jibrilsharafi/EnergyMe-Home/openspec/changes/unified-ap-sta-provisioning/specs/wifi-provisioning/spec.md

## ADDED Requirements

### Requirement: Provisioning never blocks the WiFi task

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

#### Scenario: Credential submission with a wrong password

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

#### Scenario: AP raised while STA is down

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

### Requirement: The device serves its web interface without an upstream network

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

#### Scenario: Unprovisioned first boot

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

#### Scenario: Health check during AP-only operation

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

### Requirement: The SoftAP is raised while the device is unreachable, and only then

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

#### Scenario: Successful provisioning

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

#### Scenario: Nobody ever connects

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

#### Scenario: Device loses its network permanently

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

#### Scenario: Unprovisioned device left alone

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

#### Scenario: The AP is lowered while the device is still unreachable

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

### Requirement: Local integrations are not exposed on the SoftAP

Unauthenticated local integration services SHALL NOT accept connections arriving on the SoftAP netif.

#### Scenario: Modbus TCP during provisioning

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

### Requirement: Credential changes do not restart the device

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

#### Scenario: SSID change from the UI

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

### Requirement: New credentials can always be stored, including on a device that cannot associate

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

#### Scenario: Correcting credentials on a device in AP-assist

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

#### Scenario: The driver rejects the write

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

#### Scenario: Static IP change

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

### Requirement: Provisioning routes are reachable from the AP without the web password when unprovisioned

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

#### Scenario: Captive portal on first boot

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

#### Scenario: In-service device that lost its network

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

#### Scenario: Request arriving on the STA netif

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

#### Scenario: Reading the log while provisioning fails

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

#### Scenario: Grace period after a successful connect

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

#### Scenario: Device's own loopback health probe

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

#### Scenario: LAN host routing to the AP address

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

### Requirement: Firmware update always requires authentication

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

#### Scenario: OTA attempt from the AP while unprovisioned

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

### Requirement: The DNS responder is confined to AP-only operation

The catch-all DNS responder SHALL run only while the SoftAP is raised and STA is disconnected, and SHALL be stopped once STA connects.

#### Scenario: STA connects while the AP is still up

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

#### Scenario: AP address changed by subnet-collision avoidance

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

### Requirement: The SoftAP subnet never overlaps the STA subnet

The SoftAP SHALL be assigned a subnet that does not overlap the STA subnet, because lwIP resolves an ambiguous route to the first matching interface and a later-added interface is prepended.

#### Scenario: Router uses the default AP subnet

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

#### Scenario: Restored backup carries a foreign static IP

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

#### Scenario: Radio brought up in AP+STA mode

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

#### Scenario: Collision appears after the AP is raised

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

### Requirement: The setup page tells the user where the meter went

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

#### Scenario: Credentials accepted

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

#### Scenario: Landing on the setup page

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

### Requirement: Connection diagnostics survive the removal of the configuration portal

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

#### Scenario: Diagnosing a failed association

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

#### Scenario: Wrong password during setup

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

### Requirement: Power-cut recovery does not raise the SoftAP

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

#### Scenario: Household power cut

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

## REMOVED Requirements

### Requirement: WiFi configuration through the WiFiManager captive portal

**Reason**: Replaced by provisioning served from the device's own web interface. The WiFiManager portal blocks the WiFi task, forces a restart on credential save, presents a second unrelated UI, and serves an unauthenticated firmware-upload page.

**Migration**: Provisioning moves to the device's own interface on the SoftAP. Stored credentials are unaffected; devices with valid credentials never raise the AP and see no change. The `/diagnostic` page is replaced by a diagnostics API endpoint. Users who relied on the portal's unauthenticated OTA now authenticate with the web password; a forgotten password is still recoverable with the 5 to 10 second button press.
