jibrilsharafi/EnergyMe-Home/openspec/changes/harden-ota-download/design.md

## Context

See proposal.md - Why. The constraints that shape the approach, all verified against the code and the pinned core rather than assumed:

- The OTA download was one call to `esp_https_ota()` in `_performOtaUpdate`, driven by `_otaTask`. The task self-deletes on every exit path (now through `_finishOtaTask()`). `_performOtaUpdate` has since moved to the granular `esp_https_ota_begin()` / `_perform()` / `_finish()` sequence so the signature and image-descriptor checks can run before activation; each attempt is still one begin-to-finish pass.
- `_publishOtaStatus` (mqtt.cpp) builds `statusDetails` as a JSON object with one `reason` key. AWS IoT `UpdateJobExecution` types `statusDetails` as a string-to-string map, keys up to 128 chars matching `[a-zA-Z0-9:_-]+`, values up to 1024 chars with no control characters. Sibling keys are therefore native, and every value must be rendered as a string.
- `calculateExponentialBackoff` (utils.cpp) already exists with the signature this change needs, but lives in `src/`, which the `native` test environment cannot compile.
- `source/lib/` already holds 15 pure modules. `version_compare` is the closest template: a namespaced pure module with a thin forwarder (`compareVersions()`) left behind in utils.cpp.
- The presigned URL is minted when the device picks up the job, not when the job is created, so the device owns the full 60 minute lifetime from its own start of work.

## Goals / Non-Goals

**Goals:**

- Make a transient or one-off download failure recoverable without a new job, since the presigned URL stays valid for an hour.
- Make a failed OTA self-describing, so the next investigation reads one job execution record instead of correlating telemetry against job timestamps.
- Keep the post-download flow (partition read, SHA256 capture, preferences write, reboot) untouched.

**Non-Goals:**

- Reducing steady-state internal-heap fragmentation. That is a separate reliability concern and is not addressed here.
- Guaranteeing a download succeeds on a device whose steady-state contiguous block sits below the mbedTLS requirement. On such a device this change converts a silent failure into a described one, nothing more.
- Treating the local web-UI OTA upload path (customserver.cpp `_handleOtaUploadData()` / `_initializeOtaUpload()` / `_finalizeOtaUpload()`). It runs on the `async_tcp` task, carries no TLS, and is out of scope.

## Decisions

### No publish suppression during the download

The originating issue proposes freeing internal RAM for the download by quiescing other work. Neither half of that survived examination.

Suspending the InfluxDB, custom MQTT, UDP log, web server and Modbus TCP tasks does not survive contact with the code: ESPAsyncWebServer and eModbus have no app-owned task and both run on AsyncTCP's single shared `async_tcp` task, which calls `esp_task_wdt_add(NULL)` by default, so suspending it panic-reboots the device mid-download. InfluxDB and custom MQTT are disabled by default and hold their buffers in PSRAM, as does the UDP log queue. `vTaskSuspend` frees nothing a task has already allocated in any case.

Suppressing MQTT publishes was implemented, reviewed, and then removed. Three things sank it:

- **The bytes are not there.** Every `JsonDocument` on the publish path is built with `SpiRamAllocator`, so the body is PSRAM. The only internal-RAM allocation a publish adds is a 256-byte `BufferingPrint`. The mbedTLS out buffer is already resident for the session, and on the pinned core `CONFIG_SPIRAM_TRY_ALLOCATE_WIFI_LWIP=y` puts the outgoing lwIP pbufs in PSRAM. The 16-20 KB per-publish dip that motivated this was measured on core 3.3.11, where that flag had been dropped; it does not transfer to the reverted pin.
- **The cost is real.** The meter and grid queues are drop-oldest and hold less than the worst-case retry window, so a long schedule loses queued points rather than delaying them.
- **The fleet was already healthy.** OTAs on this platform pin were fine before the bump. The one failure on the good core was a single device with a collapsed contiguous block, which publish suppression would not have fixed.

Worth recording because the first implementation was actively harmful, not merely useless: gating inside `_checkPublishMqtt` left the log queue publishing one message per entry, and left the `_checkIfPublish*Needed` checks running every 100 ms with their "already published" markers frozen, because only the suppressed publishers advance them. Each check then logged on every tick, and those logs queued and published. The gate turned a quiet window into a publish storm, and drove `_checkIfPublishCrashNeeded` into a 10 Hz LittleFS scan contending with the OTA partition writes. Any future attempt at quiescing has to sit above the whole publish section, not inside the publishers.

The levers that would actually move the contiguous block, none of them taken here: dropping the AWS MQTT TLS session for the window (16 KB in + 16 KB out), shrinking the 9 KB `MQTT_BUFFER_SIZE`, or `CONFIG_MBEDTLS_ASYMMETRIC_CONTENT_LEN` via `custom_sdkconfig` (12 KB per connection, at platform-bump-class risk).

### Retry in `_otaTask`, not inside `_performOtaUpdate`

The loop wraps `_performOtaUpdate` so the DNS probe (`_probeOtaHost()`, called once at the top of `_otaTask`) does not re-run on every attempt. That probe opens a plaintext `WiFiClient` to port 443 purely to log whether the host resolves, and repeating it per attempt would add a socket allocation to the very heap the change is trying to protect. Keeping the loop in `_otaTask` also leaves `_performOtaUpdate` as a single-attempt function that returns enough for the caller to report on.

`_performOtaUpdate` keeps returning `bool`, but the error, HTTP status, byte progress and heap figures land in a shared `OtaAttempt` that the HTTP event handler also writes into. The handler is a C callback with no context of its own, so shared state is unavoidable there; giving it one struct rather than four loose statics keeps the reset to a single assignment.

Each attempt performs its own `esp_https_ota_begin()` (and so its own `esp_ota_begin`), so a retry restarts the write from scratch. With `bulk_flash_erase = false` the partition is erased as it goes, so a retry re-erases what the failed attempt wrote. That is slower but correct, and no partial-image state survives between attempts.

### Backoff of 5 attempts, 2 min initial, x2, capped at 15 min

Delays are 2, 4, 8 and 15 minutes (the fourth doubling to 16 is clamped), for 29 minutes of cumulative waiting. Adding attempt durations puts the worst case near 44 minutes, inside the 60 minute presigned-URL lifetime with roughly 15 minutes of margin.

Chosen over a tighter schedule because the failure being defended against is heap pressure, which does not clear in seconds, and over a longer one because the URL lifetime is a hard ceiling. `multiplier = 2` also takes the existing helper's bit-shift branch rather than its loop.

No elapsed-time guard on the total, deliberately: a guard would add a failure mode without removing one. An expired URL is instead detected directly. The OTA API collapses every 4xx and 5xx into a bare `ESP_FAIL`, so the HTTP status is captured by `_captureOtaHttpStatus()` from the HTTP event handler (on data/finish/disconnect events, not `HTTP_EVENT_ON_HEADER`, which fires before the client assigns the status), and a 4xx breaks the schedule immediately rather than spending the remaining attempts on a URL that cannot succeed.

Attempt 1 runs immediately, so the delay for attempt N is the wait *before* attempt N+1. This keeps the mapping onto `calculateExponentialBackoff(attempt, ...)`, which already returns 0 for attempt 0.

### Discrete `statusDetails` keys, not a stringified JSON blob

`statusDetails` is natively a string-to-string map, so nesting encoded JSON inside one value would force a parser onto the infra side and lose queryability. Keys, with values rendered via `snprintf` into small `char` buffers:

| Key | Value |
|---|---|
| `reason` | `download_failed` for a generic download failure; `incomplete_download` when the connection closed before the full image arrived (#233); post-download rejections carry their own reason (`signature_invalid`, `image_incompatible:<verdict>`, `finish_failed`, ...) |
| `espError` | `esp_err_to_name()` of the final attempt's return |
| `httpStatus` | from the response headers; the only field that separates a server refusal from a transport or memory failure |
| `progress` | `"<bytesReceived>/<contentLength>"`, or `n/a` when the response did not carry firmware |
| `heapFreeMinMax` | internal-heap triple in one key, same sources as `populateSystemDynamicInfo()`; omitted when not sampled (deterministic post-download rejections, see below) |
| `attempts` | attempts made |
| `uptime` | seconds |
| `rssi` | dBm |

Up to eight keys. `espError` and `progress` carry the most diagnostic weight: today an allocation failure, a DNS failure, a TLS reject and a 404 all collapse into the same `download_failed` string, and there is no way to tell a download that died at 5% from one that died at 95%.

Heap figures are sampled immediately after the failing attempt returns, inside the loop. Sampling after the loop unwinds would record recovered heap and describe the wrong moment. They are sampled only for retryable failures (`_otaFailureRetryable`): download failures, plus transient local failures during signature verification (`hash_buffer_unavailable`, `partition_error`, `invalid_image_length`, `partition_read_error`, `hash_error`). A deterministic post-download rejection (`signature_invalid`, `pubkey_parse_error`, `image_incompatible:<verdict>`, `finish_failed`) abandons the schedule, already logs its specific cause, and has nothing for heap figures to explain, so `heapFreeMinMax` is omitted rather than reported as `0/0/0` (2008981). A DEBUG log line carries the heap figures at the start and end of every attempt, visible over UDP logs before the job status arrives.

Target version, checksum, job id and device id are excluded: AWS already holds all of them.

### Extract only the backoff schedule to `source/lib/`

A new `source/lib/backoff_schedule/` module holds the pure computation, mirroring `version_compare`: a namespaced pure function, with `calculateExponentialBackoff` in `utils.cpp` reduced to a forwarder so existing callers (`influxdbclient.cpp` and the new OTA loop) are untouched.

The remaining pure helpers in `utils.cpp` (`roundToDecimals`, `isValueInRange`, `isStringLengthValid`, `endsWith`, `startsWith`, `getContentTypeFromFilename`) stay where they are. Sweeping them out is a separate concern and would turn this into a mega-commit.

### Remove the dead pause/resume API

`Ade7953::pauseTasks()` / `resumeTasks()` (ade7953.cpp / ade7953.h) had no callers anywhere in the firmware. They were the nearest precedent for the task-suspension approach this change rejects, so leaving them in place invites a future reader to reach for a pattern that was evaluated and dropped.

## Risks / Trade-offs

- **A failed job now reports up to ~44 minutes after the download starts, instead of immediately.** → Accepted deliberately. The device publishes `IN_PROGRESS` when it accepts the job, so the execution is not silent in the meantime. If a job-level timeout is configured on the AWS side it must exceed the retry window, or the execution flips to `TIMED_OUT` before the device reports. Confirm the job's `timeoutConfig` before the first fleet job on this firmware.
- **A retry re-erases and rewrites the OTA partition each attempt.** → Flash wear across 5 attempts on a firmware image is negligible against the partition's endurance, and the alternative (resuming a partial image) needs state that the failure modes here do not justify.
- **Two devices could sit in a retry schedule while a fleet job rolls on.** → No mitigation needed; each execution is independent and the rollout's own failure thresholds still apply, just on a slower clock.
- **The OTA task now lives for up to ~44 minutes instead of one download.** → It holds a 12 KB stack and re-reads `_otaCurrentUrl` on every attempt, so `stop()` no longer frees that buffer while the task is alive and notifies the task to abandon its wait instead. Telemetry, logs and shadow updates all keep flowing throughout, so a device in a retry schedule looks entirely normal from the cloud apart from the pending job.
