jibrilsharafi/EnergyMe-Home/openspec/changes/archive/2026-07-05-grid-publish-minute-alignment/design.md

## Context

`_checkIfPublishGridNeeded()` and `_publishGrid()` live in `source/src/mqtt.cpp`, called from the MQTT task's connected-state loop (`_handleConnectedState()`), which itself ticks on a shared `ulTaskNotifyTake(pdTRUE, pdMS_TO_TICKS(MQTT_LOOP_INTERVAL))` (100 ms) alongside meter/systemDynamic/statistics/log/shadow processing. Grid points are sampled by a dedicated task (`ade7953.cpp`) that self-corrects its sleep to absolute `.000`/`.500` wall-clock boundaries every tick, so each point's own `unixTimeMs` is already exact regardless of when it is later published. Today's publish trigger is `millis64() - _lastMillisGridPublished > MQTT_MAX_INTERVAL_GRID_PUBLISH` (60 s), a relative timer with no relationship to
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
