jibrilsharafi/EnergyMe-Home/hardware/pcb/kicad/main_board/EASYEDA_MODELS/WIRELM-SMD_ESP32-S3-WROOM-1.step

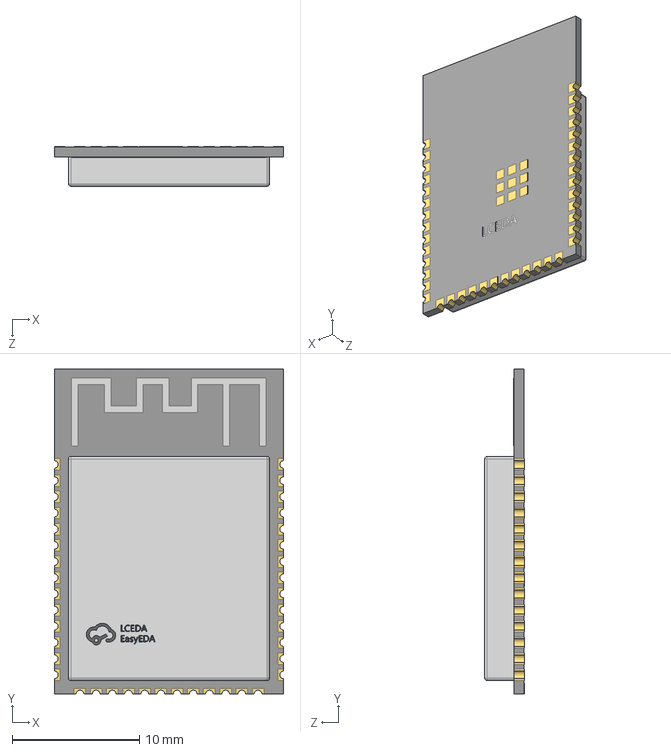
[picture p41: CAD file, 2026-09-05]
hardware/pcb/kicad/main_board/EASYEDA_MODELS/WIRELM-SMD_ESP32-S3-WROOM-1.step
18.0 x 25.5 x 3.11 mm
