jibrilsharafi/EnergyMe-Home/hardware/pcb/kicad/main_board/EASYEDA_MODELS/LFCSP-28_L5.0-W5.0-H0.8-P0.50.step

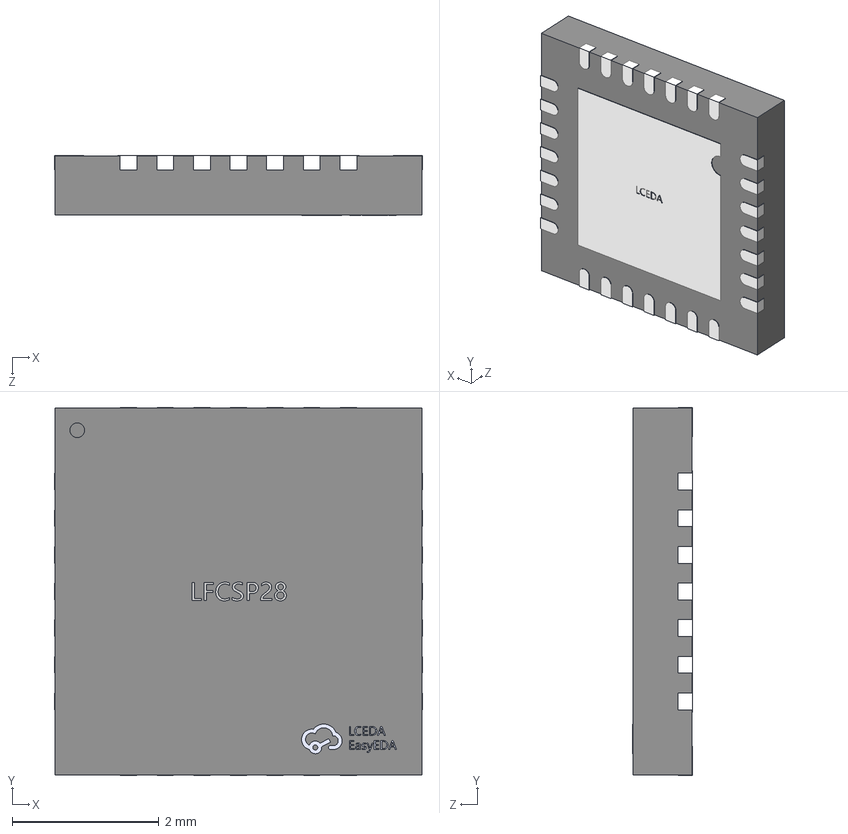
[picture p42: CAD file, 2026-09-05]
hardware/pcb/kicad/main_board/EASYEDA_MODELS/LFCSP-28_L5.0-W5.0-H0.8-P0.50.step
5.02 x 5.02 x 0.82 mm
