jibrilsharafi/EnergyMe-Home/hardware/pcb/kicad/main_board/EASYEDA_MODELS/R1206_L3.2-W1.6-H0.6.step

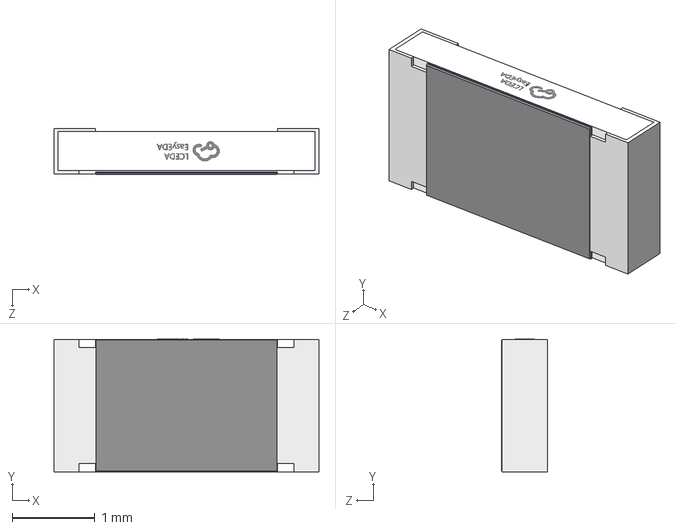
[picture p43: CAD file, 2026-09-05]
hardware/pcb/kicad/main_board/EASYEDA_MODELS/R1206_L3.2-W1.6-H0.6.step
3.20 x 1.60 x 0.56 mm
