jibrilsharafi/EnergyMe-Home/hardware/pcb/kicad/main_board/EASYEDA_MODELS/C2211_L5.7-W2.8-H1.5.step

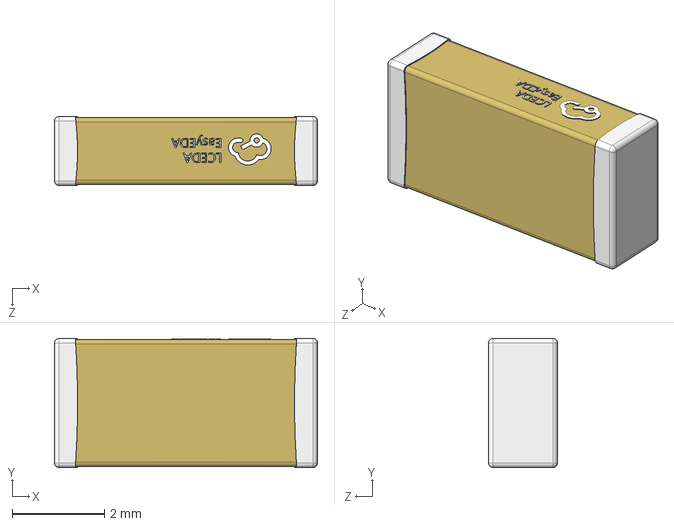
[picture p44: CAD file, 2026-09-05]
hardware/pcb/kicad/main_board/EASYEDA_MODELS/C2211_L5.7-W2.8-H1.5.step
5.70 x 2.80 x 1.50 mm
