jibrilsharafi/EnergyMe-Home/hardware/pcb/kicad/main_board/EASYEDA_MODELS/KEY-SMD_4P-L6.0-W6.0-H5.0-LS10.0-P4.50.step

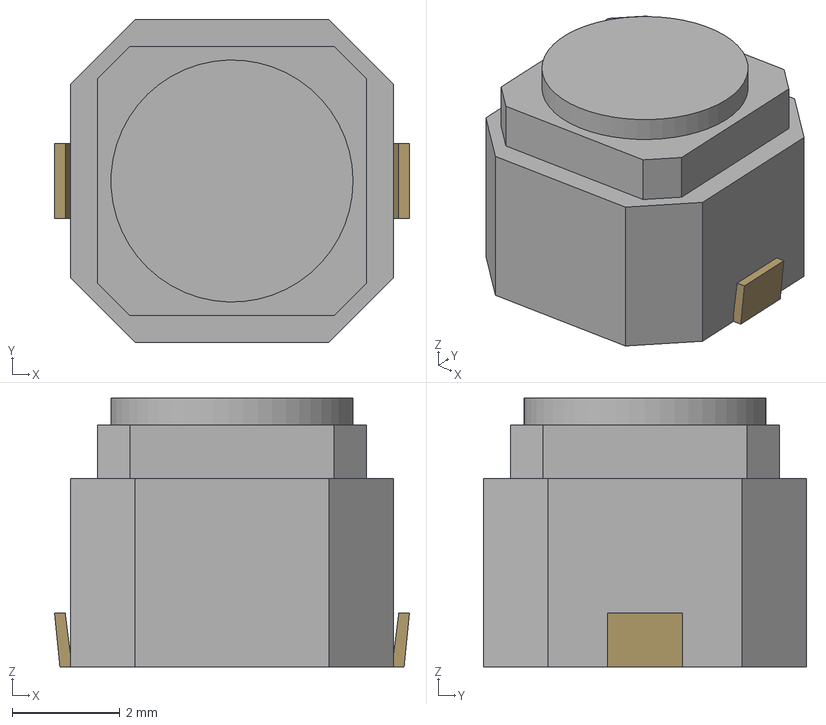
[picture p45: CAD file, 2026-09-05]
hardware/pcb/kicad/main_board/EASYEDA_MODELS/KEY-SMD_4P-L6.0-W6.0-H5.0-LS10.0-P4.50.step
6.60 x 6.00 x 5.00 mm
pin_1
pin_2
