jibrilsharafi/EnergyMe-Home/hardware/pcb/kicad/main_board/EASYEDA_MODELS/R0402_L1.0-W0.5-H0.4.step

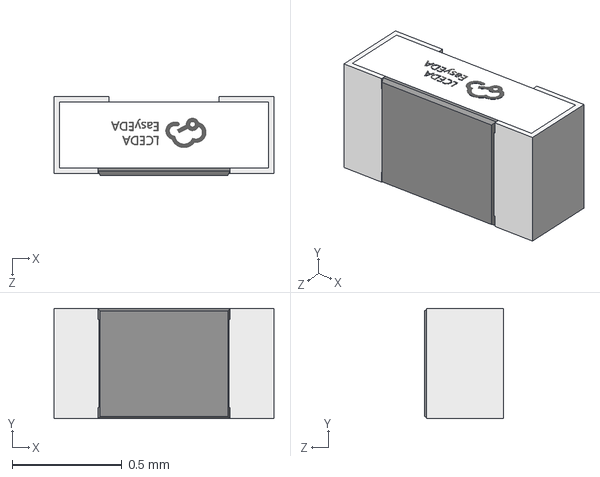
[picture p46: CAD file, 2026-09-05]
hardware/pcb/kicad/main_board/EASYEDA_MODELS/R0402_L1.0-W0.5-H0.4.step
1.00 x 0.501 x 0.36 mm
