jibrilsharafi/EnergyMe-Home/hardware/pcb/kicad/main_board/EASYEDA_MODELS/C0402_L1.0-W0.5-H0.5.step

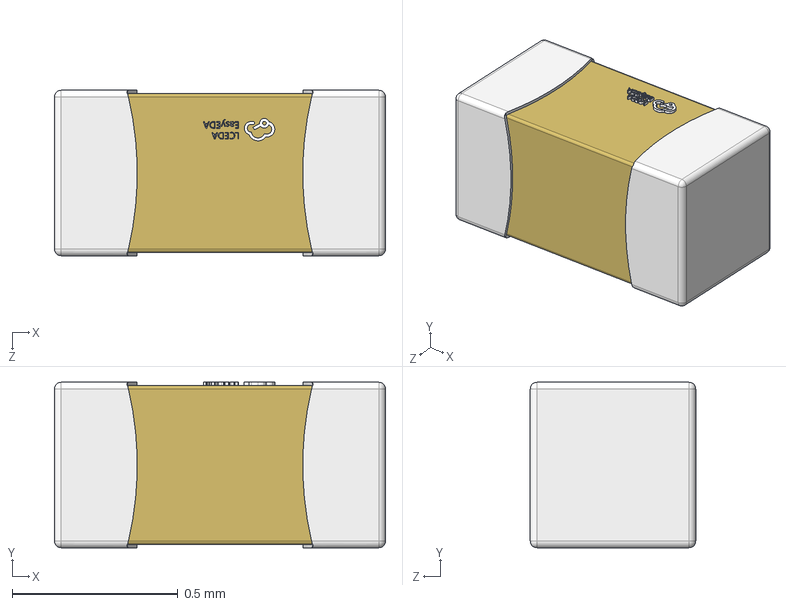
[picture p47: CAD file, 2026-09-05]
hardware/pcb/kicad/main_board/EASYEDA_MODELS/C0402_L1.0-W0.5-H0.5.step
1.00 x 0.5 x 0.5 mm
