jibrilsharafi/EnergyMe-Home/hardware/pcb/kicad/main_board/EASYEDA_MODELS/TSSOP-24_L7.8-W4.4-H1.0-LS6.4-P0.65.step

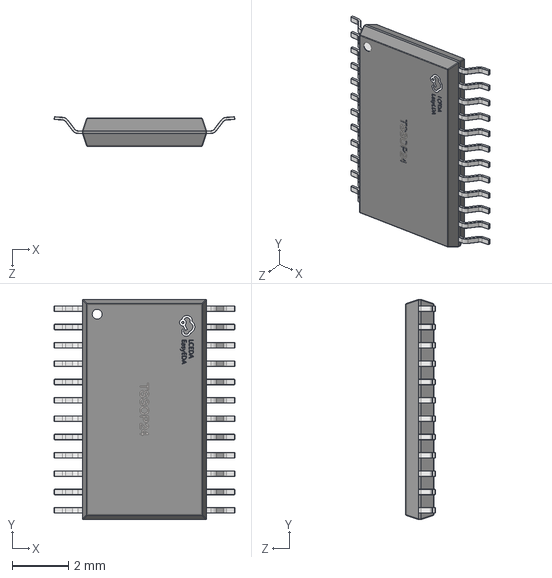
[picture p48: CAD file, 2026-09-05]
hardware/pcb/kicad/main_board/EASYEDA_MODELS/TSSOP-24_L7.8-W4.4-H1.0-LS6.4-P0.65.step
6.41 x 7.80 x 1.05 mm
