jibrilsharafi/EnergyMe-Home/manual/03-troubleshooting.md

# Troubleshooting

> *This chapter is a work in progress and will be expanded in future revisions of this manual.*

A full symptom-driven troubleshooting guide is being prepared. Anticipated sections:

- **LED behaviour** — what each colour and pattern means (cross-reference: [Appendix C](appendices.md#appendix-c-led-status-reference))
- **Wi-Fi & connectivity** — setup network doesn't appear, `energyme.local` unreachable, device drops off the network
- **Login & access** — forgot password, default credentials not accepted, temporarily locked out after repeated wrong passwords
- **Readings** — negative power values, no readings on a channel, branch sum greater than main, all zeros
- **CT placement** — symptoms suggesting a misclamped or inverted CT (cross-reference: the kettle test in [§4.7](02-setup.md#47-verification))
- **Reset procedures** — when and how to use restart, password reset, Wi-Fi reset, factory reset (cross-reference: [Appendix D](appendices.md#appendix-d-user-button-reference))
- **Firmware & updates** — update fails, the bell icon never appears, manual firmware upload
- **Hardware** — device unresponsive, CT not detected, jack issues

## In the meantime: how to get help

If you run into a problem that isn't covered elsewhere in this manual:

1. Check the **issues badge** in the top-right corner of the web interface. The device detects common problems on its own (e.g. a CT with the wrong polarity, over-temperature) and lists them there with a short explanation; channel-specific ones also appear on the **Channels** page.
2. Check the **[LED Status Reference (Appendix C)](appendices.md#appendix-c-led-status-reference)** — most installation issues are visible from the LED.
3. Try the **kettle test** described in [§4.7](02-setup.md#47-verification) to verify your wiring quickly.
4. Use the **button on the device** to recover from common situations (Wi-Fi reset, password reset); see [Appendix D](appendices.md#appendix-d-user-button-reference).
5. Compare your dashboard against the **[live demo](https://demo-energyme-home.energyme.net/)** to spot any obvious differences.

If none of the above helps, open a [GitHub issue](https://github.com/jibrilsharafi/EnergyMe-Home/issues) with:

- Your device's **batch number** (printed on the label inside the case)
- A clear description of the problem and what you have already tried
- A photograph or screenshot if relevant

We follow up on every issue and use real-world feedback to expand this troubleshooting chapter.

---

**Previous:** [← Setup](02-setup.md)  
**Next:** [Appendices →](appendices.md)
