jibrilsharafi/EnergyMe-Home/source/src/ade7953.cpp

// SPDX-License-Identifier: GPL-3.0-or-later
// Copyright (C) 2025 Jibril Sharafi

#include "ade7953.h"
#include "taskprofiler.h"
#include "duration_format.h"
#include "grid_frequency.h"
#include "mqtt.h"
#include "shadow_logic.h"

namespace Ade7953
{
    static TaskHeartbeat _meterReadingHeartbeat;
    static TaskHeartbeat _energySaveHeartbeat;
    static TaskHeartbeat _hourlyCsvHeartbeat;
    static TaskHeartbeat _gridSamplerHeartbeat;

    // Static variables
    // =========================================================
    // =========================================================
    
    // Hardware pins
    static uint8_t _ssPin;
    static uint8_t _sckPin;
    static uint8_t _misoPin;
    static uint8_t _mosiPin;
    static uint8_t _resetPin;
    static uint8_t _interruptPin;

    // Timing and measurement variables
    static uint64_t _sampleTime; // in milliseconds, time between linecycles readings
    static uint8_t _currentChannel = INVALID_CHANNEL; // By default, no channel is selected (except for channel 0 which is always active)
    // Dynamic channel scheduling state (Weighted Deficit Round-Robin)
    static float _channelWeight[MAX_CHANNEL_COUNT] = {};     // Computed dynamic weight per channel
    static float _channelDeficit[MAX_CHANNEL_COUNT] = {};    // Deficit counter for scheduling
    static float _prevActivePower[MAX_CHANNEL_COUNT] = {};   // Previous power reading for variability tracking
    static float _powerVariability[MAX_CHANNEL_COUNT] = {};  // EMA of |delta power| for variability scoring
    static uint8_t _wdrrCursor = 0;                          // Round-robin tie-break cursor for argmax
    static uint64_t _lastForcedPickMillis[MAX_CHANNEL_COUNT] = {}; // Starvation watchdog throttle, apart from lastMillis (the energy base). Guarded by _meterValuesMutex (64-bit, not atomic)
    static int8_t _polarityVoteCount[MAX_CHANNEL_COUNT] = {}; // Net consistent-sign vote accumulator for CT-reversal detection (runtime only; reset on arm/decision)
    static uint16_t _polarityConductingReads[MAX_CHANNEL_COUNT] = {}; // Conducting reads since arming - bounds a sign-oscillating channel (runtime only; reset on arm/decision)
    static bool _lastConducting[MAX_CHANNEL_COUNT] = {}; // Was the channel's most recent reading conducting (pre-clamp)? Drives the CT-detection boost so a clamped reversed load/PV still gets it (meter-task only)
    static float _gridFrequency = 50.0f; // Pre-EMA fallback, updated by the raw read in the channel-0 path

    // Per-cycle grid frequency EMA (issue #157), fed from the ZXV interrupt path.
    // Written only by the meter task; read lock-free (aligned 32-bit is atomic).
    static GridFrequency::State _gridFreqEma;
    static const GridFrequency::Config _gridFreqCfg = {GRID_FREQUENCY_CONVERSION_FACTOR, VALIDATE_GRID_FREQUENCY_MIN, VALIDATE_GRID_FREQUENCY_MAX};

    // The library returns MeterLogic::NO_CHANNEL for "no channel"; the firmware
    // compares scheduler results against its own INVALID_CHANNEL macro. They must
    // hold the same value. (The library cannot reuse the name INVALID_CHANNEL: it
    // is an object-like macro here and would rewrite MeterLogic::INVALID_CHANNEL.)
    static_assert(INVALID_CHANNEL == MeterLogic::NO_CHANNEL, "INVALID_CHANNEL / MeterLogic::NO_CHANNEL value mismatch");

    // Set by the meter task when the CT-reversal detector flips the persisted reverse flag.
    // Drained by the energy save task instead of writing NVS directly from the meter task,
    // keeping the hot meter-reading path free of flash I/O latency.
    static volatile bool _pendingPolaritySave[MAX_CHANNEL_COUNT] = {};

    // Issue-registry facts (issue #145), RAM-only and monotonic within this boot.
    // Single writer is the meter task; the registry tick reads them as 32-bit loads.
    static volatile uint32_t _factEvidenceReads[MAX_CHANNEL_COUNT] = {};
    static volatile uint32_t _factClampedEvidenceReads[MAX_CHANNEL_COUNT] = {};
    static volatile uint32_t _factPolarityFlipCount[MAX_CHANNEL_COUNT] = {};

    // Voltage-to-LSB conversion factors, computed once in begin() from globalHwProfile voltage divider.
    static float _voltPerLsb = 0.0f;
    static float _voltPerLsbInstantaneous = 0.0f;

    // Failure tracking
    static uint32_t _failureCount = 0;
    static uint64_t _firstFailureTime = 0;
    
    // Critical failure tracking (for missed interrupts)
    static uint32_t _criticalFailureCount = 0;
    static uint64_t _firstCriticalFailureTime = 0;

    // ZXTO suppression window (see _handleZxtoInterrupt). 0 = never triggered.
    static uint64_t _zxtoLastTriggerMs = 0;

    // Operational flags
    static bool _hasConfigurationChanged = false; // Flag to track if configuration has changed (needed since we will get an interrupt for CRC change)
    static bool _hasToSkipReading = true; // Flag to skip the first reading on Channel B after a mux switch so the contaminated (transition-spanning) window is discarded

    // Synchronization primitives
    static SemaphoreHandle_t _spiMutex = NULL; // To handle single SPI operations
    static SemaphoreHandle_t _spiOperationMutex = NULL; // To handle full SPI operations (like read with verification, which is 2 SPI operations)
    static SemaphoreHandle_t _ade7953InterruptSemaphore = NULL;
    static SemaphoreHandle_t _configMutex = NULL;
    static SemaphoreHandle_t _meterValuesMutex = NULL;
    static SemaphoreHandle_t _channelDataMutex = NULL;

    // FreeRTOS task handles and control flags
    static TaskHandle_t _meterReadingTaskHandle = NULL;
    static bool _meterReadingTaskShouldRun = false;
    
    static TaskHandle_t _energySaveTaskHandle = NULL;
    static bool _energySaveTaskShouldRun = false;
    
    static TaskHandle_t _hourlyCsvSaveTaskHandle = NULL;
    static bool _hourlyCsvSaveTaskShouldRun = false;

    static TaskHandle_t _gridSamplerTaskHandle = NULL;
    static bool _gridSamplerTaskShouldRun = false;

    static SemaphoreHandle_t _historyClearMutex = NULL;

    // Waveform capture state and buffers
    static CaptureState _captureState = CaptureState::IDLE;
    static uint8_t _captureRequestedChannel = INVALID_CHANNEL;
    static uint8_t _captureChannel = INVALID_CHANNEL;  // The channel being actively captured
    static uint16_t _captureSampleCount = 0;
    static uint64_t _captureStartUnixMillis = 0;
    static uint64_t _captureStartMicros = 0;  // Microseconds timestamp at capture start
    static int32_t* _voltageWaveformBuffer = nullptr;
    static int32_t* _currentWaveformBuffer = nullptr;
    static uint64_t* _microsWaveformBuffer = nullptr;  // Microseconds delta from start for each sample

    // Configuration and data arrays
    static Ade7953Configuration _configuration;
    MeterValues _meterValues[MAX_CHANNEL_COUNT];
    EnergyValues _energyValues[MAX_CHANNEL_COUNT]; // Store previous energy values for energy comparisons (optimize saving to flash)
    ChannelData _channelData[MAX_CHANNEL_COUNT];
    static uint16_t _lineFrequency = DEFAULT_FALLBACK_FREQUENCY; // Line frequency (fixed 50 or 60 Hz value)

    // Private function declarations
    // =========================================================
    // =========================================================

    // Hardware initialization and control
    static void _setHardwarePins(
        uint8_t ssPin,
        uint8_t sckPin,
        uint8_t misoPin,
        uint8_t mosiPin,
        uint8_t resetPin,
        uint8_t interruptPin
    );
    static void _reset();
    // According to the datasheet, setting these registers is mandatory for optimal operation
    static void _setOptimumSettings();
    static void _setDefaultParameters();

    // System management
    static void _initializeMutexes();
    static void _cleanup();
    static bool _verifyCommunication();

    // Interrupt handling
    static void _setupInterrupts();
    static void _handleInterrupt(uint64_t linecycUnix);
    static void _attachInterruptHandler();
    static void _detachInterruptHandler();
    static void IRAM_ATTR _isrHandler();
    static void _handleZxvInterrupt();
    static void _handleCycendInterrupt(uint64_t linecycUnix);
    static void _pollWaveformSamples();
    static void _handleCrcChangeInterrupt();
    static void _handleResetInterrupt();
    static void _handleZxtoInterrupt();

    // Task management
    static void _startMeterReadingTask();
    static void _stopMeterReadingTask();
    static void _meterReadingTask(void* parameter);

    static void _startEnergySaveTask();
    static void _stopEnergySaveTask();
    static void _energySaveTask(void* parameter);

    static void _startHourlyCsvSaveTask();
    static void _stopHourlyCsvSaveTask();
    static void _hourlyCsvSaveTask(void* parameter);

    static void _startGridSamplerTask();
    static void _stopGridSamplerTask();
    static void _gridSamplerTask(void* parameter);

    static void _historyClearTask(void* parameter);
    static void _spawnHistoryClearTask(uint8_t channelIndex);
    static void _clearAllHistoricalData();

    // Configuration management
    static void _seedConfigurationFromFactory();
    static void _setConfigurationFromPreferences();
    static void _saveConfigurationToPreferences();
    static void _applyConfiguration(const Ade7953Configuration &config); // Apply all the single register values from the configuration
    static bool _validateJsonConfiguration(const JsonDocument &jsonDocument, bool partial = false);

    // Channel data management
    static void _setChannelDataFromPreferences(uint8_t channelIndex);
    static bool _saveChannelDataToPreferences(uint8_t channelIndex);
    static void _updateChannelData(uint8_t channelIndex);
    static bool _validateChannelDataJson(const JsonDocument &jsonDocument, bool partial = false);
    static void _calculateLsbValues(CtSpecification &ctSpec);

    // Energy data management
    static void _setEnergyFromPreferences(uint8_t channelIndex);
    static void _saveEnergyToPreferences(uint8_t channelIndex, bool forceSave = false); // Needed for saving data anyway on first setup (energy is 0 and not saved otherwise)
    static void _clearStartMeasuring(uint8_t channelIndex); // reset back to 0 (unset) on every reset
    static void _saveHourlyEnergyToCsv(); // Not per channel so that we open the file only once
    static void _saveEnergyComplete();
    static bool _clearChannelHistoricalData(uint8_t channelIndex);

    // Meter reading and processing
    static bool _readMeterValues(uint8_t channelIndex, uint64_t linecycUnixTime);
    static bool _processChannelReading(uint8_t channelIndex, uint64_t linecycUnix);
    static void _addMeterDataToPayload(uint8_t channelIndex);

    // ADE7953 register writing functions
    static void _setLinecyc(uint32_t linecyc);
    static void _setPgaGain(int32_t pgaGain, Ade7953Channel ade7953Channel, MeasurementType measurementType);
    static void _setPhaseCalibration(int32_t phaseCalibration, Ade7953Channel ade7953Channel);
    static void _setGain(int32_t gain, Ade7953Channel ade7953Channel, MeasurementType measurementType);
    static void _setOffset(int32_t offset, Ade7953Channel ade7953Channel, MeasurementType measurementType);

    // Sample time management
    static void _updateSampleTime();
    static void _setSampleTimeFromPreferences();
    static void _saveSampleTimeToPreferences();

    // ADE7953 register reading functions
    /*
    This allows you see the actual sinusoidal waveform, so both positive and 
    negative values. At full scale (so 500 mV), the value returned is 9032007d.

    @param channel The channel to read from. Either CHANNEL_A or CHANNEL_B.
    @return The actual instantaneous current in LSB.
    */
    static int32_t _readCurrentInstantaneous(Ade7953Channel ade7953Channel);
    /*
    Reads the actual instantaneous voltage. 

    This allows you 
    to see the actual sinusoidal waveform, so both positive
    and negative values. At full scale (so 500 mV), the value
    returned is 9032007d.

    @return The actual instantaneous voltage in LSB.
    */
    static int32_t _readVoltageInstantaneous();
    /*
    Reads the current in RMS.

    This measurement is updated at 6.99 kHz and has a settling
    time of 200 ms. The value is in LSB.

    @param channel The channel to read from. Either CHANNEL_A or CHANNEL_B.
    @return The current in RMS in LSB.
    */
    static int32_t _readCurrentRms(Ade7953Channel ade7953Channel);
    /*
    Reads the voltage in RMS.

    This measurement is updated at 6.99 kHz and has a settling
    time of 200 ms. The value is in LSB.

    @return The voltage in RMS in LSB.
    */
    static int32_t _readVoltageRms();
    static int32_t _readActiveEnergy(Ade7953Channel ade7953Channel);
    static int32_t _readReactiveEnergy(Ade7953Channel ade7953Channel);
    static int32_t _readApparentEnergy(Ade7953Channel ade7953Channel);
    static int32_t _readPeriod();
    static float _readGridFrequency();

    // Verification and validation functions
    static void _recordFailure();
    static void _checkForTooManyFailures();
    static void _recordCriticalFailure();
    static void _checkForTooManyCriticalFailures();
    static bool _verifyLastSpiCommunication(uint16_t expectedAddress, uint8_t expectedBits, int32_t expectedData, bool signedData, bool wasWrite);
    static bool _validateVoltage(float newValue);
    static bool _validateCurrent(float newValue);
    static bool _validatePower(float newValue);
    static bool _validatePowerFactor(float newValue);
    static bool _validateGridFrequency(float newValue);

    // Utility functions
    static void _recalculateWeights();
    static void _updateVariability(uint8_t channelIndex, float newActivePower);
    static uint8_t _findNextActiveChannel(uint8_t currentChannel);
    float _calculatePhaseShift(Phase voltagePhase, Phase currentPhase);
    // Returns the string name of the IRQSTATA bit, or UNKNOWN if the bit is not recognized.
    static const char *_irqstataBitName(uint32_t bit);
    void _printMeterValues(uint8_t channelIndex);


    // Public API functions
    // =========================================================
    // =========================================================

    // Core lifecycle management
    // =========================

    bool begin(
        uint8_t ssPin,
        uint8_t sckPin,
        uint8_t misoPin,
        uint8_t mosiPin,
        uint8_t resetPin,
        uint8_t interruptPin
    ) {
        LOG_DEBUG("Initializing Ade7953");

        _initializeMutexes();
        LOG_DEBUG("Initialized SPI mutexes");

        // Allocate PSRAM buffers for waveform capture
        _voltageWaveformBuffer = (int32_t*)ps_malloc(WAVEFORM_BUFFER_SIZE * sizeof(int32_t));
        _currentWaveformBuffer = (int32_t*)ps_malloc(WAVEFORM_BUFFER_SIZE * sizeof(int32_t));
        _microsWaveformBuffer = (uint64_t*)ps_malloc(WAVEFORM_BUFFER_SIZE * sizeof(uint64_t));

        if (!_voltageWaveformBuffer || !_currentWaveformBuffer || !_microsWaveformBuffer) {
            LOG_ERROR("Failed to allocate waveform buffers from PSRAM");
            _captureState = CaptureState::ERROR;
            // Continue initialization - waveform capture just won't be available
        } else {
            LOG_DEBUG("Allocated waveform buffers in PSRAM (%u samples)", WAVEFORM_BUFFER_SIZE);
        }
      
        _setHardwarePins(ssPin, sckPin, misoPin, mosiPin, resetPin, interruptPin);
        LOG_DEBUG("Successfully set up hardware pins");

        // Compute voltage-per-LSB from the hardware profile's voltage divider values.
        // ratio = R2 / (R1 + R2), the fraction of the mains voltage seen by the ADE7953 input.
        const float ratio = globalHwProfile->voltageDividerR2 / (globalHwProfile->voltageDividerR1 + globalHwProfile->voltageDividerR2);
        _voltPerLsb             = (MAXIMUM_ADC_CHANNEL_INPUT / 1.41421356f) / ratio / static_cast<float>(FULL_SCALE_LSB_FOR_RMS_VALUES);
        _voltPerLsbInstantaneous = MAXIMUM_ADC_CHANNEL_INPUT / ratio / static_cast<float>(FULL_SCALE_LSB_FOR_INSTANTANEOUS_VALUES);

        if (!_verifyCommunication()) {
            LOG_ERROR("Failed to communicate with ADE7953");
            return false;
        }
        LOG_DEBUG("Communication with ADE7953 verified");
                
        _setOptimumSettings();
        LOG_DEBUG("Set optimum settings");
        
        _setDefaultParameters();
        LOG_DEBUG("Set default parameters");

        _seedConfigurationFromFactory();
        _setConfigurationFromPreferences();
        LOG_DEBUG("Done setting configuration from Preferences");

        _setSampleTimeFromPreferences();
        LOG_DEBUG("Done setting sample time from Preferences");

        for (uint8_t i = 0; i < globalHwProfile->totalChannelCount; i++) {
            _setChannelDataFromPreferences(i);
        }
        LOG_DEBUG("Done setting channel data from Preferences");

        for (uint8_t i = 0; i < globalHwProfile->totalChannelCount; i++) {
            _setEnergyFromPreferences(i);
        }
        LOG_DEBUG("Done setting energy from Preferences");

        _setupInterrupts();
        LOG_DEBUG("Set up interrupts");

        _startMeterReadingTask();
        LOG_DEBUG("Meter reading task started");

        _startEnergySaveTask();
        LOG_DEBUG("Energy save task started");

        _startHourlyCsvSaveTask();
        LOG_DEBUG("Hourly CSV save task started");

        _startGridSamplerTask();
        LOG_DEBUG("Grid sampler task started");

        return true;
    }

    void stop() {
        LOG_DEBUG("Stopping ADE7953...");
        
        // Clean up resources (where the data will also be saved)
        _cleanup();

        // Mutexes are kept: Modbus, MQTT and web handlers can still be inside getters while the
        // restart sequence runs, and deleting a mutex in use trips a FreeRTOS assert. A reboot follows.
        
        LOG_DEBUG("ADE7953 stopped successfully");
    }

    // Register operations
    // ===================

    int32_t readRegister(uint16_t registerAddress, uint8_t nBits, bool signedData, bool isVerificationRequired) {
        // Ensure the bits are valid (must be 8, 16, 24, or 32 bits)
        if (nBits != BIT_8 && nBits != BIT_16 && nBits != BIT_24 && nBits != BIT_32) {
            LOG_ERROR(
                "Invalid number of bits (%u) for register read operation on register %ld (0x%04lX)",
                nBits, registerAddress, registerAddress
            );
            return INVALID_SPI_READ_WRITE; // Return an invalid value
        }

        // If we need to verify, ensure we are able to take the full SPI operation mutex
        if (isVerificationRequired) {
            if (!acquireMutex(&_spiOperationMutex, ADE7953_SPI_OPERATION_MUTEX_TIMEOUT_MS)) {
                LOG_ERROR("Failed to acquire SPI operation mutex for read operation on register %ld (0x%04lX)", registerAddress, registerAddress);
                return INVALID_SPI_READ_WRITE;
            }
        }

        // Acquire direct SPI mutex
        if (!acquireMutex(&_spiMutex, ADE7953_SPI_MUTEX_TIMEOUT_MS)) {
            LOG_ERROR("Failed to acquire SPI mutex for read operation on register %ld (0x%04lX)", registerAddress, registerAddress);
            if (isVerificationRequired) releaseMutex(&_spiOperationMutex);
            return INVALID_SPI_READ_WRITE;
        }

        // Signal the start of the SPI operation
        digitalWrite(_ssPin, LOW);

        // Send the register address (two 8-bit transfers) and read command
        // Note: The register address is sent in big-endian format (MSB first)
        SPI.transfer((uint8_t)(registerAddress >> 8));
        SPI.transfer((uint8_t)(registerAddress & 0xFF));
        SPI.transfer((uint8_t)(READ_TRANSFER));

        // Create the array of bytes to read (one element per each 8 bits)
        uint8_t response[nBits / 8];
        for (uint8_t i = 0; i < nBits / 8; i++) {
            response[i] = SPI.transfer((uint8_t)(READ_TRANSFER)); // Read the data byte by byte
        }

        // Signal the end of the SPI operation
        digitalWrite(_ssPin, HIGH);

        releaseMutex(&_spiMutex); // Leave as soon as possible since no more direct SPI operations are needed

        // Compose the raw response from the byte array
        uint32_t rawResponse = 0;
        for (uint8_t i = 0; i < nBits / 8; i++) {
            rawResponse = (rawResponse << 8) | response[i];
        }

        int32_t longResponse = signedData ? MeterLogic::signExtendRegister(rawResponse, nBits) : (int32_t)rawResponse;

        // Verify the data if required by reading the dedicated ADE7953 register
        if (isVerificationRequired) {
            if (!_verifyLastSpiCommunication(registerAddress, nBits, longResponse, signedData, false)) {
                LOG_DEBUG("Failed to verify last read communication for register %lu (0x%04lX). Value was %ld (0x%04lX)", registerAddress, registerAddress, longResponse, longResponse);
                _recordFailure();
                longResponse = INVALID_SPI_READ_WRITE; // Return an invalid value if verification fails
            }
            releaseMutex(&_spiOperationMutex);
        }

        LOG_VERBOSE(
            "Read successfully %ld from register %lu with %u bits",
            longResponse,
            registerAddress,
            nBits
        );
        return longResponse;
    }

    void writeRegister(uint16_t registerAddress, uint8_t nBits, int32_t data, bool isVerificationRequired) {
        // Ensure the bits are valid (must be 8, 16, 24, or 32 bits)
        if (nBits != BIT_8 && nBits != BIT_16 && nBits != BIT_24 && nBits != BIT_32) {
            LOG_ERROR(
                "Invalid number of bits (%u) for register write operation on register %ld (0x%04lX)",
                nBits, registerAddress, registerAddress
            );
            return; // Return an invalid value
        }

        // If we need to verify, ensure we are able to take the full SPI operation mutex
        if (isVerificationRequired) {
            if (!acquireMutex(&_spiOperationMutex, ADE7953_SPI_OPERATION_MUTEX_TIMEOUT_MS)) {
                LOG_ERROR("Failed to acquire SPI operation mutex for read operation on register %ld (0x%04lX)", registerAddress, registerAddress);
                return;
            }
        }

        // Acquire direct SPI mutex
        if (!acquireMutex(&_spiMutex, ADE7953_SPI_MUTEX_TIMEOUT_MS)) {
            LOG_ERROR("Failed to acquire SPI mutex for write operation on register %ld (0x%04lX)", registerAddress, registerAddress);
            if (isVerificationRequired) releaseMutex(&_spiOperationMutex);
            return;
        }

        // Signal the start of the SPI operation
        digitalWrite(_ssPin, LOW);

        // Send the register address (two 8-bit transfers) and write command
        // Note: The register address is sent in big-endian format (MSB first)
        SPI.transfer((uint8_t)(registerAddress >> 8));
        SPI.transfer((uint8_t)(registerAddress & 0xFF));
        SPI.transfer((uint8_t)(WRITE_TRANSFER));

        // Send the data to write, depending on the number of bits
        // Note: The data is sent in big-endian format (MSB first)
        if (nBits == BIT_32) {
            SPI.transfer((uint8_t)((data >> 24) &  0xFF));
            SPI.transfer((uint8_t)((data >> 16) & 0xFF));
            SPI.transfer((uint8_t)((data >> 8) & 0xFF));
            SPI.transfer((uint8_t)(data & 0xFF));
        } else if (nBits == BIT_24) {
            SPI.transfer((uint8_t)((data >> 16) & 0xFF));
            SPI.transfer((uint8_t)((data >> 8) & 0xFF));
            SPI.transfer((uint8_t)(data & 0xFF));
        } else if (nBits == BIT_16) {
            SPI.transfer((uint8_t)((data >> 8) & 0xFF));
            SPI.transfer((uint8_t)(data & 0xFF));
        } else if (nBits == BIT_8) {
            SPI.transfer((uint8_t)(data & 0xFF));
        } else {
            LOG_ERROR("Invalid number of bits (%u) for register write operation on register %ld (0x%04lX)", nBits, registerAddress, registerAddress);
            digitalWrite(_ssPin, HIGH); // Ensure we release the SS pin
            releaseMutex(&_spiMutex);
            if (isVerificationRequired) releaseMutex(&_spiOperationMutex);
            return; // Return without writing
        }

        // Signal the end of the SPI operation
        digitalWrite(_ssPin, HIGH);

        releaseMutex(&_spiMutex);

        // Verify the data if required by reading the dedicated ADE7953 register
        if (isVerificationRequired) {
            if (!_verifyLastSpiCommunication(registerAddress, nBits, data, false, true)) {
                LOG_WARNING("Failed to verify last write communication for register %ld", registerAddress);
                _recordFailure();
            }
            releaseMutex(&_spiOperationMutex);
        }

        // When writing a register, we inherently change the configuration and thus trigger a CRC change interrupt
        _hasConfigurationChanged = true;

        LOG_DEBUG(
            "Written successfully %ld (0x%04lX) to register %lu (0x%04lX) with %u bits",
            data, data,
            registerAddress, registerAddress,
            nBits
        );
    }

    // Configuration management
    // ========================

    void getConfiguration(Ade7953Configuration &config) {
        config = _configuration;
    }

    bool setConfiguration(const Ade7953Configuration &config) {
        if (!acquireMutex(&_configMutex, CONFIG_MUTEX_TIMEOUT_MS)) {
            LOG_ERROR("Failed to acquire config mutex for setConfiguration");
            return false;
        }

        _configuration = config;
        _applyConfiguration(_configuration);
        
        _saveConfigurationToPreferences();
        
        releaseMutex(&_configMutex);

        LOG_DEBUG("Configuration set successfully");
        return true;
    }

    void resetConfiguration() {
        LOG_DEBUG("Resetting ADE7953 configuration to defaults...");

        Ade7953Configuration defaultConfig;
        setConfiguration(defaultConfig);
    }

    // Configuration management - JSON operations
    // ==========================================

    void getConfigurationAsJson(JsonDocument &jsonDocument) {
        configurationToJson(_configuration, jsonDocument);
    }

    bool setConfigurationFromJson(const JsonDocument &jsonDocument, bool partial)
    {
        Ade7953Configuration config;
        config = _configuration; // Start with current configuration
        if (!configurationFromJson(jsonDocument, config, partial)) {
            LOG_ERROR("Failed to set configuration from JSON");
            return false;
        }

        return setConfiguration(config);
    }

    void configurationToJson(const Ade7953Configuration &config, JsonDocument &jsonDocument)
    {
        jsonDocument["aVGain"] = config.aVGain;
        jsonDocument["aIGain"] = config.aIGain;
        jsonDocument["bIGain"] = config.bIGain;
        jsonDocument["aIRmsOs"] = config.aIRmsOs;
        jsonDocument["bIRmsOs"] = config.bIRmsOs;
        jsonDocument["aWGain"] = config.aWGain;
        jsonDocument["bWGain"] = config.bWGain;
        jsonDocument["aWattOs"] = config.aWattOs;
        jsonDocument["bWattOs"] = config.bWattOs;
        jsonDocument["aVarGain"] = config.aVarGain;
        jsonDocument["bVarGain"] = config.bVarGain;
        jsonDocument["aVarOs"] = config.aVarOs;
        jsonDocument["bVarOs"] = config.bVarOs;
        jsonDocument["aVaGain"] = config.aVaGain;
        jsonDocument["bVaGain"] = config.bVaGain;
        jsonDocument["aVaOs"] = config.aVaOs;
        jsonDocument["bVaOs"] = config.bVaOs;
        jsonDocument["phCalA"] = config.phCalA;
        jsonDocument["phCalB"] = config.phCalB;

        LOG_DEBUG("Successfully converted configuration to JSON");
    }

    bool configurationFromJson(const JsonDocument &jsonDocument, Ade7953Configuration &config, bool partial)
    {
        if (!_validateJsonConfiguration(jsonDocument, partial))
        {
            LOG_WARNING("Invalid JSON configuration");
            return false;
        }

        if (partial) {
            // Update only fields that are present in JSON
            if (jsonDocument["aVGain"].is<int32_t>()) config.aVGain = jsonDocument["aVGain"].as<int32_t>();
            if (jsonDocument["aIGain"].is<int32_t>()) config.aIGain = jsonDocument["aIGain"].as<int32_t>();
            if (jsonDocument["bIGain"].is<int32_t>()) config.bIGain = jsonDocument["bIGain"].as<int32_t>();
            if (jsonDocument["aIRmsOs"].is<int32_t>()) config.aIRmsOs = jsonDocument["aIRmsOs"].as<int32_t>();
            if (jsonDocument["bIRmsOs"].is<int32_t>()) config.bIRmsOs = jsonDocument["bIRmsOs"].as<int32_t>();
            if (jsonDocument["aWGain"].is<int32_t>()) config.aWGain = jsonDocument["aWGain"].as<int32_t>();
            if (jsonDocument["bWGain"].is<int32_t>()) config.bWGain = jsonDocument["bWGain"].as<int32_t>();
            if (jsonDocument["aWattOs"].is<int32_t>()) config.aWattOs = jsonDocument["aWattOs"].as<int32_t>();
            if (jsonDocument["bWattOs"].is<int32_t>()) config.bWattOs = jsonDocument["bWattOs"].as<int32_t>();
            if (jsonDocument["aVarGain"].is<int32_t>()) config.aVarGain = jsonDocument["aVarGain"].as<int32_t>();
            if (jsonDocument["bVarGain"].is<int32_t>()) config.bVarGain = jsonDocument["bVarGain"].as<int32_t>();
            if (jsonDocument["aVarOs"].is<int32_t>()) config.aVarOs = jsonDocument["aVarOs"].as<int32_t>();
            if (jsonDocument["bVarOs"].is<int32_t>()) config.bVarOs = jsonDocument["bVarOs"].as<int32_t>();
            if (jsonDocument["aVaGain"].is<int32_t>()) config.aVaGain = jsonDocument["aVaGain"].as<int32_t>();
            if (jsonDocument["bVaGain"].is<int32_t>()) config.bVaGain = jsonDocument["bVaGain"].as<int32_t>();
            if (jsonDocument["aVaOs"].is<int32_t>()) config.aVaOs = jsonDocument["aVaOs"].as<int32_t>();
            if (jsonDocument["bVaOs"].is<int32_t>()) config.bVaOs = jsonDocument["bVaOs"].as<int32_t>();
            if (jsonDocument["phCalA"].is<int32_t>()) config.phCalA = jsonDocument["phCalA"].as<int32_t>();
            if (jsonDocument["phCalB"].is<int32_t>()) config.phCalB = jsonDocument["phCalB"].as<int32_t>();
        } else {
            // Full update - set all fields
            config.aVGain = jsonDocument["aVGain"].as<int32_t>();
            config.aIGain = jsonDocument["aIGain"].as<int32_t>();
            config.bIGain = jsonDocument["bIGain"].as<int32_t>();
            config.aIRmsOs = jsonDocument["aIRmsOs"].as<int32_t>();
            config.bIRmsOs = jsonDocument["bIRmsOs"].as<int32_t>();
            config.aWGain = jsonDocument["aWGain"].as<int32_t>();
            config.bWGain = jsonDocument["bWGain"].as<int32_t>();
            config.aWattOs = jsonDocument["aWattOs"].as<int32_t>();
            config.bWattOs = jsonDocument["bWattOs"].as<int32_t>();
            config.aVarGain = jsonDocument["aVarGain"].as<int32_t>();
            config.bVarGain = jsonDocument["bVarGain"].as<int32_t>();
            config.aVarOs = jsonDocument["aVarOs"].as<int32_t>();
            config.bVarOs = jsonDocument["bVarOs"].as<int32_t>();
            config.aVaGain = jsonDocument["aVaGain"].as<int32_t>();
            config.bVaGain = jsonDocument["bVaGain"].as<int32_t>();
            config.aVaOs = jsonDocument["aVaOs"].as<int32_t>();
            config.bVaOs = jsonDocument["bVaOs"].as<int32_t>();
            config.phCalA = jsonDocument["phCalA"].as<int32_t>();
            config.phCalB = jsonDocument["phCalB"].as<int32_t>();
        }

        LOG_DEBUG("Successfully converted JSON to configuration%s", partial ? " (partial)" : "");
        return true;
    }

    // Sample time management
    // ======================

    uint64_t getSampleTime() { 
        return _sampleTime; 
    }

    bool setSampleTime(uint64_t sampleTime) {
        if (sampleTime < MINIMUM_SAMPLE_TIME) {
            LOG_WARNING("Sample time %llu is below minimum %llu", sampleTime, MINIMUM_SAMPLE_TIME);
            return false;
        }

        _sampleTime = sampleTime;
        _updateSampleTime();
        _saveSampleTimeToPreferences();

        return true;
    }

    // Channel data management
    // =======================

    bool isChannelActive(uint8_t channelIndex) {
        if (channelIndex == INVALID_CHANNEL) return false; // Invalid (and expected to be) channel, thus no logs

        if (!isChannelValid(channelIndex)) {
            LOG_WARNING("Channel index out of bounds: %lu", channelIndex);
            return false;
        }

        return _channelData[channelIndex].active;
    }

    bool hasChannelValidMeasurements(uint8_t channelIndex) {
        if (!isChannelValid(channelIndex)) {
            LOG_WARNING("Channel index out of bounds: %lu", channelIndex);
            return false;
        }

        return CustomTime::isUnixTimeValid(_meterValues[channelIndex].lastUnixTimeMilliseconds);
    }

    void getChannelLabel(uint8_t channelIndex, char* buffer, size_t bufferSize) {
        if (!isChannelValid(channelIndex)) {
            LOG_WARNING("Channel index out of bounds: %lu", channelIndex);
            return;
        }

        ChannelData channelData(channelIndex);
        getChannelData(channelData, channelIndex);

        snprintf(buffer, bufferSize, "%s", channelData.label); // Fallback is the default constructor value if getChannelData failed
    }

    bool getChannelData(ChannelData &channelData, uint8_t channelIndex) {
        if (!isChannelValid(channelIndex)) {
            LOG_WARNING("Channel index out of bounds: %lu", channelIndex);
            return false;
        }

        if (!acquireMutex(&_channelDataMutex)) {
            LOG_ERROR("Failed to acquire mutex for channel data");
            return false;
        }

        channelData = _channelData[channelIndex];
        releaseMutex(&_channelDataMutex);
        return true;
    }

    bool setChannelData(const ChannelData &channelData, uint8_t channelIndex, bool* roleChanged, bool armTransients) {
        if (!isChannelValid(channelIndex)) {
            LOG_WARNING("Channel index out of bounds: %lu", channelIndex);
            return false;
        }

        // Snapshot old role, active state, reverse flag and phase before applying new data
        ChannelRole oldRole = _channelData[channelIndex].role;
        bool wasInactive = !_channelData[channelIndex].active;
        bool oldReverse = _channelData[channelIndex].reverse;
        Phase oldPhase = _channelData[channelIndex].phase;

        // Baseline lastMillis on inactive->active BEFORE the channel can be scheduled:
        // otherwise its first read integrates P over the whole inactive span from the
        // stale pre-deactivation stamp. It also gives the watchdog a zero point for a
        // channel whose first read fails.
        // Done ahead of _channelDataMutex since the two mutexes are never held together;
        // a baseline left behind by a write that then fails is harmless (still inactive).
        if (channelIndex > 0 && wasInactive && channelData.active) {
            if (!acquireMutex(&_meterValuesMutex)) {
                LOG_ERROR("Failed to acquire mutex for meter values");
                return false;
            }
            _meterValues[channelIndex].lastMillis = millis64();
            releaseMutex(&_meterValuesMutex);
        }

        if (!acquireMutex(&_channelDataMutex)) {
            LOG_ERROR("Failed to acquire mutex for channel data");
            return false;
        }

        // Protect channel 0 from being disabled
        if (channelIndex == 0 && !channelData.active) {
            LOG_WARNING("Attempt to disable channel 0 blocked - channel 0 must remain active");
            _channelData[channelIndex].active = true;
        } else {
            _channelData[channelIndex] = channelData;
        }

        // Last line of defence for the voltage reference (see _isValidReferencePhase).
        // The JSON validators reject this at the API, but a device that already stored
        // it in NVS restores through here with armTransients=false, so coerce rather
        // than reject: the alternative is a boot loop on a config the user cannot see.
        if (channelIndex == 0 && _channelData[0].phase == PHASE_SPLIT_240) {
            LOG_WARNING("Channel 0 cannot use split-phase 240V as reference, coercing to phase 1");
            _channelData[0].phase = PHASE_1;
        }

        // Arm transient flags on inactive->active transition. Polarity check runs for
        // every channel (including channel 0); the priority slot is meaningful only
        // for mux-routed channels (channel 0 bypasses the rotation entirely). Already
        // under _channelDataMutex - meter task / scheduler take the same mutex when
        // reading or clearing these flags.
        // armTransients=false suppresses arming for boot-time restore from NVS, where
        // the apparent inactive->active edge is just the default-constructed array
        // being filled in (not a real config change). Without this guard, every boot
        // re-runs the auto-polarity detection and can oscillate the persisted reverse
        // flag on channels that genuinely read negative at idle.
        if (armTransients) {
            bool reverseChanged = (oldReverse != _channelData[channelIndex].reverse);
            bool activated = (wasInactive && _channelData[channelIndex].active);
            bool roleChangedActive = (!wasInactive && _channelData[channelIndex].active && oldRole != _channelData[channelIndex].role);
            bool phaseChangedActive = (!wasInactive && _channelData[channelIndex].active && oldPhase != _channelData[channelIndex].phase);

            if (reverseChanged) {
                // A manual reverse change is the trusted value: disarm CT-reversal
                // detection so it can never override the user's explicit choice, and
                // (issue #149) read once now so the corrected sign lands immediately
                // instead of up to 15 s away on a heavily loaded scheduler.
                _channelData[channelIndex]._pendingPolarityCheck = false;
                _polarityVoteCount[channelIndex] = 0;
                _polarityConductingReads[channelIndex] = 0;
                if (channelIndex > 0) _channelData[channelIndex]._pendingPriorityRead = true;
            } else if (activated || roleChangedActive || phaseChangedActive) {
                // Fresh activation / role / phase change with no explicit polarity
                // choice: arm auto-detection from a clean vote count. The sign
                // convention can legitimately differ between roles, so a role change
                // re-validates. A phase change invalidates the detector's premise
                // outright (the sign of active power is only meaningful if the phase
                // is right), and re-arming also self-heals the stale case where a
                // wrong phase made a correctly-wired CT read steady-negative and the
                // detector flipped reverse: once the user fixes the phase, the next
                // votes flip it back within seconds (issue #174).
                _channelData[channelIndex]._pendingPolarityCheck = true;
                _polarityVoteCount[channelIndex] = 0;
                _polarityConductingReads[channelIndex] = 0;
                if (channelIndex > 0) _channelData[channelIndex]._pendingPriorityRead = true;
            }
        }

        _recalculateWeights();

        releaseMutex(&_channelDataMutex);

        _updateChannelData(channelIndex);
        _saveChannelDataToPreferences(channelIndex);
        if (!globalCommunityMode) Mqtt::requestChannelPublish();

        // Detect role change
        bool detected = (oldRole != channelData.role);
        if (detected) {
            LOG_DEBUG("Channel %u role changed: %s -> %s",
                     channelIndex, channelRoleToString(oldRole), channelRoleToString(channelData.role));
        }
        if (roleChanged) *roleChanged = detected;

        LOG_DEBUG("Successfully set channel data for channel %lu", channelIndex);
        return true;
    }

    bool resetChannelData(uint8_t channelIndex) {
        if (!isChannelValid(channelIndex)) {
            LOG_WARNING("Channel index out of bounds: %lu", channelIndex);
            return false;
        }

        // This is a config-only reset; it must not touch the energy-reset boundary
        // (only resetEnergyValues / resetChannelEnergyValues own that). Read the current
        // value first rather than defaulting to 0 on failure, which would silently wipe it.
        ChannelData current(channelIndex);
        if (!getChannelData(current, channelIndex)) {
            LOG_ERROR("Failed to read current data for channel %u before reset; aborting to avoid wiping startMeasuringUnixTimeMs", channelIndex);
            return false;
        }

        ChannelData channelData(channelIndex); // Constructor with index sets proper defaults
        channelData.startMeasuringUnixTimeMs = current.startMeasuringUnixTimeMs;
        if (!setChannelData(channelData, channelIndex)) {
            LOG_ERROR("Failed to reset channel data for channel %lu", channelIndex);
            return false;
        }

        LOG_DEBUG("Successfully reset channel data for channel %lu", channelIndex);
        return true;
    }

    // Channel data management - JSON operations
    // =========================================

    bool getChannelDataAsJson(JsonDocument &jsonDocument, uint8_t channelIndex) {
        if (!isChannelValid(channelIndex)) {
            LOG_WARNING("Channel index out of bounds: %lu", channelIndex);
            return false;
        }

        ChannelData channelData(channelIndex);
        if (!getChannelData(channelData, channelIndex)) {
            LOG_WARNING("Failed to get channel data as JSON for channel %lu", channelIndex);
            return false;
        }
        channelDataToJson(channelData, jsonDocument);
        return true;
    }

    bool getAllChannelDataAsJson(JsonDocument &jsonDocument) {
        for (uint8_t channelIndex = 0; channelIndex < globalHwProfile->totalChannelCount; channelIndex++) {
            SpiRamAllocator allocator;
            JsonDocument channelDoc(&allocator);
            if (!getChannelDataAsJson(channelDoc, channelIndex)) {
                LOG_WARNING("Failed to get channel data as JSON for channel %lu", channelIndex);
                continue;
            }
            jsonDocument[channelIndex] = channelDoc;
        }

        if (!jsonDocument.isNull() && jsonDocument.size() > 0) return true;
        else return false;
    }

    uint32_t computeAllChannelDataHash() {
        ChannelData allChannelData[MAX_CHANNEL_COUNT];

        // Zero-initialize to ensure padding bytes and unused char array bytes are consistent
        memset(allChannelData, 0, sizeof(allChannelData));

        // Collect all channel data
        for (uint8_t i = 0; i < globalHwProfile->totalChannelCount; i++) {
            if (!getChannelData(allChannelData[i], i)) {
                LOG_WARNING("Failed to get channel data for hash computation (channel %u)", i);
                return 0; // Return 0 on error to force fresh data
            }
        }

        // Compute CRC32 hash using ESP32 hardware CRC
        return crc32_le(0, (const uint8_t*)allChannelData, sizeof(allChannelData));
    }

    bool setChannelDataFromJson(const JsonDocument &jsonDocument, bool partial, bool* roleChanged) {
        if (!_validateChannelDataJson(jsonDocument, partial)) {
            LOG_WARNING("Invalid channel data JSON. Skipping setting data");
            return false;
        }

        uint8_t channelIndex = jsonDocument["index"].as<uint8_t>();

        if (!isChannelValid(channelIndex)) {
            LOG_WARNING("Invalid channel index: %u. Skipping setting data", channelIndex);
            return false;
        }

        ChannelData channelData(channelIndex);
        if (!getChannelData(channelData, channelIndex)) {
            LOG_WARNING("Failed to get channel data from JSON for channel %u", channelIndex);
            return false;
        }

        channelDataFromJson(jsonDocument, channelData, partial);

        if (!setChannelData(channelData, channelIndex, roleChanged)) {
            LOG_WARNING("Failed to set channel data from JSON for channel %u", channelIndex);
            return false;
        }

        return true;
    }

    void channelDataToJson(const ChannelData &channelData, JsonDocument &jsonDocument) {
        jsonDocument["index"] = channelData.index;
        jsonDocument["active"] = channelData.active;
        jsonDocument["reverse"] = channelData.reverse;
        jsonDocument["label"] = JsonString(channelData.label); // Ensure it is not a dangling pointer
        jsonDocument["phase"] = channelData.phase;

        jsonDocument["ctSpecification"]["currentRating"] = channelData.ctSpecification.currentRating;
        jsonDocument["ctSpecification"]["voltageOutput"] = channelData.ctSpecification.voltageOutput;
        jsonDocument["ctSpecification"]["scalingFraction"] = channelData.ctSpecification.scalingFraction;

        // Channel grouping
        jsonDocument["groupLabel"] = JsonString(channelData.groupLabel);

        // Channel role
        jsonDocument["role"] = channelRoleToString(channelData.role);

        // Device-reported reset boundary. Always reported, including the 0/"unset" value.
        jsonDocument["startMeasuringUnixTimeMs"] = channelData.startMeasuringUnixTimeMs;

        LOG_VERBOSE("Successfully converted channel data to JSON for channel %u", channelData.index);
    }

    void channelDataFromJson(const JsonDocument &jsonDocument, ChannelData &channelData, bool partial) {
        // Transient flags are runtime-only and never carried in/out via JSON.
        channelData._pendingPriorityRead = false;
        channelData._pendingPolarityCheck = false;

        if (partial) {
            // Update only fields that are present in JSON
            if (jsonDocument["index"].is<uint8_t>()) channelData.index = jsonDocument["index"].as<uint8_t>();
            if (jsonDocument["active"].is<bool>()) channelData.active = jsonDocument["active"].as<bool>();
            if (jsonDocument["reverse"].is<bool>()) channelData.reverse = jsonDocument["reverse"].as<bool>();
            if (jsonDocument["label"].is<const char*>()) {
                snprintf(channelData.label, sizeof(channelData.label), "%s", jsonDocument["label"].as<const char*>());
            }
            if (jsonDocument["phase"].is<uint8_t>()) channelData.phase = static_cast<Phase>(jsonDocument["phase"].as<uint8_t>());
            
            // CT Specification fields
            if (jsonDocument["ctSpecification"]["currentRating"].is<float>()) {
                channelData.ctSpecification.currentRating = jsonDocument["ctSpecification"]["currentRating"].as<float>();
            }
            if (jsonDocument["ctSpecification"]["voltageOutput"].is<float>()) {
                channelData.ctSpecification.voltageOutput = jsonDocument["ctSpecification"]["voltageOutput"].as<float>();
            }
            if (jsonDocument["ctSpecification"]["scalingFraction"].is<float>()) {
                channelData.ctSpecification.scalingFraction = jsonDocument["ctSpecification"]["scalingFraction"].as<float>();
            }

            // Channel grouping
            if (jsonDocument["groupLabel"].is<const char*>()) {
                snprintf(channelData.groupLabel, sizeof(channelData.groupLabel), "%s", jsonDocument["groupLabel"].as<const char*>());
            }

            // Channel role
            if (jsonDocument["role"].is<const char*>()) {
                channelData.role = channelRoleFromString(jsonDocument["role"].as<const char*>());
            }
        } else {
            // Full update - set all fields
            channelData.index = jsonDocument["index"].as<uint8_t>();
            channelData.active = jsonDocument["active"].as<bool>();
            channelData.reverse = jsonDocument["reverse"].as<bool>();
            snprintf(channelData.label, sizeof(channelData.label), "%s", jsonDocument["label"].as<const char*>());
            channelData.phase = static_cast<Phase>(jsonDocument["phase"].as<uint8_t>());

            channelData.ctSpecification.currentRating = jsonDocument["ctSpecification"]["currentRating"].as<float>();
            channelData.ctSpecification.voltageOutput = jsonDocument["ctSpecification"]["voltageOutput"].as<float>();
            channelData.ctSpecification.scalingFraction = jsonDocument["ctSpecification"]["scalingFraction"].as<float>();

            // Channel grouping
            snprintf(channelData.groupLabel, sizeof(channelData.groupLabel), "%s", jsonDocument["groupLabel"].as<const char*>());

            // Channel role
            channelData.role = channelRoleFromString(jsonDocument["role"].as<const char*>());
        }

        // Device-reported reset boundary. Applies to both the partial and full paths above:
        // channelData is always preloaded with the current value before this function runs (see
        // setChannelDataFromJson), so absent or implausible (e.g. seconds/microseconds sent
        // instead of ms) simply leaves it unchanged rather than fabricating a false reset.
        bool startMeasuringPresent = jsonDocument["startMeasuringUnixTimeMs"].is<uint64_t>();
        uint64_t startMeasuringCandidate = jsonDocument["startMeasuringUnixTimeMs"].as<uint64_t>();
        if (ShadowLogic::shouldAdoptStartMeasuringUnixTimeMs(startMeasuringPresent, startMeasuringCandidate)) {
            channelData.startMeasuringUnixTimeMs = startMeasuringCandidate;
        } else if (startMeasuringPresent) {
            LOG_WARNING("Rejected implausible startMeasuringUnixTimeMs %llu for channel %u",
                        startMeasuringCandidate, channelData.index);
        } else if (!jsonDocument["startMeasuringUnixTimeMs"].isNull()) {
            LOG_WARNING("Ignored startMeasuringUnixTimeMs for channel %u: wrong type (expected integer)", channelData.index);
        }
    }

    ChannelRole getChannelRole(uint8_t channelIndex) {
        if (!isChannelValid(channelIndex)) {
            LOG_WARNING("Channel index out of bounds: %lu", channelIndex);
            return CHANNEL_ROLE_LOAD; // Default role
        }

        if (!acquireMutex(&_channelDataMutex)) {
            LOG_ERROR("Failed to acquire mutex for channel data");
            return CHANNEL_ROLE_LOAD; // Default role
        }

        ChannelRole role = _channelData[channelIndex].role;
        releaseMutex(&_channelDataMutex);
        return role;
    }

    const char* channelRoleToString(ChannelRole role) {
        switch (role) {
            case CHANNEL_ROLE_GRID:     return "grid";
            case CHANNEL_ROLE_PV:       return "pv";
            case CHANNEL_ROLE_BATTERY:  return "battery";
            case CHANNEL_ROLE_INVERTER: return "inverter";
            case CHANNEL_ROLE_BIDIRECTIONAL: return "bidirectional";
            case CHANNEL_ROLE_LOAD:
            default:                    return "load";
        }
    }

    ChannelRole channelRoleFromString(const char* roleStr) {
        if (strcmp(roleStr, "grid") == 0)     return CHANNEL_ROLE_GRID;
        if (strcmp(roleStr, "pv") == 0)       return CHANNEL_ROLE_PV;
        if (strcmp(roleStr, "battery") == 0)  return CHANNEL_ROLE_BATTERY;
        if (strcmp(roleStr, "inverter") == 0) return CHANNEL_ROLE_INVERTER;
        if (strcmp(roleStr, "bidirectional") == 0) return CHANNEL_ROLE_BIDIRECTIONAL;
        return CHANNEL_ROLE_LOAD; // Default
    }

    bool isValidChannelRoleString(const char* roleStr) {
        return (strcmp(roleStr, "load") == 0 ||
                strcmp(roleStr, "grid") == 0 ||
                strcmp(roleStr, "pv") == 0 ||
                strcmp(roleStr, "battery") == 0 ||
                strcmp(roleStr, "inverter") == 0 ||
                strcmp(roleStr, "bidirectional") == 0);
    }

    // Energy data management
    // ======================

    // Clears startMeasuringUnixTimeMs back to 0 (unset) for a reset channel. No
    // isTimeSynched() check here, deliberately: the _energySaveTask drain loop is the single
    // place that ever resolves 0 to a real timestamp, once the clock is synced.
    void _clearStartMeasuring(uint8_t channelIndex) {
        if (!isChannelValid(channelIndex)) return;

        if (acquireMutex(&_channelDataMutex)) {
            _channelData[channelIndex].startMeasuringUnixTimeMs = 0;
            releaseMutex(&_channelDataMutex);
            _saveChannelDataToPreferences(channelIndex);
        } else {
            LOG_ERROR("Failed to acquire mutex to clear channel %u start-measuring timestamp", channelIndex);
        }
    }

    void resetEnergyValues() {
        if (!acquireMutex(&_meterValuesMutex)) {
            LOG_ERROR("Failed to acquire mutex for meter values");
            return;
        }

        // Set all energy values to 0 (safe since we acquired the mutex). Rebase the
        // baselined channels too, so a discard streak spanning the reset does not book
        // its pre-reset time into the new counters.
        uint64_t nowMillis = millis64();
        for (uint8_t i = 0; i < globalHwProfile->totalChannelCount; i++) {
            _meterValues[i].activeEnergyImported = 0.0;
            _meterValues[i].activeEnergyExported = 0.0;
            _meterValues[i].reactiveEnergyImported = 0.0;
            _meterValues[i].reactiveEnergyExported = 0.0;
            _meterValues[i].apparentEnergy = 0.0;
            if (_meterValues[i].lastMillis != 0) _meterValues[i].lastMillis = nowMillis;
        }

        releaseMutex(&_meterValuesMutex);

        // Clear energy preferences
        Preferences preferences;
        preferences.begin(PREFERENCES_NAMESPACE_ENERGY, false);
        preferences.clear();
        preferences.end();

        for (uint8_t i = 0; i < globalHwProfile->totalChannelCount; i++) {
            _saveEnergyToPreferences(i);
            _clearStartMeasuring(i);
        }

        // Offload heavy file I/O to background task
        _spawnHistoryClearTask(CLEAR_ALL_CHANNELS_SENTINEL);

        LOG_DEBUG("Started task for clearing history of all channels");
    }

    void resetChannelEnergyValues(uint8_t channelIndex) {
        if (!isChannelValid(channelIndex)) {
            LOG_ERROR("Invalid channel index: %u", channelIndex);
            return;
        }

        if (!acquireMutex(&_meterValuesMutex)) {
            LOG_ERROR("Failed to acquire mutex for meter values");
            return;
        }

        _meterValues[channelIndex].activeEnergyImported = 0.0;
        _meterValues[channelIndex].activeEnergyExported = 0.0;
        _meterValues[channelIndex].reactiveEnergyImported = 0.0;
        _meterValues[channelIndex].reactiveEnergyExported = 0.0;
        _meterValues[channelIndex].apparentEnergy = 0.0;
        if (_meterValues[channelIndex].lastMillis != 0) _meterValues[channelIndex].lastMillis = millis64(); // See resetEnergyValues

        releaseMutex(&_meterValuesMutex);

        _saveEnergyToPreferences(channelIndex, true); // Force save zeroed values
        _clearStartMeasuring(channelIndex);

        // Offload heavy file I/O to background task
        _spawnHistoryClearTask(channelIndex);

        LOG_DEBUG("Started task for clearing history for channel %u", channelIndex);
    }

    bool _clearChannelHistoricalData(uint8_t channelIndex) {
        if (!isChannelValid(channelIndex)) {
            LOG_ERROR("Invalid channel index: %u", channelIndex);
            return false;
        }

        LOG_INFO("Clearing historical data for channel %u...", channelIndex);

        // Process all three energy directories (daily, monthly, yearly)
        const char* energyDirs[] = { ENERGY_CSV_DAILY_PREFIX, ENERGY_CSV_MONTHLY_PREFIX, ENERGY_CSV_YEARLY_PREFIX };
        uint32_t filesProcessed = 0;
        uint32_t filesModified = 0;

        for (const char* dirPath : energyDirs) {
            if (!LittleFS.exists(dirPath)) continue;

            File dir = LittleFS.open(dirPath);
            if (!dir) continue;

            // Collect filenames first (to avoid modifying while iterating)
            // Skip temporary working files (TEMPORARY_FILE_PREFIX*) that may be left over from previous crashes
            std::vector<char*> filenames;
            File file = dir.openNextFile();
            uint32_t loops = 0;
            while (file && loops < MAX_LOOP_ITERATIONS) {
                loops++;
                const char* filename = file.name();
                // Skip temporary working files (TEMPORARY_FILE_PREFIX_decompressed.csv, TEMPORARY_FILE_PREFIX_filter.csv, etc.)
                if (!file.isDirectory() && (endsWith(filename, ".csv") || endsWith(filename, ".csv.gz"))
                    && strncmp(filename, TEMPORARY_FILE_PREFIX, strlen(TEMPORARY_FILE_PREFIX)) != 0) {
                    char* nameCopy = (char*)ps_malloc(strlen(filename) + 1);
                    if (nameCopy) {
                        strcpy(nameCopy, filename);
                        filenames.push_back(nameCopy);
                    }
                }
                file.close();
                file = dir.openNextFile();
            }
            dir.close();

            // Process each file
            for (const char* filename : filenames) {
                char filepath[NAME_BUFFER_SIZE];
                snprintf(filepath, sizeof(filepath), "%s/%s", dirPath, filename);
                filesProcessed++;

                bool isGzip = endsWith(filename, ".csv.gz");
                char csvPath[NAME_BUFFER_SIZE];
                char tempPath[NAME_BUFFER_SIZE];
                snprintf(tempPath, sizeof(tempPath), "%s/%s_filter.csv", dirPath, TEMPORARY_FILE_PREFIX);

                // If gzip, decompress first
                if (isGzip) {
                    snprintf(csvPath, sizeof(csvPath), "%s/%s_decompressed.csv", dirPath, TEMPORARY_FILE_PREFIX);

                    LOG_DEBUG("Decompressing %s...", filepath);
                    // Use GzUnpacker to decompress
                    GzUnpacker *unpacker = new GzUnpacker();
                    if (!unpacker) {
                        LOG_ERROR("Failed to allocate GzUnpacker for %s", filepath);
                        continue;
                    }
                    unpacker->haltOnError(false);
                    bool decompressSuccess = unpacker->gzExpander(LittleFS, filepath, LittleFS, csvPath);
                    delete unpacker;

                    if (!decompressSuccess) {
                        LOG_ERROR("Failed to decompress %s", filepath);
                        LittleFS.remove(csvPath);
                        continue;
                    }
                } else {
                    snprintf(csvPath, sizeof(csvPath), "%s", filepath);
                }

                LOG_DEBUG("Filtering channel %u from %s...", channelIndex, filepath);
                // Filter the CSV file - remove lines for the specified channel
                File srcFile = LittleFS.open(csvPath, FILE_READ);
                if (!srcFile) {
                    LOG_ERROR("Failed to open source file: %s", csvPath);
                    if (isGzip) LittleFS.remove(csvPath);
                    continue;
                }

                File destFile = LittleFS.open(tempPath, FILE_WRITE);
                if (!destFile) {
                    LOG_ERROR("Failed to create temp file: %s", tempPath);
                    srcFile.close();
                    if (isGzip) LittleFS.remove(csvPath);
                    continue;
                }

                // Read line by line and filter
                char lineBuffer[256];
                bool isFirstLine = true;
                bool hasDataRemaining = false;
                char channelStr[8];
                snprintf(channelStr, sizeof(channelStr), ",%u,", channelIndex);

                uint32_t loops = 0;
                while (srcFile.available() && loops < MAX_LOOP_ITERATIONS) {
                    loops++;
                    size_t len = 0;
                    char c;
                    while (srcFile.available() && len < sizeof(lineBuffer) - 1) {
                        c = static_cast<char>(srcFile.read());
                        if (c == '\n') break;
                        lineBuffer[len++] = c;
                    }
                    lineBuffer[len] = '\0';

                    // Skip empty lines
                    if (len == 0) continue;

                    // Always keep the header
                    if (isFirstLine) {
                        destFile.println(lineBuffer);
                        isFirstLine = false;
                        continue;
                    }

                    // Check if this line belongs to the channel we want to remove
                    // CSV format: timestamp,channel,active_imported,active_exported
                    // We check for ",X," pattern where X is the channel number
                    if (strstr(lineBuffer, channelStr) == nullptr) {
                        destFile.println(lineBuffer);
                        hasDataRemaining = true;
                    }
                }

                srcFile.close();
                destFile.close();

                // Clean up decompressed temp file if we used gzip
                if (isGzip) {
                    LittleFS.remove(csvPath);
                }

                // Replace original file with filtered version
                if (hasDataRemaining) {
                    // Remove original and rename temp
                    LittleFS.remove(filepath);
                    
                    if (isGzip) {
                        // Recompress the filtered file
                        char finalCsvPath[NAME_BUFFER_SIZE];
                        // Remove the .gz extension to get the csv path for compression
                        snprintf(finalCsvPath, sizeof(finalCsvPath), "%s", filepath);
                        finalCsvPath[strlen(finalCsvPath) - 3] = '\0'; // Remove ".gz"
                        
                        LittleFS.rename(tempPath, finalCsvPath);

                        LOG_DEBUG("Recompressing %s...", finalCsvPath);
                        if (!compressFile(finalCsvPath)) {
                            LOG_WARNING("Failed to recompress %s, keeping as CSV", finalCsvPath);
                        }
                    } else {
                        LittleFS.rename(tempPath, filepath);
                    }
                    filesModified++;
                } else {
                    // No data remaining, remove the file entirely
                    LittleFS.remove(filepath);
                    LittleFS.remove(tempPath);
                    filesModified++;
                    LOG_DEBUG("Removed empty file after filtering: %s", filepath);
                }
            }

            // Cleanup filename copies
            for (char* name : filenames) free(name);
        }

        LOG_INFO("Cleared historical data for channel %u: %lu files processed, %lu files modified", 
                 channelIndex, filesProcessed, filesModified);
        return true;
    }

    bool setEnergyValues(
        uint8_t channelIndex,
        double activeEnergyImported,
        double activeEnergyExported,
        double reactiveEnergyImported,
        double reactiveEnergyExported,
        double apparentEnergy
    ) {
        if (!isChannelValid(channelIndex)) {
            LOG_ERROR("Invalid channel index %d", channelIndex);
            return false;
        }

        if (activeEnergyImported < 0 || activeEnergyExported < 0 || 
            reactiveEnergyImported < 0 || reactiveEnergyExported < 0 || 
            apparentEnergy < 0) {
            LOG_ERROR("Energy values must be non-negative");
            return false;
        }

        if (!acquireMutex(&_meterValuesMutex)) {
            LOG_ERROR("Failed to acquire mutex for meter values");
            return false;
        }

        _meterValues[channelIndex].activeEnergyImported = activeEnergyImported;
        _meterValues[channelIndex].activeEnergyExported = activeEnergyExported;
        _meterValues[channelIndex].reactiveEnergyImported = reactiveEnergyImported;
        _meterValues[channelIndex].reactiveEnergyExported = reactiveEnergyExported;
        _meterValues[channelIndex].apparentEnergy = apparentEnergy;

        releaseMutex(&_meterValuesMutex);

        _saveEnergyToPreferences(channelIndex);
        
        LOG_INFO("Successfully set energy values for channel %d", channelIndex);
        return true;
    }

    // Data output
    // ===========

    bool singleMeterValuesToJson(JsonDocument &jsonDocument, uint8_t channelIndex) { // Around 250 bytes per channel of meter values
        if (!isChannelValid(channelIndex)) {
            LOG_WARNING("Channel index out of bounds: %u", channelIndex);
            return false;
        }

        MeterValues meterValues;
        if (!getMeterValues(meterValues, channelIndex)) { // We use it here to ensure non-concurrent access
            LOG_WARNING("Failed to get meter values for channel %d", channelIndex);
            return false;
        }

        // Reduce the decimals since we don't have or need too much precision, and we save on space
        jsonDocument["voltage"] = roundToDecimals(meterValues.voltage, VOLTAGE_DECIMALS);
        jsonDocument["current"] = roundToDecimals(meterValues.current, CURRENT_DECIMALS);
        jsonDocument["activePower"] = roundToDecimals(meterValues.activePower, POWER_DECIMALS);
        jsonDocument["apparentPower"] = roundToDecimals(meterValues.apparentPower, POWER_DECIMALS);
        jsonDocument["reactivePower"] = roundToDecimals(meterValues.reactivePower, POWER_DECIMALS);
        jsonDocument["powerFactor"] = roundToDecimals(meterValues.powerFactor, POWER_FACTOR_DECIMALS);
        jsonDocument["activeEnergyImported"] = roundToDecimals(meterValues.activeEnergyImported, ENERGY_DECIMALS);
        jsonDocument["activeEnergyExported"] = roundToDecimals(meterValues.activeEnergyExported, ENERGY_DECIMALS);
        jsonDocument["reactiveEnergyImported"] = roundToDecimals(meterValues.reactiveEnergyImported, ENERGY_DECIMALS);
        jsonDocument["reactiveEnergyExported"] = roundToDecimals(meterValues.reactiveEnergyExported, ENERGY_DECIMALS);
        jsonDocument["apparentEnergy"] = roundToDecimals(meterValues.apparentEnergy, ENERGY_DECIMALS);

        return true;
    }


    bool fullMeterValuesToJson(JsonDocument &jsonDocument) {
        for (uint8_t i = 0; i < globalHwProfile->totalChannelCount; i++) {
            // Here we also ensure the channel has valid measurements since we have the "duty" to pass all the correct data
            if (isChannelActive(i) && hasChannelValidMeasurements(i)) {
                ChannelData channelData(i);
                if (!getChannelData(channelData, i)) {
                    LOG_WARNING("Failed to get channel data for channel %u", i);
                    continue;
                }

                JsonObject _jsonChannel = jsonDocument.add<JsonObject>();
                _jsonChannel["index"] = i;
                _jsonChannel["label"] = JsonString(channelData.label); // Ensure the string is not a dangling pointer
                _jsonChannel["phase"] = channelData.phase;
                _jsonChannel["groupLabel"] = JsonString(channelData.groupLabel); // Ensure the string is not a dangling pointer
                _jsonChannel["role"] = channelRoleToString(channelData.role);

                SpiRamAllocator allocator;
                JsonDocument jsonData(&allocator);
                if (!singleMeterValuesToJson(jsonData, i)) {
                    LOG_WARNING("Failed to convert single meter values to JSON for channel %d", i);
                    continue;
                }
                _jsonChannel["data"] = jsonData.as<JsonObject>();
            }
        }

        if (!jsonDocument.isNull() && jsonDocument.size() > 0) return true;
        else return false;
    }

    bool getMeterValues(MeterValues &meterValues, uint8_t channelIndex) {
        if (!isChannelValid(channelIndex)) {
            LOG_WARNING("Channel index out of bounds: %lu", channelIndex);
            return false;
        }

        if (!acquireMutex(&_meterValuesMutex)) {
            LOG_ERROR("Failed to acquire meter values mutex");
            return false;
        }
        meterValues = _meterValues[channelIndex];
        releaseMutex(&_meterValuesMutex);
        return true;
    }

    // Aggregated power calculations 
    // =============================

    float getAggregatedActivePowerByRole(ChannelRole role) {
        float sum = 0.0f;

        if (!acquireMutex(&_meterValuesMutex)) {
            LOG_ERROR("Failed to acquire mutex");
        } else {
            for (uint8_t i = 0; i < globalHwProfile->totalChannelCount; i++) {
                if (isChannelActive(i) && getChannelRole(i) == role) {
                    sum += _meterValues[i].activePower;
                }
            }
            releaseMutex(&_meterValuesMutex);
        }

        return sum;
    }

    float getAggregatedReactivePowerByRole(ChannelRole role) {
        float sum = 0.0f;

        if (!acquireMutex(&_meterValuesMutex)) {
            LOG_ERROR("Failed to acquire mutex");
        } else {
            for (uint8_t i = 0; i < globalHwProfile->totalChannelCount; i++) {
                if (isChannelActive(i) && getChannelRole(i) == role) {
                    sum += _meterValues[i].reactivePower;
                }
            }
            releaseMutex(&_meterValuesMutex);
        }

        return sum;
    }

    float getAggregatedApparentPowerByRole(ChannelRole role) {
        float sum = 0.0f;

        if (!acquireMutex(&_meterValuesMutex)) {
            LOG_ERROR("Failed to acquire mutex");
        } else {
            for (uint8_t i = 0; i < globalHwProfile->totalChannelCount; i++) {
                if (isChannelActive(i) && getChannelRole(i) == role) {
                    sum += _meterValues[i].apparentPower;
                }
            }
            releaseMutex(&_meterValuesMutex);
        }

        return sum;
    }

    float getAggregatedPowerFactorByRole(ChannelRole role) {
        float sumActivePower = 0.0f;
        float sumApparentPower = 0.0f;

        if (!acquireMutex(&_meterValuesMutex)) {
            LOG_ERROR("Failed to acquire mutex");
        } else {
            for (uint8_t i = 0; i < globalHwProfile->totalChannelCount; i++) {
                if (isChannelActive(i) && getChannelRole(i) == role) {
                    sumActivePower += _meterValues[i].activePower;
                    sumApparentPower += _meterValues[i].apparentPower;
                }
            }
            releaseMutex(&_meterValuesMutex);
        }

        if (sumApparentPower == 0.0f) return 0.0f;
        else return sumActivePower / sumApparentPower;
    }

    // Aggregated energy calculations
    // ===============================

    float getAggregatedActiveEnergyImportedByRole(ChannelRole role) {
        double sum = 0.0;

        if (!acquireMutex(&_meterValuesMutex)) {
            LOG_ERROR("Failed to acquire mutex");
        } else {
            for (uint8_t i = 0; i < globalHwProfile->totalChannelCount; i++) {
                if (isChannelActive(i) && getChannelRole(i) == role) {
                    sum += _meterValues[i].activeEnergyImported;
                }
            }
            releaseMutex(&_meterValuesMutex);
        }

        return static_cast<float>(sum);
    }

    float getAggregatedActiveEnergyExportedByRole(ChannelRole role) {
        double sum = 0.0;

        if (!acquireMutex(&_meterValuesMutex)) {
            LOG_ERROR("Failed to acquire mutex");
        } else {
            for (uint8_t i = 0; i < globalHwProfile->totalChannelCount; i++) {
                if (isChannelActive(i) && getChannelRole(i) == role) {
                    sum += _meterValues[i].activeEnergyExported;
                }
            }
            releaseMutex(&_meterValuesMutex);
        }

        return static_cast<float>(sum);
    }

    float getAggregatedReactiveEnergyImportedByRole(ChannelRole role) {
        double sum = 0.0;

        if (!acquireMutex(&_meterValuesMutex)) {
            LOG_ERROR("Failed to acquire mutex");
        } else {
            for (uint8_t i = 0; i < globalHwProfile->totalChannelCount; i++) {
                if (isChannelActive(i) && getChannelRole(i) == role) {
                    sum += _meterValues[i].reactiveEnergyImported;
                }
            }
            releaseMutex(&_meterValuesMutex);
        }

        return static_cast<float>(sum);
    }

    float getAggregatedReactiveEnergyExportedByRole(ChannelRole role) {
        double sum = 0.0;

        if (!acquireMutex(&_meterValuesMutex)) {
            LOG_ERROR("Failed to acquire mutex");
        } else {
            for (uint8_t i = 0; i < globalHwProfile->totalChannelCount; i++) {
                if (isChannelActive(i) && getChannelRole(i) == role) {
                    sum += _meterValues[i].reactiveEnergyExported;
                }
            }
            releaseMutex(&_meterValuesMutex);
        }

        return static_cast<float>(sum);
    }

    float getAggregatedApparentEnergyByRole(ChannelRole role) {
        double sum = 0.0;

        if (!acquireMutex(&_meterValuesMutex)) {
            LOG_ERROR("Failed to acquire mutex");
        } else {
            for (uint8_t i = 0; i < globalHwProfile->totalChannelCount; i++) {
                if (isChannelActive(i) && getChannelRole(i) == role) {
                    sum += _meterValues[i].apparentEnergy;
                }
            }
            releaseMutex(&_meterValuesMutex);
        }

        return static_cast<float>(sum);
    }

    // Grid frequency
    // ==============

    float getGridFrequency() {
        // Filtered EMA once seeded; raw fallback until then (and if ZXV never fires)
        if (_gridFreqEma.seeded) return GridFrequency::frequencyHz(_gridFreqEma, _gridFreqCfg);
        return _gridFrequency;
    }

    bool getChannelIssueFacts(uint8_t channelIndex, ChannelIssueFacts &facts) {
        if (!isChannelValid(channelIndex)) return false;

        facts.evidenceReads = _factEvidenceReads[channelIndex];
        facts.clampedEvidenceReads = _factClampedEvidenceReads[channelIndex];
        facts.polarityFlipCount = _factPolarityFlipCount[channelIndex];
        return true;
    }

    // Private function implementations
    // =========================================================
    // =========================================================

    // Hardware initialization and control
    // ===================================

    static void _setHardwarePins(
        uint8_t ssPin,
        uint8_t sckPin,
        uint8_t misoPin,
        uint8_t mosiPin,
        uint8_t resetPin,
        uint8_t interruptPin
    ) {
        _ssPin = ssPin;
        _sckPin = sckPin;
        _misoPin = misoPin;
        _mosiPin = mosiPin;
        _resetPin = resetPin;
        _interruptPin = interruptPin;
        
        pinMode(_ssPin, OUTPUT);
        pinMode(_sckPin, OUTPUT);
        pinMode(_misoPin, INPUT);
        pinMode(_mosiPin, OUTPUT);
        pinMode(_resetPin, OUTPUT);
        pinMode(_interruptPin, INPUT);

        SPI.begin(_sckPin, _misoPin, _mosiPin, _ssPin);
        SPI.setFrequency(ADE7953_SPI_FREQUENCY); //  Max ADE7953 clock is 2MHz
        SPI.setDataMode(SPI_MODE0);
        SPI.setBitOrder(MSBFIRST);
        digitalWrite(_ssPin, HIGH);

        LOG_DEBUG("Successfully set hardware pins");
    }

    void _reset() {
        digitalWrite(_resetPin, LOW);
        delay(ADE7953_RESET_LOW_DURATION);
        digitalWrite(_resetPin, HIGH);
        delay(ADE7953_RESET_LOW_DURATION);

        LOG_DEBUG("Reset ADE7953");
    }

    void _setOptimumSettings()
    {
        writeRegister(UNLOCK_OPTIMUM_REGISTER, BIT_8, UNLOCK_OPTIMUM_REGISTER_VALUE);
        writeRegister(Reserved_16, BIT_16, DEFAULT_OPTIMUM_REGISTER);

        LOG_DEBUG("Optimum settings applied");
    }

    void _setDefaultParameters()
    {
        _setPgaGain(DEFAULT_PGA_REGISTER, Ade7953Channel::A, MeasurementType::VOLTAGE);
        _setPgaGain(DEFAULT_PGA_REGISTER, Ade7953Channel::A, MeasurementType::CURRENT);
        _setPgaGain(DEFAULT_PGA_REGISTER, Ade7953Channel::B, MeasurementType::CURRENT);

        writeRegister(DISNOLOAD_8, BIT_8, DEFAULT_DISNOLOAD_REGISTER);

        // To compute the no load register, we use X_NOLOAD = 65536 - DYNAMIC_RANGE / 1.4 (as per datasheet)
        // The higher the dynamic range, the lower the no load value (thus we are able to pick up smaller currents)
        int32_t xNoLoad = 65536UL - (int32_t)(DEFAULT_NOLOAD_DYNAMIC_RANGE / 1.4);

        writeRegister(AP_NOLOAD_32, BIT_32, xNoLoad);
        writeRegister(VAR_NOLOAD_32, BIT_32, xNoLoad);
        writeRegister(VA_NOLOAD_32, BIT_32, xNoLoad);

        writeRegister(LCYCMODE_8, BIT_8, DEFAULT_LCYCMODE_REGISTER);

        writeRegister(CONFIG_16, BIT_16, DEFAULT_CONFIG_REGISTER);

        LOG_DEBUG("Default parameters set");
    }

    // System management
    // =================

    void _initializeMutexes()
    {
        if (!createMutexIfNeeded(&_spiMutex)) {
            LOG_ERROR("Failed to create SPI mutex");
            return;
        }
        LOG_DEBUG("SPI mutex created successfully");

        if (!createMutexIfNeeded(&_spiOperationMutex)) {
            LOG_ERROR("Failed to create SPI operation mutex");
            deleteMutex(&_spiMutex);
            return;
        }
        LOG_DEBUG("SPI operation mutex created successfully");

        if (!createMutexIfNeeded(&_configMutex)) {
            LOG_ERROR("Failed to create config mutex");
            deleteMutex(&_spiMutex);
            deleteMutex(&_spiOperationMutex);
            return;
        }
        LOG_DEBUG("Config mutex created successfully");

        if (!createMutexIfNeeded(&_meterValuesMutex)) {
            LOG_ERROR("Failed to create meter values mutex");
            deleteMutex(&_spiMutex);
            deleteMutex(&_spiOperationMutex);
            deleteMutex(&_meterValuesMutex);
        }
        LOG_DEBUG("Meter values mutex created successfully");

        if (!createMutexIfNeeded(&_channelDataMutex)) {
            LOG_ERROR("Failed to create channel data mutex");
            deleteMutex(&_spiMutex);
            deleteMutex(&_spiOperationMutex);
            deleteMutex(&_meterValuesMutex);
            deleteMutex(&_channelDataMutex);
            return;
        }
        LOG_DEBUG("Channel data mutex created successfully");

        LOG_DEBUG("All mutexes initialized successfully");
    }

    void _cleanup() {
        LOG_DEBUG("Cleaning up ADE7953 resources...");
        
        // Stop all tasks first
        _stopMeterReadingTask();
        _stopEnergySaveTask();
        _stopHourlyCsvSaveTask();
        _stopGridSamplerTask();

        // Reset failure counters during cleanup
        _failureCount = 0;
        _firstFailureTime = 0;
        _criticalFailureCount = 0;
        _firstCriticalFailureTime = 0;
        
        // Save final energy data if not already saved
        LOG_DEBUG("Saving final energy data during cleanup");
        _saveEnergyComplete();

        // Waveform buffers are kept: a web handler can still be reading a completed capture while
        // the restart sequence runs (only caller), and a reboot follows.

        LOG_DEBUG("Cleaned up tasks and energy saved");
    }

    /**
     * Verifies the communication with the ADE7953 device.
     * This function reads a specific register from the device and checks if it matches the default value.
     * 
     * @return true if the communication with the ADE7953 is successful, false otherwise.
     */
    bool _verifyCommunication() {
        LOG_DEBUG("Verifying communication with Ade7953...");
        
        uint32_t attempt = 0;
        bool success = false;
        uint64_t lastMillisAttempt = 0;

        uint32_t loops = 0;
        while (attempt < ADE7953_MAX_VERIFY_COMMUNICATION_ATTEMPTS && !success && loops < MAX_LOOP_ITERATIONS) {
            loops++;
            if (millis64() - lastMillisAttempt < ADE7953_VERIFY_COMMUNICATION_INTERVAL) {
                continue;
            }

            LOG_DEBUG("Attempt (%lu/%lu) to communicate with ADE7953", attempt+1, ADE7953_MAX_VERIFY_COMMUNICATION_ATTEMPTS);
            
            _reset();
            attempt++;
            lastMillisAttempt = millis64();

            if ((readRegister(AP_NOLOAD_32, BIT_32, false)) == DEFAULT_EXPECTED_AP_NOLOAD_REGISTER) {
                LOG_DEBUG("Communication successful with ADE7953");
                return true;
            }
        }

        LOG_WARNING("Failed to communicate with ADE7953 after %lu attempts", ADE7953_MAX_VERIFY_COMMUNICATION_ATTEMPTS);
        return false;
    }

    // Interrupt handling
    // ==================

    void _setupInterrupts() {
        // Static timeout (see ADE7953_ZXTOUT_VALUE rationale) - no per-boot computation needed.
        writeRegister(ZXTOUT_16, BIT_16, ADE7953_ZXTOUT_VALUE);

        writeRegister(IRQENA_32, BIT_32, DEFAULT_IRQENA_REGISTER);

        // Clear any existing interrupt status
        readRegister(RSTIRQSTATA_32, BIT_32, false);
        readRegister(RSTIRQSTATB_32, BIT_32, false);

        LOG_DEBUG("ADE7953 interrupts enabled: ZXV, ZXTO (ZXTOUT=%u, ~%ums), CYCEND, RESET, CRC", ADE7953_ZXTOUT_VALUE, ADE7953_ZXTOUT_TARGET_MS);
    }

    void _handleInterrupt(uint64_t linecycUnix)
    {
        // The IRQ pin is level-active-low but the ESP32 interrupt is edge-triggered,
        // so multiple bits routinely co-pend in one wake. RSTIRQSTATA clears ALL bits
        // on read: take one snapshot and service every set bit (never else-if,
        // never a second read).
        int32_t statusA = readRegister(RSTIRQSTATA_32, BIT_32, false);
        // No need to read for channel B (only channel A has the relevant information for use)

        // ZXV first: PERIOD is overwritten every cycle, the energy registers are not
        if (statusA & (1 << IRQSTATA_ZXV_BIT)) {
            statistics.ade7953ZxInterrupts++;
            _handleZxvInterrupt();
        }

        // ZXTO next: grid-loss precursor (no zero crossings within the configured
        // timeout), serviced ahead of routine CYCEND/RESET/CRC bookkeeping.
        if (statusA & (1 << IRQSTATA_ZXTO_BIT)) {
            statistics.ade7953ZxtoInterrupts++;
            _handleZxtoInterrupt();
        }

        if (statusA & (1 << IRQSTATA_CYCEND_BIT)) {
            _handleCycendInterrupt(linecycUnix);
        }

        if (statusA & (1 << IRQSTATA_RESET_BIT)) {
            _handleResetInterrupt();
        }

        if (statusA & (1 << IRQSTATA_CRC_BIT)) {
            _handleCrcChangeInterrupt();
        }

        // IRQSTATA reports every event regardless of IRQENA - enable only gates the
        // physical IRQ pin, not the status bit. Restrict the check to enabled bits.
        constexpr int32_t handledIrqMask =
            (1 << IRQSTATA_ZXV_BIT) | (1 << IRQSTATA_ZXTO_BIT) |
            (1 << IRQSTATA_CYCEND_BIT) | (1 << IRQSTATA_RESET_BIT) | (1 << IRQSTATA_CRC_BIT);
        int32_t enabledStatus = statusA & DEFAULT_IRQENA_REGISTER;
        if (MeterLogic::hasUnhandledIrqBits(enabledStatus, handledIrqMask)) {
            statistics.ade7953UnhandledInterrupts++;
            int32_t unhandledBits = enabledStatus & ~handledIrqMask;
            for (uint8_t bit = 0; bit < 32 && unhandledBits != 0; bit++) {
                if (unhandledBits & (1 << bit)) {
                    LOG_WARNING("Unhandled ADE7953 interrupt status: 0x%08lX | %s", statusA, _irqstataBitName(bit));
                    unhandledBits &= ~(1 << bit);
                }
            }
        }
    }

    void _handleZxvInterrupt()
    {
        // One PERIOD read + integer EMA update; out-of-range reads are discarded inside update()
        GridFrequency::update(_gridFreqEma, _gridFreqCfg, _readPeriod());
    }

    void _attachInterruptHandler() {
        // Detach only if already attached (avoid priting error)
        if (_meterReadingTaskHandle != NULL) _detachInterruptHandler();
        attachInterrupt(digitalPinToInterrupt(_interruptPin), _isrHandler, FALLING);
    }

    void _detachInterruptHandler() {
        detachInterrupt(digitalPinToInterrupt(_interruptPin));
    }

    void _isrHandler()
    {
        BaseType_t xHigherPriorityTaskWoken = pdFALSE;
        statistics.ade7953TotalInterrupts++;
        // Nothing else here: with ZXV the IRQ fires every line cycle, so any state
        // touched here would be clobbered mid-linecyc (see _handleInterrupt).

        // Signal the task to handle the interrupt - let the task determine the cause
        if (_ade7953InterruptSemaphore != NULL) {
            xSemaphoreGiveFromISR(_ade7953InterruptSemaphore, &xHigherPriorityTaskWoken);
            if (xHigherPriorityTaskWoken == pdTRUE) portYIELD_FROM_ISR();
        }
    }

    void _handleCycendInterrupt(uint64_t linecycUnix) {
        LOG_VERBOSE("Line cycle end detected on Channel A");
        statistics.ade7953TotalHandledInterrupts++;

        if (_hasToSkipReading) {
            // First window after a mux switch: it spans the channel transition, so it is
            // contaminated. We simply skip it - the next CYCEND overwrites the register with a
            // clean full window on the settled channel (no reset read needed; with RSTREAD off
            // the register is non-destructive and auto-latches per window).
            LOG_VERBOSE("Skipping contaminated post-switch window for Channel B (channel %lu)", _currentChannel);
            _hasToSkipReading = false;
        } else {
            // Next linecyc we skip since we changed channel
            _hasToSkipReading = true;

            // Since the data is frozen anyway, we can first retrieve the waveform, then the channel reading
            if (_captureState == CaptureState::ARMED && _currentChannel == _captureRequestedChannel) {
                LOG_DEBUG("Matched requested channel %u. Starting waveform capture via polling", _currentChannel);
                
                _captureChannel = _currentChannel;
                _captureSampleCount = 0;
                _captureStartUnixMillis = CustomTime::getUnixTimeMilliseconds();
                _captureStartMicros = micros64();
                _captureState = CaptureState::CAPTURING;
                
                // Immediately start polling for waveform samples
                _pollWaveformSamples();
            }
            
            // Process current channel (if active)
            bool readOk = true;
            if (_currentChannel != INVALID_CHANNEL) {
                readOk = _processChannelReading(_currentChannel, linecycUnix);
            }

            // Fix for issue #149: refund the WDRR deficit decremented at selection
            // time when the reading was actually discarded. Without this, a channel
            // stuck in a discard loop drifts ever-more-negative in the deficit array
            // and starves out of the scheduler. Channel 0 is not in the rotation, so
            // skip it. Matches the existing mutex-free access pattern on _channelDeficit[].
            if (!readOk && _currentChannel != INVALID_CHANNEL && _currentChannel > 0) {
                _channelDeficit[_currentChannel] += 1.0f;
            }

            // Thanks to the linecyc approach, the data in the ADE7953 is "frozen"
            // until the next linecyc interrupt is received, which allows us to switch to the
            // next channel after we've completely read what we need to read (and in any case, the
            // next reading will be purged)

            // Skip channel switching during OTA to avoid timing issues from CPU starvation
            if (!Update.isRunning()) {
                _currentChannel = _findNextActiveChannel(_currentChannel);

                // Channel 0 is the direct ADE7953 input (not routed through the mux). So it will never be chosen as actual _currentChannel value
                // For channels 1+, look up the physical mux channel via muxChannelMap
                // (logical index _currentChannel - 1 → physical Y-channel on the 74HC4067).
                if (_currentChannel != INVALID_CHANNEL) Multiplexer::setChannel(globalHwProfile->muxChannelMap[_currentChannel - 1]);
            } else {
                LOG_DEBUG("OTA in progress, skipping channel switching to avoid timing issues");
            }
        }
        
        // Check for channel 0 waveform capture separately (channel 0 doesn't go through multiplexer rotation)
        // Channel 0 is always active and processed on every CYCEND, so we check for armed state here
        if (_captureState == CaptureState::ARMED && _captureRequestedChannel == 0) {
            LOG_DEBUG("Starting waveform capture for channel 0 via polling");
            
            _captureChannel = 0;
            _captureSampleCount = 0;
            _captureStartUnixMillis = CustomTime::getUnixTimeMilliseconds();
            _captureStartMicros = micros64();
            _captureState = CaptureState::CAPTURING;
            
            // Immediately start polling for waveform samples
            _pollWaveformSamples();
        }
        
        // Always process channel 0 as it is on a separate ADE7953 channel
        _processChannelReading(0, linecycUnix);
    }

    void _pollWaveformSamples() { // TODO: this could become something related to a websocket for real time visualization and similar
        // This function performs tight polling of instantaneous waveform registers with zero-crossing detection
        // to ensure capture of complete cycles only. We start on a positive-going voltage zero crossing and
        // stop after detecting the Nth positive-going zero crossing.
        // Called from CYCEND interrupt context - we are sure we are in a "clean" state (no multiplexer switching)
        
        Ade7953Channel ade7953Channel = (_captureChannel == 0) ? Ade7953Channel::A : Ade7953Channel::B;
        
        // State machine for zero-crossing detection
        enum class CapturePhase {
            WAIT_FOR_START_CROSSING,  // Wait for initial positive-going zero crossing
            CAPTURING,                 // Actively capturing samples
        };
        
        CapturePhase phase = CapturePhase::WAIT_FOR_START_CROSSING;
        int32_t previousVoltage = 0;
        uint8_t zeroCrossingCount = 0;
        const uint8_t targetCrossings = WAVEFORM_CYCLES_TO_CAPTURE; // Each positive crossing = 1 cycle start
        
        uint32_t loops = 0;
        uint32_t samplesBeforeStart = 0;
        
        while (loops < MAX_LOOP_ITERATIONS) {
            uint64_t currentMicros = micros64();
            loops++;
            
            // Safety timeout
            if (currentMicros - _captureStartMicros >= WAVEFORM_CAPTURE_MAX_DURATION_MICROS) {
                char captureDurHuman[DURATION_FORMAT_BUFFER_SIZE];
                DurationFormat::humanizeDuration((currentMicros - _captureStartMicros) / 1000, captureDurHuman, sizeof(captureDurHuman));
                LOG_WARNING("Waveform capture timeout after %s, captured %u samples with %u zero crossings",
                    captureDurHuman, _captureSampleCount, zeroCrossingCount);
                break;
            }
            
            // Read instantaneous voltage
            int32_t currentVoltage = _readVoltageInstantaneous();
            
            bool positiveZeroCrossing = (previousVoltage < 0 && currentVoltage >= 0);
            
            if (phase == CapturePhase::WAIT_FOR_START_CROSSING) {
                samplesBeforeStart++;
                
                if (positiveZeroCrossing) {
                    phase = CapturePhase::CAPTURING;
                    zeroCrossingCount = 1; // First crossing detected
                    _captureStartMicros = currentMicros; // Reset start time to actual capture start
                    LOG_VERBOSE("Starting capture at positive zero crossing (after %u samples)", samplesBeforeStart);
                }
                
                previousVoltage = currentVoltage;
                continue; // Don't store samples until we start
            }
            
            // CAPTURING phase - store samples
            if (_captureSampleCount < WAVEFORM_BUFFER_SIZE) {
                _voltageWaveformBuffer[_captureSampleCount] = currentVoltage;
                _currentWaveformBuffer[_captureSampleCount] = _readCurrentInstantaneous(ade7953Channel);
                _microsWaveformBuffer[_captureSampleCount] = currentMicros - _captureStartMicros;
                _captureSampleCount++;
            } else {
                LOG_WARNING("Buffer full before completing cycles, stopping");
                break;
            }
            
            // Check for additional zero crossings during capture
            if (positiveZeroCrossing) {
                zeroCrossingCount++;
                LOG_VERBOSE("Zero crossing %u detected at sample %u", zeroCrossingCount, _captureSampleCount);
                
                // Stop after capturing targetCrossings + 1 crossings
                // (start crossing + N complete cycles = N+1 crossings total)
                if (zeroCrossingCount >= targetCrossings + 1) {
                    LOG_DEBUG("Captured %u complete cycles, stopping", WAVEFORM_CYCLES_TO_CAPTURE);
                    break;
                }
            }
            
            previousVoltage = currentVoltage;
        }
        
        uint64_t totalDurationMs = (micros64() - _captureStartMicros) / 1000;
        
        _captureState = CaptureState::COMPLETE;
        char captureDurHuman[DURATION_FORMAT_BUFFER_SIZE];
        DurationFormat::humanizeDuration(totalDurationMs, captureDurHuman, sizeof(captureDurHuman));
        LOG_INFO("Waveform capture complete for channel %u: %u samples in %s with %u zero crossings",
            _captureChannel, _captureSampleCount, captureDurHuman, zeroCrossingCount);
    }

    void _handleCrcChangeInterrupt() {
        if (_hasConfigurationChanged) { // We were expecting this change, thus no need to log a warning
            _hasConfigurationChanged = false; // Reset the flag
            LOG_DEBUG("Expected configuration change detected");
        } else {
            LOG_WARNING("Unexpected configuration change detected - this may indicate a device issue");
        }
    }

    void _handleResetInterrupt() {
        // This should never happen unless a powerful power drop occurs (which would likely reset also the ESP32)
        LOG_WARNING("TO BE IMPLEMENTED: ADE7953 reset interrupt detected - reinitializing device");
    }

    // Deliberately bypasses IssueRegistry: going through it would add a task hop
    // and mutex-guarded evaluation of unrelated codes, pure latency on a path
    // racing the backup capacitor. Uses the already-cached voltage (no SPI read)
    // for the same reason.
    void _handleZxtoInterrupt() {
        uint64_t nowMs = millis64();
        bool suppressed = (_zxtoLastTriggerMs != 0) && ((nowMs - _zxtoLastTriggerMs) < ADE7953_ZXTO_SUPPRESS_MS);

        if (suppressed) {
            #ifdef ENV_DEV // Bench boards often run with no voltage input connected: keep this out of the DEBUG stream
            LOG_VERBOSE("Blackout still ongoing (suppressed, %llums since last alert, count=%llu)",
                       (unsigned long long)(nowMs - _zxtoLastTriggerMs), statistics.ade7953ZxtoInterrupts);
            #else
            LOG_DEBUG("Blackout still ongoing (suppressed, %llums since last alert, count=%llu)",
                       (unsigned long long)(nowMs - _zxtoLastTriggerMs), statistics.ade7953ZxtoInterrupts);
            #endif
            return;
        }

        _zxtoLastTriggerMs = nowMs;

        if (!globalCommunityMode) {
            AlarmEntry alarm;
            generateHexToken(alarm.eventId, sizeof(alarm.eventId));
            snprintf(alarm.type, sizeof(alarm.type), "zero_crossing_timeout");
            alarm.unixTimeMs = CustomTime::getUnixTimeMilliseconds();
            Mqtt::pushAlarm(alarm);
        }

        LOG_ERROR("Blackout detected: grid power lost (count=%llu, last known voltage=%.1fV)",
                  statistics.ade7953ZxtoInterrupts, _meterValues[0].voltage);
    }

    // Tasks
    // =====

    void _startMeterReadingTask() {
        if (_meterReadingTaskHandle != NULL) {
            LOG_DEBUG("ADE7953 meter reading task is already running");
            return;
        }

        // Create interrupt semaphore if not exists
        if (_ade7953InterruptSemaphore == NULL) {
            _ade7953InterruptSemaphore = xSemaphoreCreateBinary();
            if (_ade7953InterruptSemaphore == NULL) {
                LOG_ERROR("Failed to create ADE7953 interrupt semaphore");
                return;
            }
        }

        // Attach interrupt handler
        _attachInterruptHandler();
        
        LOG_DEBUG("Starting ADE7953 meter reading task with %d bytes stack", ADE7953_METER_READING_TASK_STACK_SIZE);

        BaseType_t result = xTaskCreate(
            _meterReadingTask, 
            ADE7953_METER_READING_TASK_NAME, 
            ADE7953_METER_READING_TASK_STACK_SIZE, 
            nullptr, 
            ADE7953_METER_READING_TASK_PRIORITY, 
            &_meterReadingTaskHandle);
        
        if (result != pdPASS) {
            LOG_ERROR("Failed to create ADE7953 meter reading task");
            _meterReadingTaskHandle = NULL;
        }
    }

    void _stopMeterReadingTask() {
        // Detach interrupt handler
        _detachInterruptHandler();
        
        // Stop task gracefully using utils function
        stopTaskGracefully(&_meterReadingTaskHandle, "ADE7953 meter reading task");
        
        // Clean up semaphore
        if (_ade7953InterruptSemaphore != NULL) {
            vSemaphoreDelete(_ade7953InterruptSemaphore);
            _ade7953InterruptSemaphore = NULL;
        }
    }

    void _meterReadingTask(void *parameter)
    {
        LOG_DEBUG("ADE7953 meter reading task started");
        
        _meterReadingTaskShouldRun = true;
        
        while (_meterReadingTaskShouldRun)
        {
            TASK_HEARTBEAT(_meterReadingHeartbeat);

            // Wait for interrupt signal with timeout
            if (
                _ade7953InterruptSemaphore != NULL &&
                xSemaphoreTake(_ade7953InterruptSemaphore, pdMS_TO_TICKS(ADE7953_INTERRUPT_TIMEOUT_MS + _sampleTime)) == pdTRUE
            ) {
                // One pass here can service several coalesced ISR wakeups (binary
                // semaphore); ade7953TotalInterrupts - ade7953ServicePasses is how many were coalesced away.
                statistics.ade7953ServicePasses++;

                // Grab as quickly as possible the current unix time in milliseconds
                // that refers to the "true" time at which the data is temporarily frozen in the ADE7953
                uint64_t linecycUnix = CustomTime::getUnixTimeMilliseconds();

                // Snapshot the status register once and service every pending cause
                // (ZXV and CYCEND routinely co-pend at line rate - see _handleInterrupt)
                _handleInterrupt(linecycUnix);
            } else {
                LOG_DEBUG("No ADE7953 interrupt received within timeout, checking for stop notification");
                _recordCriticalFailure();

                // Clear any interrupt flag to ensure we don't remain stuck
                readRegister(RSTIRQSTATA_32, BIT_32, false);
            }
            
            // Check for stop notification (non-blocking) - this gives immediate shutdown response
            if (ulTaskNotifyTake(pdTRUE, 0) > 0) {
                _meterReadingTaskShouldRun = false;
                break;
            }
        }

        LOG_DEBUG("ADE7953 meter reading task stopping");
        _meterReadingTaskHandle = NULL;
        vTaskDelete(NULL);
    }

    void _startEnergySaveTask() {
        if (_energySaveTaskHandle != NULL) {
            LOG_DEBUG("ADE7953 energy save task is already running");
            return;
        }

        LOG_DEBUG("Starting ADE7953 energy save task with %d bytes stack", ADE7953_ENERGY_SAVE_TASK_STACK_SIZE);

        BaseType_t result = xTaskCreate(
            _energySaveTask,
            ADE7953_ENERGY_SAVE_TASK_NAME,
            ADE7953_ENERGY_SAVE_TASK_STACK_SIZE,
            nullptr,
            ADE7953_ENERGY_SAVE_TASK_PRIORITY,
            &_energySaveTaskHandle);

        if (result != pdPASS) {
            LOG_ERROR("Failed to create ADE7953 energy save task");
            _energySaveTaskHandle = NULL;
        }
    }

    void _stopEnergySaveTask() {
        stopTaskGracefully(&_energySaveTaskHandle, "ADE7953 energy save task");
    }

    void _energySaveTask(void* parameter) {
        LOG_DEBUG("ADE7953 energy save task started");

        _energySaveTaskShouldRun = true;
        while (_energySaveTaskShouldRun) {
            TASK_HEARTBEAT(_energySaveHeartbeat);

            for (uint8_t i = 0; i < globalHwProfile->totalChannelCount; i++) {
                if (isChannelActive(i)) _saveEnergyToPreferences(i);
            }

            // Drain pending polarity-flip persistence (queued by the meter task, which
            // hands NVS writes off to this task instead of doing them inline). Test-and-clear
            // under _channelDataMutex so a concurrent re-set from the meter task lands on the
            // *next* iteration instead of being lost between the read and the false-write.
            for (uint8_t i = 0; i < globalHwProfile->totalChannelCount; i++) {
                bool drain = false;
                if (acquireMutex(&_channelDataMutex)) {
                    if (_pendingPolaritySave[i]) {
                        _pendingPolaritySave[i] = false;
                        drain = true;
                    }
                    releaseMutex(&_channelDataMutex);
                }
                if (drain) _saveChannelDataToPreferences(i);
            }

            // A raised NTP time floor: its NVS write is shallower than the channel save above
            CustomTime::persistPendingFloor();

            // Resolve unset start-measuring timestamps: the first time the clock is
            // synced while a channel's value is still 0, set it to now. Covers a fresh channel, a
            // reset, and (once, on upgrade) an existing device that never had this field before.
            // Not gated by isChannelActive - unlike the energy-save loop above - so a disabled
            // channel never gets stuck at 0 forever.
            if (CustomTime::isTimeSynched()) {
                uint64_t nowMs = CustomTime::getUnixTimeMilliseconds();
                for (uint8_t i = 0; i < globalHwProfile->totalChannelCount; i++) {
                    bool resolve = false;
                    if (acquireMutex(&_channelDataMutex)) {
                        if (_channelData[i].startMeasuringUnixTimeMs == 0) {
                            _channelData[i].startMeasuringUnixTimeMs = nowMs;
                            resolve = true;
                        }
                        releaseMutex(&_channelDataMutex);
                    }
                    if (resolve) {
                        _saveChannelDataToPreferences(i);
                        LOG_INFO("Channel %u startMeasuringUnixTimeMs resolved from unset to %llu", i, nowMs);
                    }
                }
            }

            if (ulTaskNotifyTake(pdTRUE, pdMS_TO_TICKS(SAVE_ENERGY_INTERVAL)) > 0) {
                _energySaveTaskShouldRun = false;
                break;
            }
        }

        LOG_DEBUG("ADE7953 energy save task stopping");
        _energySaveTaskHandle = NULL;
        vTaskDelete(NULL);
    }

    void _startGridSamplerTask() {
        if (_gridSamplerTaskHandle != NULL) {
            LOG_DEBUG("ADE7953 grid sampler task is already running");
            return;
        }

        LOG_DEBUG("Starting ADE7953 grid sampler task with %d bytes stack", ADE7953_GRID_SAMPLER_TASK_STACK_SIZE);

        BaseType_t result = xTaskCreate(
            _gridSamplerTask,
            ADE7953_GRID_SAMPLER_TASK_NAME,
            ADE7953_GRID_SAMPLER_TASK_STACK_SIZE,
            nullptr,
            ADE7953_GRID_SAMPLER_TASK_PRIORITY,
            &_gridSamplerTaskHandle);

        if (result != pdPASS) {
            LOG_ERROR("Failed to create ADE7953 grid sampler task");
            _gridSamplerTaskHandle = NULL;
        }
    }

    void _stopGridSamplerTask() {
        stopTaskGracefully(&_gridSamplerTaskHandle, "ADE7953 grid sampler task");
    }

    void _gridSamplerTask(void* parameter) {
        LOG_DEBUG("ADE7953 grid sampler task started");

        // Freshness gate: only emit if the EMA advanced since the last point
        uint32_t lastSeenUpdateCount = 0;

        _gridSamplerTaskShouldRun = true;
        while (_gridSamplerTaskShouldRun) {
            TASK_HEARTBEAT(_gridSamplerHeartbeat);

            // Sleep to the next absolute .000/.500 wall-clock boundary, re-derived
            // from the clock each iteration so drift never accumulates and NTP
            // steps self-heal. Points always carry the true read time.
            uint64_t now = CustomTime::getUnixTimeMilliseconds();
            uint32_t delayMs = GRID_SAMPLE_INTERVAL_MS - (uint32_t)(now % GRID_SAMPLE_INTERVAL_MS);
            if (delayMs < GRID_SAMPLE_MIN_DELAY_MS) delayMs += GRID_SAMPLE_INTERVAL_MS;

            // The aligned sleep doubles as the stop-notification wait
            if (ulTaskNotifyTake(pdTRUE, pdMS_TO_TICKS(delayMs)) > 0) {
                _gridSamplerTaskShouldRun = false;
                break;
            }

            // Gates: a failed gate skips the tick, leaving a real timestamp gap
            if (!Mqtt::getSendGridData()) continue;
            if (!CustomTime::isTimeSynched()) continue;
            uint32_t updateCount = _gridFreqEma.updateCount;
            if (updateCount == lastSeenUpdateCount) continue; // EMA frozen (no ZXV since last emit)
            lastSeenUpdateCount = updateCount;

            // Cached channel-0 RMS voltage (at most ~_sampleTime old); aligned float
            // read is atomic, keeping the sampler off the SPI bus
            PayloadGridPoint point(
                CustomTime::getUnixTimeMilliseconds(),
                getGridFrequency(),
                _meterValues[0].voltage
            );
            Mqtt::pushGrid(point);
        }

        LOG_DEBUG("ADE7953 grid sampler task stopping");
        _gridSamplerTaskHandle = NULL;
        vTaskDelete(NULL);
    }

    void _startHourlyCsvSaveTask() {
        if (_hourlyCsvSaveTaskHandle != NULL) {
            LOG_DEBUG("ADE7953 hourly CSV save task is already running");
            return;
        }

        LOG_DEBUG("Starting ADE7953 hourly CSV save task with %d bytes stack", ADE7953_HOURLY_CSV_SAVE_TASK_STACK_SIZE);

        BaseType_t result = xTaskCreate(
            _hourlyCsvSaveTask,
            ADE7953_HOURLY_CSV_SAVE_TASK_NAME,
            ADE7953_HOURLY_CSV_SAVE_TASK_STACK_SIZE,
            nullptr,
            ADE7953_HOURLY_CSV_SAVE_TASK_PRIORITY,
            &_hourlyCsvSaveTaskHandle);

        if (result != pdPASS) {
            LOG_ERROR("Failed to create ADE7953 hourly CSV save task");
            _hourlyCsvSaveTaskHandle = NULL;
        }
    }

    void _stopHourlyCsvSaveTask() {
        stopTaskGracefully(&_hourlyCsvSaveTaskHandle, "ADE7953 hourly CSV save task");
    }

    void _hourlyCsvSaveTask(void* parameter) {
        LOG_DEBUG("ADE7953 hourly CSV save task started");

        // Wait INDEFINITELY for time sync before attempting migration as saving daily data does not 
        // make sense without correct timestamps
        while (!CustomTime::isTimeSynched()) {
            LOG_DEBUG("Waiting for time sync to continue with CSV migration on startup");
            delay(10000);
        }

        // Check again just to be sure..
        if (!CustomTime::isTimeSynched()) {
            LOG_WARNING("Time not synchronized after timeout, skipping CSV migration on startup");
        } else {
            // Step 1: Migrate existing files from /energy/ to /energy/daily/ (one-time migration for existing devices)
            migrateEnergyFilesToDailyFolder();
            
            // Step 2: Compress any uncompressed CSV files in daily folder (excluding today's)
            char dateIso[TIMESTAMP_BUFFER_SIZE];
            CustomTime::getCurrentDateIso(dateIso, sizeof(dateIso));
            char excludeFilepath[NAME_BUFFER_SIZE + sizeof(ENERGY_CSV_DAILY_PREFIX) + 1];
            snprintf(excludeFilepath, sizeof(excludeFilepath), "%s/%s", ENERGY_CSV_DAILY_PREFIX, dateIso);
            
            LOG_DEBUG("Migrating the CSV files, excluding prefix of %s", excludeFilepath);
            migrateCsvToGzip(ENERGY_CSV_DAILY_PREFIX, excludeFilepath);
            
            // Step 3: Get current date info for consolidation
            char currentYearMonth[8]; // YYYY-MM
            snprintf(currentYearMonth, sizeof(currentYearMonth), "%.7s", dateIso); // First 7 chars of YYYY-MM-DD
            char currentYear[5]; // YYYY
            snprintf(currentYear, sizeof(currentYear), "%.4s", dateIso); // First 4 chars
            
            // Step 4: Consolidate daily files from previous months (no exclusion needed - full month)
            // Collect unique months first to avoid redundant consolidation calls
            std::set<std::string> monthsToConsolidate;
            File dailyDir = LittleFS.open(ENERGY_CSV_DAILY_PREFIX);
            if (dailyDir) {
                File file = dailyDir.openNextFile();
                uint32_t loops = 0;
                while (file && loops < MAX_LOOP_ITERATIONS) {
                    loops++;
                    const char* filename = file.name();
                    // Check for files like YYYY-MM-DD.csv.gz from previous months
                    if (endsWith(filename, ".csv.gz") && strlen(filename) >= 10) {
                        char fileMonth[8];
                        snprintf(fileMonth, sizeof(fileMonth), "%.7s", filename);
                        if (strcmp(fileMonth, currentYearMonth) < 0) {
                            monthsToConsolidate.insert(std::string(fileMonth));
                        }
                    }
                    file.close();
                    file = dailyDir.openNextFile();
                }
                dailyDir.close();
            }
            for (const auto& month : monthsToConsolidate) {
                LOG_DEBUG("Consolidating daily files from previous month: %s", month.c_str());
                consolidateDailyFilesToMonthly(month.c_str(), nullptr);
            }
            
            // Step 5: Consolidate daily files from current month (excluding today)
            // This consolidates all past days of the current month into the monthly archive
            LOG_DEBUG("Consolidating current month %s daily files (excluding today %s)", currentYearMonth, dateIso);
            consolidateDailyFilesToMonthly(currentYearMonth, dateIso);
            
            // Step 6: Consolidate monthly files from previous years into yearly archives
            // Collect unique years first to avoid redundant consolidation calls
            std::set<std::string> yearsToConsolidate;
            File monthlyDir = LittleFS.open(ENERGY_CSV_MONTHLY_PREFIX);
            if (monthlyDir) {
                File file = monthlyDir.openNextFile();
                uint32_t loops = 0;
                while (file && loops < MAX_LOOP_ITERATIONS) {
                    loops++;
                    const char* filename = file.name();
                    // Check for files like YYYY-MM.csv.gz from previous years
                    if (endsWith(filename, ".csv.gz") && strlen(filename) >= 7) {
                        char fileYear[5];
                        snprintf(fileYear, sizeof(fileYear), "%.4s", filename);
                        if (strcmp(fileYear, currentYear) < 0) {
                            yearsToConsolidate.insert(std::string(fileYear));
                        }
                    }
                    file.close();
                    file = monthlyDir.openNextFile();
                }
                monthlyDir.close();
            }
            for (const auto& year : yearsToConsolidate) {
                LOG_DEBUG("Consolidating monthly files from previous year: %s", year.c_str());
                consolidateMonthlyFilesToYearly(year.c_str(), nullptr);
            }
            
            // Step 7: Consolidate monthly files from current year (excluding current month)
            // This consolidates all past months of the current year into the yearly archive
            LOG_DEBUG("Consolidating current year %s monthly files (excluding %s)", currentYear, currentYearMonth);
            consolidateMonthlyFilesToYearly(currentYear, currentYearMonth);
        }

        _hourlyCsvSaveTaskShouldRun = true;
        while (_hourlyCsvSaveTaskShouldRun) {
            TASK_HEARTBEAT(_hourlyCsvHeartbeat);

            // Calculate milliseconds until next hour using CustomTime
            uint64_t msUntilNextHour = CustomTime::getMillisecondsUntilNextHour();
            char msUntilNextHourHuman[DURATION_FORMAT_BUFFER_SIZE];
            DurationFormat::humanizeDuration(msUntilNextHour, msUntilNextHourHuman, sizeof(msUntilNextHourHuman));
            LOG_DEBUG("Waiting for %s until next hour to save the hourly energy", msUntilNextHourHuman);

            // Wait for the calculated time or stop notification
            if (ulTaskNotifyTake(pdTRUE, pdMS_TO_TICKS((uint32_t)msUntilNextHour)) > 0) { // Needs to be casted to uint32_t otherwise it will crash
                _hourlyCsvSaveTaskShouldRun = false;
                break;
            }
            
            // Only save if we're still running and within tolerance of hourly save time
            if (_hourlyCsvSaveTaskShouldRun)
            {
                if (CustomTime::isTimeSynched())
                {
                    if (CustomTime::isNowCloseToHour())
                    {
                        LOG_DEBUG("Time is close to the hour, saving hourly energy data");
                        _saveHourlyEnergyToCsv();

                        // If this save corresponds to the first hour of the new day (HH == 00),
                        // compress the previous day's CSV (yesterday) and consolidate into monthly archive.
                        if (CustomTime::isNowHourZero()) {
                            LOG_DEBUG("Timestamp is at hour 00: trigger compression and consolidation of yesterday's CSV");

                            // Create filename for yesterday's CSV file (UTC date)
                            char yesterdayIso[TIMESTAMP_BUFFER_SIZE];
                            CustomTime::getDateIsoOfNearestHour(yesterdayIso, sizeof(yesterdayIso), -1);
                            char filepath[NAME_BUFFER_SIZE + sizeof(ENERGY_CSV_DAILY_PREFIX) + 4];
                            snprintf(filepath, sizeof(filepath), "%s/%s.csv", ENERGY_CSV_DAILY_PREFIX, yesterdayIso);

                            if (compressFile(filepath)) {
                                LOG_DEBUG("Successfully compressed yesterday's CSV: %s", filepath);
                                
                                // Get today's date to exclude from consolidation
                                char todayIso[TIMESTAMP_BUFFER_SIZE];
                                CustomTime::getDateIsoOfNearestHour(todayIso, sizeof(todayIso));
                                
                                // Check if we crossed a month boundary (if today is day 01, yesterday was last day of prev month)
                                if (todayIso[8] == '0' && todayIso[9] == '1') {
                                    // Today is day 01, so yesterday was the last day of the previous month
                                    // Consolidate all daily files from the previous month (no exclusion)
                                    char prevMonth[8];
                                    snprintf(prevMonth, sizeof(prevMonth), "%.7s", yesterdayIso);
                                    LOG_DEBUG("Month boundary crossed, consolidating all daily files for %s", prevMonth);
                                    consolidateDailyFilesToMonthly(prevMonth, nullptr);
                                    
                                    // After monthly consolidation, consolidate into yearly archive (excluding current month)
                                    char currentYear[5];
                                    snprintf(currentYear, sizeof(currentYear), "%.4s", todayIso);
                                    char currentMonth[8];
                                    snprintf(currentMonth, sizeof(currentMonth), "%.7s", todayIso);
                                    
                                    // Check if we also crossed a year boundary (if today is Jan 01)
                                    if (todayIso[5] == '0' && todayIso[6] == '1') {
                                        // Today is January, so consolidate all monthly files from previous year (no exclusion)
                                        char prevYear[5];
                                        snprintf(prevYear, sizeof(prevYear), "%.4s", yesterdayIso);
                                        LOG_DEBUG("Year boundary crossed, consolidating all monthly files for %s", prevYear);
                                        consolidateMonthlyFilesToYearly(prevYear, nullptr);
                                    } else {
                                        // Same year - consolidate the previous month into the yearly archive
                                        LOG_DEBUG("Consolidating monthly files into yearly archive for %s (excluding %s)", currentYear, currentMonth);
                                        consolidateMonthlyFilesToYearly(currentYear, currentMonth);
                                    }
                                } else {
                                    // Same month - consolidate yesterday into current month's archive (excluding today)
                                    char currentMonth[8];
                                    snprintf(currentMonth, sizeof(currentMonth), "%.7s", todayIso);
                                    LOG_DEBUG("Consolidating yesterday's data into monthly archive for %s", currentMonth);
                                    consolidateDailyFilesToMonthly(currentMonth, todayIso);
                                }
                            } else {
                                LOG_ERROR("Failed to compress yesterday's CSV: %s", filepath);
                            }
                        }
                    }
                    else
                    {
                        LOG_DEBUG("Not close to the hour, skipping hourly energy save");
                    }
                }
            }
        }

        LOG_DEBUG("ADE7953 hourly CSV save task stopping");
        _hourlyCsvSaveTaskHandle = NULL;
        vTaskDelete(NULL);
    }

    // History clear task - offloads heavy file I/O from HTTP handlers
    // ==============================================================
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
