jibrilsharafi/EnergyMe-Home/source/src/mqtt.cpp

// SPDX-License-Identifier: GPL-3.0-or-later
// Copyright (C) 2025 Jibril Sharafi

#include "mqtt.h"
#include "issueregistry.h"
#include "crashmonitor.h"
#include "shadow.h"
#include "rollback_logic.h"
#include "shadow_logic.h"

static_assert(SHA256_HEX_BUFFER_SIZE == RollbackLogic::SHA256_HEX_LEN + 1,
              "sha256 hex buffers are sized by constants.h but indexed by rollback_logic's length");
#include "taskprofiler.h"
#include "duration_format.h"
#include "mqtt_grid_schedule.h"
#include "mqtt_energy_publish_gate.h"
#include "crash_archive_policy.h"
#include "backoff_schedule.h"
#include "app_image_descriptor.h"
#include "ota_keys.h"
#include "ota_signature.h"
#include "sha256_hex.h"
#include "mbedtls/base64.h"
#include "mbedtls/sha256.h"
#include "mbedtls/pk.h"
#include "mbedtls/md.h"
#include <algorithm>

namespace Mqtt
{
    static TaskHeartbeat _mqttHeartbeat;

    // Static variables
    // ================
    // ================
    
    // MQTT client objects
    static WiFiClientSecure _net;
    static PubSubClient _clientMqtt(_net);
    static PublishMqtt _publishMqtt;

    // FreeRTOS queues
    static QueueHandle_t _logQueue = nullptr;
    static QueueHandle_t _meterQueue = nullptr;
    static QueueHandle_t _gridQueue = nullptr;
    static QueueHandle_t _alarmQueue = nullptr;

    // Static queue structures and storage for PSRAM
    static StaticQueue_t _logQueueStruct;
    static StaticQueue_t _meterQueueStruct;
    static StaticQueue_t _gridQueueStruct;
    static StaticQueue_t _alarmQueueStruct;
    static uint8_t* _logQueueStorage = nullptr;
    static uint8_t* _meterQueueStorage = nullptr;
    static uint8_t* _gridQueueStorage = nullptr;
    static uint8_t* _alarmQueueStorage = nullptr;

    // Connection attempt tracking
    static uint32_t _mqttConnectionAttempt = 0;
    static uint64_t _nextMqttConnectionAttemptMillis = 0;

    // Set from other tasks on interface failover; consumed by _handleConnectedState.
    static volatile bool _reconnectRequested = false;

    void requestReconnect() {
        _reconnectRequested = true;
    }

    // Connection state fact for the issue registry, updated once per task loop
    // (the registry tick must not call _clientMqtt.connected() cross-task)
    static volatile bool _lastConnectedState = false;

    // Last publish timestamps
    static uint64_t _lastMillisMeterPublished = 0;
    static uint64_t _lastMillisSystemDynamicPublished = 0;
    static uint64_t _lastMillisStatisticsPublished = 0;
    static uint64_t _lastMillisCrashPublished = 0;

    // Next grid publish deadline (unix seconds, wall-clock aligned); 0 = not yet scheduled
    static uint64_t _nextGridPublishUnixSecond = 0;
    // Next energy publish deadline (unix seconds, wall-clock aligned); 0 = not yet scheduled
    static uint64_t _nextEnergyPublishUnixSecond = 0;

    // Configuration
    static bool _cloudServicesEnabled = DEFAULT_CLOUD_SERVICES_ENABLED;
    static bool _sendPowerDataEnabled = DEFAULT_SEND_POWER_DATA_ENABLED;
    static bool _sendGridDataEnabled = DEFAULT_SEND_GRID_DATA_ENABLED;
    static uint32_t _meterPublishThresholdBytes = MQTT_METER_PUBLISH_THRESHOLD_BYTES_DEFAULT;
    static uint32_t _meterPublishMaxIntervalMs = MQTT_METER_PUBLISH_MAX_INTERVAL_MS_DEFAULT;
    static uint8_t _mqttLogLevelInt = DEFAULT_MQTT_LOG_LEVEL_INT;
    static LogLevel _mqttMinLogLevel = LogLevel::INFO;

    // Certificates storage (loaded from factory NVS) - allocated in PSRAM
    static char *_awsIotCoreCert = nullptr;
    static char *_awsIotCorePrivateKey = nullptr;
    static bool _certificatesLoaded = false;
    
    // Topic buffers
    static char _mqttTopicMeter[MQTT_TOPIC_BUFFER_SIZE];
    static char _mqttTopicGrid[MQTT_TOPIC_BUFFER_SIZE];
    static char _mqttTopicEnergy[MQTT_TOPIC_BUFFER_SIZE];
    static char _mqttTopicSystemDynamic[MQTT_TOPIC_BUFFER_SIZE];
    static char _mqttTopicStatistics[MQTT_TOPIC_BUFFER_SIZE];
    static char _mqttTopicCrash[MQTT_TOPIC_BUFFER_SIZE];
    static char _mqttTopicLog[MQTT_TOPIC_BUFFER_SIZE];
    static char _mqttTopicAlarm[MQTT_TOPIC_BUFFER_SIZE];

    // Task variables
    static TaskHandle_t _taskHandle = nullptr;
    static bool _lastLoopToPublishData = false;
    static bool _taskShouldRun = false;

    // AWS IoT Jobs OTA task (global to ensure they work and do not get dereferenced)
    static char *_otaCurrentUrl = nullptr;  // URL_BUFFER_SIZE - allocated in PSRAM
    static char _otaCurrentJobId[NAME_BUFFER_SIZE];
    static TaskHandle_t _otaTaskHandle = nullptr;
    static TaskHandle_t _otaValidationTaskHandle = nullptr;
    static bool _otaRebootPending = false;

    // One download attempt: the counters the HTTP event handler fills in as it
    // goes, and the outcome stamped on once the call returns. Shared rather than
    // passed because the event handler is a C callback with no context of its own.
    struct OtaAttempt {
        esp_err_t error;
        int httpStatus;
        size_t bytesReceived;
        size_t contentLength;
        size_t lastProgressBytes; // log throttling only, not reported
        uint32_t freeHeap;
        uint32_t minFreeHeap;
        uint32_t maxAlloc;
    };
    static OtaAttempt _otaAttempt = {};

    // Decoded DER ECDSA signature for the OTA job currently being downloaded,
    // written by _handleSingleJobExecution AFTER the "is a job already in flight"
    // guards (mirrors _otaCurrentUrl/_otaCurrentJobId - writing shared OTA state
    // before those guards would let a second, concurrent job execution overwrite a
    // buffer _verifyOtaSignature() is still reading on the OTA task). Consumed by
    // _verifyOtaSignature() before the boot partition is switched.
    static uint8_t _otaCurrentSignature[OtaSignature::MAX_DER_SIGNATURE_LEN];
    static size_t _otaCurrentSignatureLen = 0;

    // 4 KB scratch buffer for streaming the downloaded OTA partition through
    // SHA-256 in _verifyOtaSignature(), allocated once from PSRAM in begin() -
    // mirrors _otaCurrentUrl below, rather than eating ~1/3 of the OTA task's
    // stack budget (OTA_TASK_STACK_SIZE) on every verification.
    static uint8_t *_otaHashChunkBuffer = nullptr;

    // Reason published for a "FAILED" OTA status; reset to the generic default at
    // the start of every _performOtaUpdate() call, overwritten at specific
    // failure points (e.g. "signature_invalid") so _otaTask can publish a reason
    // distinct from a plain download failure.
    static char _otaFailureReason[NAME_BUFFER_SIZE] = "";

    // False once an attempt fails AFTER the download completed (signature or
    // activation): those failures are deterministic for the same artifact, so
    // retrying re-downloads ~4 MB to fail identically. The retry schedule in
    // _otaTask breaks on it, same as the 4xx case.
    static bool _otaFailureRetryable = true;

    // Set by _verifyOtaSignature() alongside _otaFailureReason: true only for
    // causes that are a property of the downloaded artifact/signature itself
    // (fails identically on retry) or of the fixed embedded key (never
    // recoverable). Local/transient causes (heap, flash read) leave this false
    // so a one-off glitch does not get treated as deterministic by the caller.
    static bool _otaVerifyFailureDeterministic = false;

    // Thread safety
    static SemaphoreHandle_t _configMutex = nullptr;

    // Private function declarations
    // =============================
    // =============================

    // Queue initialization
    static bool _initializeLogQueue();
    static bool _initializeMeterQueue();
    static bool _initializeGridQueue();
    static bool _initializeAlarmQueue();
    
    // Configuration management
    static void _loadConfigFromPreferences();
    static void _saveConfigToPreferences();
    
    static void _setSendPowerDataEnabled(bool enabled);
    static void _setSendGridDataEnabled(bool enabled);
    static void _setMeterPublishThresholdBytes(uint32_t bytes);
    static void _setMeterPublishMaxIntervalMs(uint32_t intervalMs);
    static void _setMqttLogLevel(const char* logLevel);
    static void _updateMqttMinLogLevel();

    static void _saveCloudServicesEnabledToPreferences(bool enabled);
    static void _saveSendPowerDataEnabledToPreferences(bool enabled);
    static void _saveSendGridDataEnabledToPreferences(bool enabled);
    static void _saveMeterPublishThresholdBytesToPreferences(uint32_t bytes);
    static void _saveMeterPublishMaxIntervalMsToPreferences(uint32_t intervalMs);
    static void _saveMqttLogLevelToPreferences(uint8_t logLevel);
        
    // Task management
    static void _startTask();
    static void _stopTask();
    static void _mqttTask(void *parameter);

    // Topic management
    static void _constructMqttTopicReservedThings(const char* finalTopic, char* topicBuffer, size_t topicBufferSize);
    static void _constructMqttTopicWithRule(const char* ruleName, const char* finalTopic, char* topicBuffer, size_t topicBufferSize);
    static void _constructMqttTopic(const char* finalTopic, char* topicBuffer, size_t topicBufferSize);
    static void _setupTopics();

    // Publish topics
    static void _setTopicMeter();
    static void _setTopicGrid();
    static void _setTopicEnergy();
    static void _setTopicSystemDynamic();
    static void _setTopicStatistics();
    static void _setTopicCrash();
    static void _setTopicLog();
    static void _setTopicAlarm();

    // Subscription management
    static void _subscribeToTopics();
    static void _subscribeAwsIotJobs();
    static void _subscribeIotCommands();

    // Subscription callback handler
    static void _subscribeCallback(const char* topic, byte *payload, uint32_t length);
    static void _handleCommandExecution(const char* topic, const char* message);
    static void _publishCommandStatus(const char* executionId, const char* status, const char* reasonCode, const char* reasonDescription);
    static void _queueCommand(const char* topic, const char* payload);
    static void _drainPendingCommand();
    static void _handleAwsIotJobMessage(const char* message, const char* topic);
    
    // AWS IoT Jobs OTA functions
    static bool _validateAwsIotJobMessage(const char* message, const char* topic);
    static void _handleJobListResponse(JsonDocument &doc);
    static void _handleSingleJobExecution(JsonDocument &doc);
    static void _publishOtaJobDetail(const char* jobId);
    static void _otaTask(void* parameter);
    static void _probeOtaHost();
    static esp_err_t _otaHttpEventHandler(esp_http_client_event_t *event);
    static bool _performOtaUpdate();
    static bool _verifyOtaSignature(esp_https_ota_handle_t otaHandle);
    
    // OTA validation functions (clearOtaPendingState is public, declared in mqtt.h)
    static void _otaValidationTask(void* parameter);
    static void _checkPendingOtaValidation();
    static void _publishOtaStatus(const char* jobId, const char* status, const char* reason,
                                  bool withDiagnostics = false, uint8_t attemptsMade = 0);

    // Publishing functions
    static void _publishMeter();
    static void _publishGrid();
    static void _publishEnergy();
    static void _publishSystemDynamic();
    static void _publishStatistics();
    static void _publishCrash();
    static void _publishLog(const LogEntry& entry);
    static void _publishAlarm(const AlarmEntry& entry);
    static void _publishOtaJobsRequest();

    static void _processAlarmQueue();
    static void _checkPublishMqtt();
    static void _checkIfPublishMeterNeeded();
    static void _checkIfPublishGridNeeded();
    static bool _allActiveChannelsFreshSinceBoundary(uint64_t boundaryUnixMs);
    static void _checkIfPublishEnergyNeeded();
    static void _checkIfPublishSystemDynamicNeeded();
    static void _checkIfPublishStatisticsNeeded();
    static void _checkIfPublishCrashNeeded();

    // Outcome of publishing one archived crash record. The two failure modes are
    // kept apart deliberately: Retry leaves the record at the head of the queue,
    // Skip steps over one that can never be sent so it cannot stall the rest.
    enum class CrashPublishOutcome {
        Published,
        Empty,   // Nothing archived at this index
        Retry,   // Transient failure, try the same record again later
        Skip,    // Permanently unpublishable, but kept on flash
        Dropped, // Corrupt record removed; the remaining ones shifted down
    };
    static CrashPublishOutcome _publishCrashJson(uint32_t index);

    // MQTT operations
    static bool _setCertificatesFromPreferences();
    static bool _setupMqttWithDeviceCertificates();
    static bool _connectMqtt();
    static bool _publishJsonStreaming(JsonDocument &jsonDocument, const char* topic, bool retain = false);

    // Queue processing and streaming
    static void _processLogQueue();
    static bool _publishMeterStreaming();
    static bool _publishMeterJson();
    static bool _publishOtaJobsRequestJson();
    
    // Certificate management
    static void _clearCertificatesRuntime();
    static bool _validateCertificateFormat(const char* cert, const char* certType);

    // Connection handling
    static void _handleConnecting();
    static void _handleConnectedState();

    // Utilities
    static const char* _getMqttStateReason(int32_t state);
    bool extractHost(const char* url, char* buffer, size_t bufferSize);

    // Public API functions
    // ====================
    // ====================

    void begin()
    {
        LOG_DEBUG("Setting up MQTT client...");

        if (!createMutexIfNeeded(&_configMutex)) {
            LOG_ERROR("Failed to create configuration mutex");
            return;
        }

        // Static and permanent config
        if (!_clientMqtt.setBufferSize(MQTT_BUFFER_SIZE)) {
            LOG_ERROR("Failed to allocate %d-byte MQTT buffer; cloud connection may be unstable", MQTT_BUFFER_SIZE);
        }
        LOG_DEBUG("MQTT buffer set to %d bytes; free internal heap now %u bytes", MQTT_BUFFER_SIZE, (unsigned)ESP.getFreeHeap());
        _clientMqtt.setKeepAlive(MQTT_OVERRIDE_KEEPALIVE);
        _clientMqtt.setServer(AWS_IOT_CORE_ENDPOINT, AWS_IOT_CORE_PORT);
        _clientMqtt.setCallback(_subscribeCallback);

        _setupTopics();
        _loadConfigFromPreferences();
        Shadow::begin();
        _initializeLogQueue();
        _initializeMeterQueue();
        _initializeGridQueue();
        _initializeAlarmQueue();
        
        // Initialize OTA buffers before checking pending validation
        if (_otaCurrentUrl == nullptr) {
            _otaCurrentUrl = (char*)ps_malloc(OTA_PRESIGNED_URL_BUFFER_SIZE);
            if (_otaCurrentUrl == nullptr) {
                LOG_ERROR("Failed to allocate OTA URL buffer in PSRAM");
            } else {
                memset(_otaCurrentUrl, 0, OTA_PRESIGNED_URL_BUFFER_SIZE);
            }
        }

        if (_otaHashChunkBuffer == nullptr) {
            _otaHashChunkBuffer = (uint8_t*)ps_malloc(OTA_SIGNATURE_HASH_CHUNK_SIZE);
            if (_otaHashChunkBuffer == nullptr) {
                LOG_ERROR("Failed to allocate OTA signature hash chunk buffer in PSRAM");
            }
        }

        memset(_otaCurrentJobId, 0, sizeof(_otaCurrentJobId));
        
        // Check if we just rebooted after an OTA update (must be AFTER memset to allow job ID loading)
        _checkPendingOtaValidation();

        // Allocate certificate buffers in PSRAM
        if (_awsIotCoreCert == nullptr) {
            _awsIotCoreCert = (char*)ps_malloc(CERTIFICATE_BUFFER_SIZE);
            if (_awsIotCoreCert == nullptr) {
                LOG_ERROR("Failed to allocate certificate buffer in PSRAM");
            } else {
                memset(_awsIotCoreCert, 0, CERTIFICATE_BUFFER_SIZE);
            }
        }
        
        if (_awsIotCorePrivateKey == nullptr) {
            _awsIotCorePrivateKey = (char*)ps_malloc(CERTIFICATE_BUFFER_SIZE);
            if (_awsIotCorePrivateKey == nullptr) {
                LOG_ERROR("Failed to allocate private key buffer in PSRAM");
            } else {
                memset(_awsIotCorePrivateKey, 0, CERTIFICATE_BUFFER_SIZE);
            }
        }

        // Eager certificate loading: certs are factory-provisioned and permanent
        _certificatesLoaded = _setupMqttWithDeviceCertificates();
        if (!_certificatesLoaded) {
            LOG_ERROR("Failed to load device certificates in begin(). Cloud services will not connect.");
        }

        if (_cloudServicesEnabled && _certificatesLoaded) _startTask();
        else if (_cloudServicesEnabled && !_certificatesLoaded) LOG_WARNING("Cloud services enabled but certificates not loaded - reprovision required");
        else LOG_DEBUG("Cloud services are disabled, MQTT task will not start");

        LOG_DEBUG("MQTT client setup complete");
    }

    void stop()
    {
        LOG_DEBUG("Stopping MQTT client...");
        _stopTask();
        
        // Queues and the config mutex are kept: other tasks (pushLog from any LOG_*, web handlers
        // via setCloudServicesEnabled) can still reach them during the restart sequence, and
        // freeing them under a live user is a use-after-free. A reboot follows.

        // Zeroize and free certificate buffers
        if (_awsIotCoreCert != nullptr) {
            memset(_awsIotCoreCert, 0, CERTIFICATE_BUFFER_SIZE);
            free(_awsIotCoreCert);
            _awsIotCoreCert = nullptr;
        }
        
        if (_awsIotCorePrivateKey != nullptr) {
            memset(_awsIotCorePrivateKey, 0, CERTIFICATE_BUFFER_SIZE);
            free(_awsIotCorePrivateKey);
            _awsIotCorePrivateKey = nullptr;
        }
        
        // Wake a running OTA task out of its backoff so it gives up rather than
        // sitting out a wait that can reach OTA_DOWNLOAD_RETRY_MAX_INTERVAL.
        if (_otaTaskHandle != nullptr) xTaskNotifyGive(_otaTaskHandle);

        // Free OTA URL buffer, unless the OTA task is still alive: it re-reads
        // this buffer at the top of every retry attempt, and the retry schedule
        // keeps the task around for far longer than a single download. Leaking
        // it is the cheap side of that trade - stop() is followed by a reboot.
        if (_otaCurrentUrl != nullptr && _otaTaskHandle == nullptr) {
            memset(_otaCurrentUrl, 0, OTA_PRESIGNED_URL_BUFFER_SIZE);
            free(_otaCurrentUrl);
            _otaCurrentUrl = nullptr;
        }
        
        LOG_INFO("MQTT client stopped");
    }

    // Cloud services methods
    // ======================

    void setCloudServicesEnabled(bool enabled)
    {
        if (_configMutex == nullptr) begin();
        if (!acquireMutex(&_configMutex, CONFIG_MUTEX_TIMEOUT_MS)) {
            LOG_ERROR("Failed to acquire configuration mutex for setCloudServicesEnabled");
            return;
        }

        if (_cloudServicesEnabled == enabled) {
            LOG_DEBUG("Cloud services already set to %s, skipping", enabled ? "enabled" : "disabled");
            releaseMutex(&_configMutex);
            return;
        }

        LOG_DEBUG("Setting cloud services to %s...", enabled ? "enabled" : "disabled");
        
        _stopTask();

        _cloudServicesEnabled = enabled;
        _saveCloudServicesEnabledToPreferences(enabled);

        if (_cloudServicesEnabled && _certificatesLoaded) _startTask();
        else if (_cloudServicesEnabled && !_certificatesLoaded) LOG_WARNING("Cannot start MQTT task: device certificates not loaded - reprovision required");
        
        releaseMutex(&_configMutex);

        LOG_INFO("Cloud services %s", enabled ? "enabled" : "disabled");
    }

    bool isCloudServicesEnabled() { return _cloudServicesEnabled; }

    bool isConnected() { return _lastConnectedState; }

    // Public methods for requesting MQTT publications
    // ===============================================

    // Channel config now lives in the channels shadow; a channel change (REST,
    // auto-polarity, etc.) refreshes the shadow's reported state instead of
    // publishing the retired `channel` topic.
    void requestChannelPublish() { Shadow::requestReport("channels"); }
    void requestCrashPublish() {_publishMqtt.crash = true; }

    void requestImmediatePublish()
    {
        if (_taskHandle == nullptr) return;
        xTaskNotify(_taskHandle, MQTT_NOTIFY_WAKE_BIT, eSetBits);
    }

    // Public methods for pushing data to queues
    // =========================================

    void pushLog(const LogEntry& entry)
    {
        if (!_initializeLogQueue()) return;

        // Fast log level filtering using precomputed minimum level
        if (entry.level < _mqttMinLogLevel) {
            return;
        }
        
        // Filter out logs from MQTT publishing functions to prevent infinite loops
        if (strstr(entry.function, "_publishLog") != nullptr ||
            strstr(entry.function, "_publishJsonStreaming") != nullptr
        ) {
            return; // Skip logs from MQTT publishing functions
        }
        
        xQueueSend(_logQueue, &entry, pdMS_TO_TICKS(QUEUE_WAIT_TIMEOUT));
    }

    void pushMeter(const PayloadMeter& payload)
    {
        if (!_initializeMeterQueue()) return;
        if (!_sendPowerDataEnabled) return;

        // Drop-oldest on overflow: recent points are worth more than old ones
        if (xQueueSend(_meterQueue, &payload, 0) != pdTRUE) {
            PayloadMeter discarded;
            xQueueReceive(_meterQueue, &discarded, 0);
            xQueueSend(_meterQueue, &payload, 0);
            statistics.mqttMeterPointsDropped++;
        }
    }

    void pushGrid(const PayloadGridPoint& point)
    {
        if (!_initializeGridQueue()) return;
        if (!_sendGridDataEnabled) return; // Sampler already gates on this

        // Drop-oldest on overflow: recent points are worth more than old ones
        if (xQueueSend(_gridQueue, &point, 0) != pdTRUE) {
            PayloadGridPoint discarded;
            xQueueReceive(_gridQueue, &discarded, 0);
            xQueueSend(_gridQueue, &point, 0);
            statistics.mqttGridPointsDropped++;
        }
    }

    void pushAlarm(const AlarmEntry& entry)
    {
        if (!_initializeAlarmQueue()) return;
        // No drop-oldest (unlike meter/grid) - losing an alarm silently isn't
        // acceptable; block briefly instead (same as pushLog).
        if (xQueueSend(_alarmQueue, &entry, pdMS_TO_TICKS(QUEUE_WAIT_TIMEOUT)) != pdTRUE) {
            LOG_WARNING("MQTT alarm queue full, dropping alarm: %s", entry.type);
        }
        requestImmediatePublish();
    }

    TaskInfo getMqttTaskInfo()
    {
        return getTaskInfoSafely(_taskHandle, MQTT_TASK_STACK_SIZE, &_mqttHeartbeat);
    }

    TaskInfo getMqttOtaTaskInfo()
    {
        return getTaskInfoSafely(_otaTaskHandle, OTA_TASK_STACK_SIZE);
    }

    // Shadow module helpers
    // =====================

    bool subscribeReservedThings(const char* finalTopic) {
        char topic[MQTT_TOPIC_BUFFER_SIZE];
        _constructMqttTopicReservedThings(finalTopic, topic, sizeof(topic));
        if (!_clientMqtt.subscribe(topic, MQTT_TOPIC_SUBSCRIBE_QOS)) {
            LOG_WARNING("Failed to subscribe to %s", topic);
            return false;
        }
        LOG_DEBUG("Subscribed to %s", topic);
        return true;
    }

    bool publishReservedThings(JsonDocument& jsonDocument, const char* finalTopic, bool retain) {
        char topic[MQTT_TOPIC_BUFFER_SIZE];
        _constructMqttTopicReservedThings(finalTopic, topic, sizeof(topic));
        return _publishJsonStreaming(jsonDocument, topic, retain);
    }

    int getMqttLogLevel() { return _mqttLogLevelInt; }

    void setMqttLogLevel(const char* level) { _setMqttLogLevel(level); } // validates + persists

    void setRuntimeLogLevel(int level) {
        if (level < 0 || level > 5) {
            LOG_WARNING("Invalid runtime log level %d", level);
            return;
        }
        if (!acquireMutex(&_configMutex, CONFIG_MUTEX_TIMEOUT_MS)) {
            LOG_ERROR("Failed to acquire config mutex for runtime log level");
            return;
        }
        _mqttLogLevelInt = (uint8_t)level;
        _updateMqttMinLogLevel();
        releaseMutex(&_configMutex);
        // Intentionally NOT persisted here: the runtime int stays transient. The
        // separate transient marker (saveTransientLogLevel) is what survives a
        // reboot; the persisted baseline key is never touched by a transient.
    }

    void saveTransientLogLevel(int level) {
        if (level < 0 || level > 5) return;
        Preferences prefs;
        if (!prefs.begin(PREFERENCES_NAMESPACE_MQTT, false)) {
            LOG_WARNING("Failed to open preferences to save transient log level");
            return;
        }
        // Write only on change: a long cloud-held verbose window re-asserts the
        // same level every <5 min, and we must not wear flash for a no-op.
        if (prefs.getUChar(MQTT_PREFERENCES_TRANSIENT_LOG_LEVEL_KEY, 0xFF) != (uint8_t)level) {
            prefs.putUChar(MQTT_PREFERENCES_TRANSIENT_LOG_LEVEL_KEY, (uint8_t)level);
        }
        prefs.end();
    }

    void clearTransientLogLevel() {
        Preferences prefs;
        if (!prefs.begin(PREFERENCES_NAMESPACE_MQTT, false)) return;
        if (prefs.isKey(MQTT_PREFERENCES_TRANSIENT_LOG_LEVEL_KEY)) {
            prefs.remove(MQTT_PREFERENCES_TRANSIENT_LOG_LEVEL_KEY);
        }
        prefs.end();
    }

    int getTransientLogLevel() {
        Preferences prefs;
        if (!prefs.begin(PREFERENCES_NAMESPACE_MQTT, true)) return -1;
        uint8_t v = prefs.getUChar(MQTT_PREFERENCES_TRANSIENT_LOG_LEVEL_KEY, 0xFF);
        prefs.end();
        return (v == 0xFF) ? -1 : (int)v;
    }

    bool getSendPowerData() { return _sendPowerDataEnabled; }

    void setSendPowerData(bool enabled) { _setSendPowerDataEnabled(enabled); } // persists

    bool getSendGridData() { return _sendGridDataEnabled; }

    void setSendGridData(bool enabled) { _setSendGridDataEnabled(enabled); } // persists

    uint32_t getMeterPublishThresholdBytes() { return _meterPublishThresholdBytes; }

    void setMeterPublishThresholdBytes(uint32_t bytes) { _setMeterPublishThresholdBytes(bytes); } // persists, clamped

    uint32_t getMeterPublishMaxIntervalMs() { return _meterPublishMaxIntervalMs; }

    void setMeterPublishMaxIntervalMs(uint32_t intervalMs) { _setMeterPublishMaxIntervalMs(intervalMs); } // persists, clamped

    // Private functions
    // =================
    // =================


    // MQTT log queue management
    // =========================

    bool _initializeLogQueue() // Cannot use logger here to avoid recursion
    {
        static bool isInitializing = false; // Guard against re-entry during initialization
        
        if (_logQueueStorage != nullptr) return true;
        
        // Prevent recursion if ESP-IDF logs during preferences access
        if (isInitializing) {
            Serial.printf("[WARNING] Re-entry detected in _initializeLogQueue, skipping to prevent recursion\n");
            return false;
        }
        
        isInitializing = true;

        // Load MQTT log level from preferences before initializing queue
        // Using read-only mode to minimize risk of triggering internal ESP-IDF logs
        Preferences prefs;
        if (prefs.begin(PREFERENCES_NAMESPACE_MQTT, true)) {
            _mqttLogLevelInt = prefs.getUChar(MQTT_PREFERENCES_MQTT_LOG_LEVEL_KEY, DEFAULT_MQTT_LOG_LEVEL_INT);
            prefs.end();
            _updateMqttMinLogLevel(); // Convert integer to LogLevel enum
            Serial.printf("[DEBUG] MQTT log level loaded from preferences: %u\n", _mqttLogLevelInt);
        } else {
            // Failed to open preferences, use default
            Serial.printf("[WARNING] Failed to load MQTT log level from preferences, using default: %u\n", DEFAULT_MQTT_LOG_LEVEL_INT);
            _mqttLogLevelInt = DEFAULT_MQTT_LOG_LEVEL_INT;
            _updateMqttMinLogLevel();
        }

        // Allocate queue storage in PSRAM
        uint32_t queueLength = MQTT_LOG_QUEUE_SIZE / sizeof(LogEntry);
        size_t realQueueSize = queueLength * sizeof(LogEntry);
        _logQueueStorage = (uint8_t*)ps_malloc(realQueueSize);

        if (_logQueueStorage == nullptr) {
            Serial.printf("[ERROR] Failed to allocate PSRAM for MQTT log queue (%d bytes)\n", realQueueSize);
            isInitializing = false;
            return false;
        }

        _logQueue = xQueueCreateStatic(queueLength, sizeof(LogEntry), _logQueueStorage, &_logQueueStruct);
        if (_logQueue == nullptr) {
            Serial.println("[ERROR] Failed to create MQTT log queue");
            free(_logQueueStorage);
            _logQueueStorage = nullptr;
            isInitializing = false;
            return false;
        }

        Serial.printf("[DEBUG] MQTT log queue initialized with PSRAM buffer (%d bytes) | Free PSRAM: %d bytes\n", realQueueSize, heap_caps_get_free_size(MALLOC_CAP_SPIRAM));
        isInitializing = false;
        return true;
    }

    bool _initializeMeterQueue()
    {
        if (_meterQueueStorage != nullptr) return true;

        // Allocate queue storage in PSRAM
        uint32_t queueLength = MQTT_METER_QUEUE_SIZE / sizeof(PayloadMeter);
        size_t realQueueSize = queueLength * sizeof(PayloadMeter);
        _meterQueueStorage = (uint8_t*)ps_malloc(realQueueSize);

        if (_meterQueueStorage == nullptr) {
            LOG_ERROR("Failed to allocate PSRAM for MQTT meter queue (%zu bytes)\n", realQueueSize);
            return false;
        }

        _meterQueue = xQueueCreateStatic(queueLength, sizeof(PayloadMeter), _meterQueueStorage, &_meterQueueStruct);
        if (_meterQueue == nullptr) {
            LOG_ERROR("Failed to create MQTT meter queue\n");
            free(_meterQueueStorage);
            _meterQueueStorage = nullptr;
            return false;
        }

        LOG_DEBUG("MQTT meter queue initialized with PSRAM buffer (%zu bytes) | Free PSRAM: %zu bytes\n", realQueueSize, heap_caps_get_free_size(MALLOC_CAP_SPIRAM));
        return true;
    }

    bool _initializeGridQueue()
    {
        if (_gridQueueStorage != nullptr) return true;

        // Allocate queue storage in PSRAM
        uint32_t queueLength = MQTT_GRID_QUEUE_SIZE / sizeof(PayloadGridPoint);
        size_t realQueueSize = queueLength * sizeof(PayloadGridPoint);
        _gridQueueStorage = (uint8_t*)ps_malloc(realQueueSize);

        if (_gridQueueStorage == nullptr) {
            LOG_ERROR("Failed to allocate PSRAM for MQTT grid queue (%zu bytes)", realQueueSize);
            return false;
        }

        _gridQueue = xQueueCreateStatic(queueLength, sizeof(PayloadGridPoint), _gridQueueStorage, &_gridQueueStruct);
        if (_gridQueue == nullptr) {
            LOG_ERROR("Failed to create MQTT grid queue");
            free(_gridQueueStorage);
            _gridQueueStorage = nullptr;
            return false;
        }

        LOG_DEBUG("MQTT grid queue initialized with PSRAM buffer (%zu bytes) | Free PSRAM: %zu bytes", realQueueSize, heap_caps_get_free_size(MALLOC_CAP_SPIRAM));
        return true;
    }

    bool _initializeAlarmQueue()
    {
        if (_alarmQueueStorage != nullptr) return true;

        // Allocate queue storage in PSRAM
        uint32_t queueLength = MQTT_ALARM_QUEUE_SIZE / sizeof(AlarmEntry);
        size_t realQueueSize = queueLength * sizeof(AlarmEntry);
        _alarmQueueStorage = (uint8_t*)ps_malloc(realQueueSize);

        if (_alarmQueueStorage == nullptr) {
            LOG_ERROR("Failed to allocate PSRAM for MQTT alarm queue (%zu bytes)", realQueueSize);
            return false;
        }

        _alarmQueue = xQueueCreateStatic(queueLength, sizeof(AlarmEntry), _alarmQueueStorage, &_alarmQueueStruct);
        if (_alarmQueue == nullptr) {
            LOG_ERROR("Failed to create MQTT alarm queue");
            free(_alarmQueueStorage);
            _alarmQueueStorage = nullptr;
            return false;
        }

        LOG_DEBUG("MQTT alarm queue initialized with PSRAM buffer (%zu bytes) | Free PSRAM: %zu bytes", realQueueSize, heap_caps_get_free_size(MALLOC_CAP_SPIRAM));
        return true;
    }

    // Configuration management
    // ========================
    
    static void _loadConfigFromPreferences()
    {
        if (!acquireMutex(&_configMutex, CONFIG_MUTEX_TIMEOUT_MS)) {
            LOG_ERROR("Failed to acquire configuration mutex for loading preferences");
            return;
        }

        Preferences prefs;
        prefs.begin(PREFERENCES_NAMESPACE_MQTT, true);

        _cloudServicesEnabled = prefs.getBool(MQTT_PREFERENCES_IS_CLOUD_SERVICES_ENABLED_KEY, DEFAULT_CLOUD_SERVICES_ENABLED);
        _sendPowerDataEnabled = prefs.getBool(MQTT_PREFERENCES_SEND_POWER_DATA_KEY, DEFAULT_SEND_POWER_DATA_ENABLED);
        _sendGridDataEnabled = prefs.getBool(MQTT_PREFERENCES_SEND_GRID_DATA_KEY, DEFAULT_SEND_GRID_DATA_ENABLED);
        _meterPublishThresholdBytes = prefs.getUInt(MQTT_PREFERENCES_METER_PUBLISH_THRESHOLD_KEY, MQTT_METER_PUBLISH_THRESHOLD_BYTES_DEFAULT);
        _meterPublishMaxIntervalMs = prefs.getUInt(MQTT_PREFERENCES_METER_PUBLISH_INTERVAL_KEY, MQTT_METER_PUBLISH_MAX_INTERVAL_MS_DEFAULT);
        _mqttLogLevelInt = prefs.getUChar(MQTT_PREFERENCES_MQTT_LOG_LEVEL_KEY, DEFAULT_MQTT_LOG_LEVEL_INT);
        _updateMqttMinLogLevel(); // Convert integer to LogLevel enum

        LOG_DEBUG("Cloud services enabled: %s, Send power data enabled: %s, Send grid data enabled: %s, "
                   "Meter publish threshold: %u bytes, Meter publish max interval: %u ms, MQTT log level: %u",
                   _cloudServicesEnabled ? "true" : "false",
                   _sendPowerDataEnabled ? "true" : "false",
                   _sendGridDataEnabled ? "true" : "false",
                   _meterPublishThresholdBytes,
                   _meterPublishMaxIntervalMs,
                   _mqttLogLevelInt);

        prefs.end();
        releaseMutex(&_configMutex);

        _saveConfigToPreferences();
        LOG_DEBUG("MQTT preferences loaded");
    }

    static void _saveConfigToPreferences()
    {
        _saveCloudServicesEnabledToPreferences(_cloudServicesEnabled);
        _saveSendPowerDataEnabledToPreferences(_sendPowerDataEnabled);
        _saveSendGridDataEnabledToPreferences(_sendGridDataEnabled);
        _saveMeterPublishThresholdBytesToPreferences(_meterPublishThresholdBytes);
        _saveMeterPublishMaxIntervalMsToPreferences(_meterPublishMaxIntervalMs);
        _saveMqttLogLevelToPreferences(_mqttLogLevelInt);
        
        LOG_DEBUG("MQTT preferences saved");
    }

    static void _setSendPowerDataEnabled(bool enabled)
    {
        _sendPowerDataEnabled = enabled;
        _saveSendPowerDataEnabledToPreferences(enabled);
        LOG_DEBUG("Set send power data enabled to %s", enabled ? "true" : "false");
    }

    static void _setSendGridDataEnabled(bool enabled)
    {
        _sendGridDataEnabled = enabled;
        _saveSendGridDataEnabledToPreferences(enabled);
        LOG_DEBUG("Set send grid data enabled to %s", enabled ? "true" : "false");
    }

    static void _setMeterPublishThresholdBytes(uint32_t bytes)
    {
        uint32_t clamped = std::clamp<uint32_t>(bytes, MQTT_METER_PUBLISH_THRESHOLD_BYTES_MIN, MQTT_METER_PUBLISH_THRESHOLD_BYTES_MAX);
        if (clamped != bytes) {
            LOG_WARNING("Requested meter publish threshold %u bytes out of range [%u, %u], clamped to %u bytes",
                        bytes, MQTT_METER_PUBLISH_THRESHOLD_BYTES_MIN, MQTT_METER_PUBLISH_THRESHOLD_BYTES_MAX, clamped);
        }
        _meterPublishThresholdBytes = clamped;
        _saveMeterPublishThresholdBytesToPreferences(clamped);
        LOG_DEBUG("Set meter publish threshold to %u bytes", clamped);
    }

    static void _setMeterPublishMaxIntervalMs(uint32_t intervalMs)
    {
        uint32_t clamped = std::clamp<uint32_t>(intervalMs, MQTT_METER_PUBLISH_MAX_INTERVAL_MS_MIN, MQTT_METER_PUBLISH_MAX_INTERVAL_MS_MAX);
        if (clamped != intervalMs) {
            LOG_WARNING("Requested meter publish max interval %u ms out of range [%u, %u], clamped to %u ms",
                        intervalMs, MQTT_METER_PUBLISH_MAX_INTERVAL_MS_MIN, MQTT_METER_PUBLISH_MAX_INTERVAL_MS_MAX, clamped);
        }
        _meterPublishMaxIntervalMs = clamped;
        _saveMeterPublishMaxIntervalMsToPreferences(clamped);
        LOG_DEBUG("Set meter publish max interval to %u ms", clamped);
    }

    static void _updateMqttMinLogLevel()
    {
        // Convert integer to LogLevel enum (0=VERBOSE, 1=DEBUG, 2=INFO, 3=WARNING, 4=ERROR, 5=FATAL)
        switch (_mqttLogLevelInt) {
            case 0: _mqttMinLogLevel = LogLevel::VERBOSE; break; // Same as DEBUG in practice: VERBOSE never reaches the log callbacks (see main.cpp)
            case 1: _mqttMinLogLevel = LogLevel::DEBUG; break;
            case 2: _mqttMinLogLevel = LogLevel::INFO; break;
            case 3: _mqttMinLogLevel = LogLevel::WARNING; break;
            case 4: _mqttMinLogLevel = LogLevel::ERROR; break;
            case 5: _mqttMinLogLevel = LogLevel::FATAL; break;
            default: _mqttMinLogLevel = LogLevel::INFO; break; // Default fallback
        }
        Serial.printf("[DEBUG] Updated MQTT minimum log level to %u\n", _mqttLogLevelInt); // Cannot use LOG_DEBUG here to avoid recursion (this is called in _initializeLogQueue)
    }

    static void _setMqttLogLevel(const char* logLevel)
    {
        if (!acquireMutex(&_configMutex, CONFIG_MUTEX_TIMEOUT_MS)) {
            LOG_ERROR("Failed to acquire configuration mutex for setting MQTT log level");
            return;
        }

        if (logLevel == nullptr) {
            LOG_ERROR("Invalid MQTT log level provided");
            releaseMutex(&_configMutex);
            return;
        }

        // Convert string to integer
        uint8_t levelInt = DEFAULT_MQTT_LOG_LEVEL_INT; // Default fallback
        if (strcmp(logLevel, "VERBOSE") == 0) levelInt = 0;
        else if (strcmp(logLevel, "DEBUG") == 0) levelInt = 1;
        else if (strcmp(logLevel, "INFO") == 0) levelInt = 2;
        else if (strcmp(logLevel, "WARNING") == 0) levelInt = 3;
        else if (strcmp(logLevel, "ERROR") == 0) levelInt = 4;
        else if (strcmp(logLevel, "FATAL") == 0) levelInt = 5;
        else {
            LOG_ERROR("Invalid log level: %s", logLevel);
            releaseMutex(&_configMutex);
            return;
        }

        _mqttLogLevelInt = levelInt;
        _updateMqttMinLogLevel();
        _saveMqttLogLevelToPreferences(_mqttLogLevelInt);
        releaseMutex(&_configMutex);

        LOG_DEBUG("MQTT log level set to %s (%d)", logLevel, _mqttLogLevelInt);
    }

    static void _saveCloudServicesEnabledToPreferences(bool enabled) {
        Preferences prefs;
        
        prefs.begin(PREFERENCES_NAMESPACE_MQTT, false);
        size_t bytesWritten = prefs.putBool(MQTT_PREFERENCES_IS_CLOUD_SERVICES_ENABLED_KEY, enabled);
        if (bytesWritten == 0) LOG_ERROR("Failed to save cloud services enabled preference");

        prefs.end();
    }

    static void _saveSendPowerDataEnabledToPreferences(bool enabled) {
        Preferences prefs;

        prefs.begin(PREFERENCES_NAMESPACE_MQTT, false);
        size_t bytesWritten = prefs.putBool(MQTT_PREFERENCES_SEND_POWER_DATA_KEY, enabled);
        if (bytesWritten == 0) LOG_ERROR("Failed to save send power data enabled preference");
        
        prefs.end();
    }

    static void _saveSendGridDataEnabledToPreferences(bool enabled) {
        Preferences prefs;

        prefs.begin(PREFERENCES_NAMESPACE_MQTT, false);
        size_t bytesWritten = prefs.putBool(MQTT_PREFERENCES_SEND_GRID_DATA_KEY, enabled);
        if (bytesWritten == 0) LOG_ERROR("Failed to save send grid data enabled preference");

        prefs.end();
    }

    static void _saveMeterPublishThresholdBytesToPreferences(uint32_t bytes) {
        Preferences prefs;

        prefs.begin(PREFERENCES_NAMESPACE_MQTT, false);
        size_t bytesWritten = prefs.putUInt(MQTT_PREFERENCES_METER_PUBLISH_THRESHOLD_KEY, bytes);
        if (bytesWritten == 0) LOG_ERROR("Failed to save meter publish threshold preference");

        prefs.end();
    }

    static void _saveMeterPublishMaxIntervalMsToPreferences(uint32_t intervalMs) {
        Preferences prefs;

        prefs.begin(PREFERENCES_NAMESPACE_MQTT, false);
        size_t bytesWritten = prefs.putUInt(MQTT_PREFERENCES_METER_PUBLISH_INTERVAL_KEY, intervalMs);
        if (bytesWritten == 0) LOG_ERROR("Failed to save meter publish max interval preference");

        prefs.end();
    }

    static void _saveMqttLogLevelToPreferences(uint8_t logLevel) {
        Preferences prefs;

        prefs.begin(PREFERENCES_NAMESPACE_MQTT, false);
        size_t bytesWritten = prefs.putUChar(MQTT_PREFERENCES_MQTT_LOG_LEVEL_KEY, logLevel);
        if (bytesWritten == 0) {
            LOG_ERROR("Failed to save MQTT log level preference: %d", logLevel);
        }
        
        prefs.end();
    }

    // Task management
    // ===============

    static void _startTask()
    {
        if (_taskHandle != nullptr) {
            LOG_DEBUG("MQTT task is already running");
            return;
        }

        LOG_DEBUG("Starting MQTT task");

        if (!_initializeLogQueue()) {
            LOG_ERROR("Failed to initialize MQTT log queue");
            return;
        }

        if (!_initializeMeterQueue()) {
            LOG_ERROR("Failed to initialize MQTT meter queue");
            return;
        }

        _nextMqttConnectionAttemptMillis = 0;
        _mqttConnectionAttempt = 0;
        
        LOG_DEBUG("Starting MQTT task with %d bytes stack", MQTT_TASK_STACK_SIZE);

        BaseType_t result = xTaskCreate(
            _mqttTask,
            MQTT_TASK_NAME,
            MQTT_TASK_STACK_SIZE,
            nullptr,
            MQTT_TASK_PRIORITY,
            &_taskHandle);

        if (result != pdPASS) {
            LOG_ERROR("Failed to create MQTT task");
            _taskHandle = nullptr;
        }
    }

    static void _stopTask() { 
        stopTaskGracefully(&_taskHandle, "MQTT task"); 
    }

    static void _mqttTask(void *parameter)
    {
        LOG_DEBUG("MQTT task started");
        
        _taskShouldRun = true;
        _lastLoopToPublishData = false;

        while (_taskShouldRun)
        {
            TASK_HEARTBEAT(_mqttHeartbeat);

            bool connectedNow = false;
            if (CustomNet::isFullyConnected()) {
                if (_clientMqtt.connected()) {
                    connectedNow = true;
                    _handleConnectedState();
                } else {
                    _handleConnecting();
                }
            }
            _lastConnectedState = connectedNow;

            // If we receive a signal to stop the task, we try to publish all the data and flushing the queues so we avoid losing data
            if (_lastLoopToPublishData) {
                _lastLoopToPublishData = false;
                _taskShouldRun = false;
            } else {
                // Wake early on notification (e.g. pushAlarm's requestImmediatePublish)
                // instead of waiting the full interval. Only the shutdown bit takes
                // the flush-and-stop branch below.
                uint32_t notifiedBits = 0;
                xTaskNotifyWait(0, ULONG_MAX, &notifiedBits, pdMS_TO_TICKS(MQTT_LOOP_INTERVAL));

                if (notifiedBits & TASK_NOTIFY_SHUTDOWN_BIT) {
                    _lastLoopToPublishData = true;
                    _publishMqtt.meter = true;
                    _publishMqtt.systemDynamic = true;
                    _publishMqtt.statistics = true;
                    break;
                }
            }
        }

        _clientMqtt.disconnect();
        _lastConnectedState = false;
        LOG_DEBUG("MQTT task stopping");
        _taskHandle = nullptr;
        vTaskDelete(nullptr);
    }

    // Topic management
    // ================

    // Product is a runtime (factory-NVS) value, not a build flag, so the topic
    // namespace segment and Basic Ingest rule names are picked here rather than
    // at compile time (see awsconfig.h).
    static const char* _selectByProduct(const char* homeValue, const char* homeProValue) {
        return (globalHwProfile->product == ProductLine::HOMEPRO) ? homeProValue : homeValue;
    }

    static const char* _topicProductSegment() { return _selectByProduct(MQTT_TOPIC_2_HOME, MQTT_TOPIC_2_HOMEPRO); }

    static void _constructMqttTopicReservedThings(const char* finalTopic, char* topicBuffer, size_t topicBufferSize) {
        // Example: $aws/things/588c81c47a5c/jobs/notify-next
        snprintf(
            topicBuffer,
            topicBufferSize,
            "%s/%s/%s",
            MQTT_THINGS,
            DEVICE_ID,
            finalTopic
        );

        LOG_DEBUG("Constructing MQTT reserved things topic for %s | %s", finalTopic, topicBuffer);
    }

    static void _constructMqttTopicWithRule(const char* ruleName, const char* finalTopic, char* topicBuffer, size_t topicBufferSize) {
        snprintf(
            topicBuffer,
            topicBufferSize,
            "%s/%s/%s/%s/%s/%s/%s",
            MQTT_BASIC_INGEST,
            ruleName,
            MQTT_TOPIC_1,
            _topicProductSegment(),
            MQTT_TOPIC_VERSION,
            DEVICE_ID,
            finalTopic
        );

        LOG_DEBUG("Constructing MQTT topic with rule for %s | %s", finalTopic, topicBuffer);
    }

    static void _constructMqttTopic(const char* finalTopic, char* topicBuffer, size_t topicBufferSize) {
        snprintf(
            topicBuffer,
            topicBufferSize,
            "%s/%s/%s/%s/%s",
            MQTT_TOPIC_1,
            _topicProductSegment(),
            MQTT_TOPIC_VERSION,
            DEVICE_ID,
            finalTopic
        );

        LOG_DEBUG("Constructing MQTT topic for %s | %s", finalTopic, topicBuffer);
    }

    // AWS IoT Commands execution topic: $aws/commands/things/<thing>/executions/
    // <executionId>/<verb>. executionId is "+" for the subscribe wildcard; verb is
    // "request/json" or "response/json".
    static void _constructCommandTopic(const char* executionId, const char* verb,
                                       char* topicBuffer, size_t topicBufferSize) {
        snprintf(topicBuffer, topicBufferSize, "%s/commands/things/%s/executions/%s/%s",
                 AWS_TOPIC, DEVICE_ID, executionId, verb);
    }

    static void _setupTopics() {
        _setTopicMeter();
        _setTopicGrid();
        _setTopicEnergy();
        _setTopicSystemDynamic();
        _setTopicStatistics();
        _setTopicCrash();
        _setTopicLog();
        _setTopicAlarm();

        LOG_DEBUG("MQTT topics setup complete");
    }

    static void _setTopicMeter() { _constructMqttTopicWithRule(_selectByProduct(AWS_IOT_CORE_RULE_METER_HOME, AWS_IOT_CORE_RULE_METER_HOMEPRO), MQTT_TOPIC_METER, _mqttTopicMeter, sizeof(_mqttTopicMeter)); }
    static void _setTopicGrid() { _constructMqttTopicWithRule(_selectByProduct(AWS_IOT_CORE_RULE_GRID_HOME, AWS_IOT_CORE_RULE_GRID_HOMEPRO), MQTT_TOPIC_GRID, _mqttTopicGrid, sizeof(_mqttTopicGrid)); }
    static void _setTopicEnergy() { _constructMqttTopicWithRule(_selectByProduct(AWS_IOT_CORE_RULE_ENERGY_HOME, AWS_IOT_CORE_RULE_ENERGY_HOMEPRO), MQTT_TOPIC_ENERGY, _mqttTopicEnergy, sizeof(_mqttTopicEnergy)); }
    static void _setTopicSystemDynamic() { _constructMqttTopic(MQTT_TOPIC_SYSTEM_DYNAMIC, _mqttTopicSystemDynamic, sizeof(_mqttTopicSystemDynamic)); }
    static void _setTopicStatistics() { _constructMqttTopic(MQTT_TOPIC_STATISTICS, _mqttTopicStatistics, sizeof(_mqttTopicStatistics)); }
    static void _setTopicCrash() { _constructMqttTopic(MQTT_TOPIC_CRASH, _mqttTopicCrash, sizeof(_mqttTopicCrash)); }
    static void _setTopicLog() { _constructMqttTopicWithRule(_selectByProduct(AWS_IOT_CORE_RULE_LOG_HOME, AWS_IOT_CORE_RULE_LOG_HOMEPRO), MQTT_TOPIC_LOG, _mqttTopicLog, sizeof(_mqttTopicLog)); }
    static void _setTopicAlarm() { _constructMqttTopicWithRule(_selectByProduct(AWS_IOT_CORE_RULE_ALARM_HOME, AWS_IOT_CORE_RULE_ALARM_HOMEPRO), MQTT_TOPIC_ALARM, _mqttTopicAlarm, sizeof(_mqttTopicAlarm)); }

    static void _subscribeToTopics() {
        _subscribeAwsIotJobs();
        // IoT Commands request topic (payload-format pinned to "json"; see
        // MQTT_IOT_COMMANDS_SUBSCRIBE_ENABLED). The earlier '+' at the payload-format
        // position was an unsupported reserved-topic subscribe -> broker CLIENT_ERROR
        // reconnect storm; the corrected topic is safe even before a dispatcher exists.
        if (MQTT_IOT_COMMANDS_SUBSCRIBE_ENABLED) _subscribeIotCommands();
        Shadow::onMqttConnected(); // subscribe shadow deltas + queue initial reports

        LOG_DEBUG("Subscribed to topics");
    }

    static void _subscribeIotCommands() {
        // AWS IoT Commands request topic. '+' is the execution-id wildcard only;
        // the payload-format segment must be a concrete value ("json"), NOT a '+'
        // wildcard. A '+' there is an unsupported reserved-topic subscribe and the
        // broker drops the whole session with CLIENT_ERROR (the ~1.2 s reconnect
        // storm we hit). The cloud dispatcher must create commands with contentType
        // application/json to match. Policy AllowSubscribe covers
        // $aws/commands/things/<thing>/*.
        char topic[MQTT_TOPIC_BUFFER_SIZE];
        _constructCommandTopic("+", "request/json", topic, sizeof(topic));
        if (_clientMqtt.subscribe(topic, MQTT_TOPIC_SUBSCRIBE_QOS)) {
            LOG_DEBUG("Subscribed to IoT Commands: %s", topic);
        } else {
            LOG_WARNING("Failed to subscribe to IoT Commands: %s", topic);
        }
    }

    static void _subscribeAwsIotJobs() {
        char jobNotifyTopic[MQTT_TOPIC_BUFFER_SIZE];
        _constructMqttTopicReservedThings("jobs/notify-next", jobNotifyTopic, sizeof(jobNotifyTopic));
        
        char jobsAcceptedTopic[MQTT_TOPIC_BUFFER_SIZE];
        _constructMqttTopicReservedThings("jobs/get/accepted", jobsAcceptedTopic, sizeof(jobsAcceptedTopic));

        char jobAcceptedTopic[MQTT_TOPIC_BUFFER_SIZE];
        _constructMqttTopicReservedThings("jobs/+/get/accepted", jobAcceptedTopic, sizeof(jobAcceptedTopic));

        // Rejected only: /update/accepted would echo every progress update back
        char jobUpdateRejectedTopic[MQTT_TOPIC_BUFFER_SIZE];
        _constructMqttTopicReservedThings("jobs/+/update/rejected", jobUpdateRejectedTopic, sizeof(jobUpdateRejectedTopic));

        LOG_DEBUG("Attempting to subscribe to: %s", jobNotifyTopic);
        if (_clientMqtt.subscribe(jobNotifyTopic, MQTT_TOPIC_SUBSCRIBE_QOS)) {
            LOG_DEBUG("Subscribed to AWS IoT Jobs notify topic: %s", jobNotifyTopic);
        } else {
            LOG_WARNING("Failed to subscribe to AWS IoT Jobs notify topic: %s", jobNotifyTopic);
        }
        
        LOG_DEBUG("Attempting to subscribe to: %s", jobsAcceptedTopic);
        if (_clientMqtt.subscribe(jobsAcceptedTopic, MQTT_TOPIC_SUBSCRIBE_QOS)) {
            LOG_DEBUG("Subscribed to AWS IoT Jobs accepted topic: %s", jobsAcceptedTopic);
        } else {
            LOG_WARNING("Failed to subscribe to AWS IoT Jobs accepted topic: %s", jobsAcceptedTopic);
        }

        LOG_DEBUG("Attempting to subscribe to: %s", jobAcceptedTopic);
        if (_clientMqtt.subscribe(jobAcceptedTopic, MQTT_TOPIC_SUBSCRIBE_QOS)) {
            LOG_DEBUG("Subscribed to AWS IoT Job accepted topic: %s", jobAcceptedTopic);
        } else {
            LOG_WARNING("Failed to subscribe to AWS IoT Job accepted topic: %s", jobAcceptedTopic);
        }

        if (_clientMqtt.subscribe(jobUpdateRejectedTopic, MQTT_TOPIC_SUBSCRIBE_QOS)) {
            LOG_DEBUG("Subscribed to AWS IoT Job update rejected topic: %s", jobUpdateRejectedTopic);
        } else {
            LOG_WARNING("Failed to subscribe to AWS IoT Job update rejected topic: %s", jobUpdateRejectedTopic);
        }
    }

    // Subscription callback handler
    // =============================

    static void _subscribeCallback(const char* topic, byte *payload, uint32_t length)
    {
        // Allocate message buffer in PSRAM to save stack memory
        char *message = (char*)ps_malloc(MQTT_SUBSCRIBE_MESSAGE_BUFFER_SIZE);
        if (!message) {
            LOG_ERROR("Failed to allocate subscribe message buffer in PSRAM");
            return;
        }
        
        // Ensure we don't exceed buffer bounds
        uint32_t maxLength = MQTT_SUBSCRIBE_MESSAGE_BUFFER_SIZE - 1; // Reserve space for null terminator
        if (length > maxLength) {
            LOG_WARNING("MQTT message from topic %s too large (%u bytes), truncating to %u", topic, length, maxLength);
            length = maxLength;
        }
        
        snprintf(message, MQTT_SUBSCRIBE_MESSAGE_BUFFER_SIZE, "%.*s", (int)length, (char*)payload);

        LOG_DEBUG("Received MQTT message from %s", topic);

        if (Shadow::routeMessage(topic, message)) { /* handled by shadow module (copy + flag only) */ }
        // Only the subscribed request topic (.../executions/<id>/request/json) is an
        // inbound command. Match it precisely - matching any "/commands/things/" topic
        // also catches AWS's own .../response/rejected/json echo of our status publish,
        // which has no 'operation', gets re-rejected, and echoes again -> infinite
        // publish loop hammering the broker.
        else if (strstr(topic, "/commands/things/") != nullptr && endsWith(topic, "/request/json")) _queueCommand(topic, message);
        else if (strstr(topic, "/commands/things/") != nullptr) {
            // AWS echoed our own command-status publish back (e.g. rejecting a status
            // for an unknown/expired execution). Never reprocess it - just note it.
            LOG_DEBUG("Ignoring non-request command topic: %s", topic);
        }
        else if (strstr(topic, MQTT_TOPIC_SUBSCRIBE_JOBS)) _handleAwsIotJobMessage(message, topic);
        else LOG_WARNING("Unknown MQTT topic received: %s", topic);
        
        // Clean up PSRAM allocation
        free(message);
    }

    // AWS IoT Commands (transient operations)
    // =======================================

    // reasonCode MUST match the AWS IoT Commands pattern [A-Z0-9_-]+ (uppercase);
    // a lowercase code makes AWS reject the status update. reasonDescription is free text.
    static void _publishCommandStatus(const char* executionId, const char* status,
                                       const char* reasonCode, const char* reasonDescription) {
        char topic[MQTT_TOPIC_BUFFER_SIZE];
        _constructCommandTopic(executionId, "response/json", topic, sizeof(topic));

        SpiRamAllocator allocator;
        JsonDocument doc(&allocator);
        doc["status"] = status;
        if (reasonCode != nullptr) {
            doc["statusReason"]["reasonCode"] = reasonCode;
            if (reasonDescription != nullptr) doc["statusReason"]["reasonDescription"] = reasonDescription;
        }

        if (_publishJsonStreaming(doc, topic)) LOG_DEBUG("Command %s status '%s' published", executionId, status);
        else LOG_WARNING("Failed to publish command %s status '%s'", executionId, status);
    }

    // Parses the executionId from the topic, validates, dispatches the operation
    // and publishes IN_PROGRESS then a terminal status. Runs on the MQTT task
    // (from the RX callback or the dev injection drain) so publishing is safe.
    static void _handleCommandExecution(const char* topic, const char* message) {
        char executionId[NAME_BUFFER_SIZE];
        if (!ShadowLogic::extractExecutionId(topic, executionId, sizeof(executionId))) {
            LOG_WARNING("Could not extract executionId from command topic: %s", topic);
            return;
        }

        SpiRamAllocator allocator;
        JsonDocument doc(&allocator);
        DeserializationError error = deserializeJson(doc, message);
        if (error) {
            LOG_ERROR("Failed to parse command %s payload (%s)", executionId, error.c_str());
            _publishCommandStatus(executionId, "FAILED", "BAD_PAYLOAD", "Could not parse command JSON");
            return;
        }

        const char* operation = doc["operation"].as<const char*>();
        if (operation == nullptr) {
            LOG_WARNING("Command %s missing 'operation'", executionId);
            _publishCommandStatus(executionId, "REJECTED", "MISSING_OPERATION", "No 'operation' field");
            return;
        }

        // Staleness guard. MQTT 3.1.1 carries no server timestamp, so this relies
        // on the command payload providing 'created_at' (unix seconds); absent it,
        // the guard is skipped (logged) - see the cloud contract in doc 07.
        uint64_t createdAt = doc["created_at"] | 0ULL;
        if (ShadowLogic::isCommandStale(createdAt, CustomTime::getUnixTime(), COMMAND_MAX_AGE_SECONDS)) {
            LOG_WARNING("Command %s (%s) is stale (created %llu); rejecting", executionId, operation, createdAt);
            _publishCommandStatus(executionId, "REJECTED", "STALE_COMMAND", "Command older than the staleness window");
            return;
        }
        if (createdAt == 0) LOG_DEBUG("Command %s has no created_at; staleness guard skipped", executionId);

        LOG_INFO("Processing command %s: %s", executionId, operation);
        _publishCommandStatus(executionId, "IN_PROGRESS", nullptr, nullptr);
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
