jibrilsharafi/EnergyMe-Home/source/src/customwifi.cpp

// SPDX-License-Identifier: GPL-3.0-or-later
// Copyright (C) 2025 Jibril Sharafi

#include "customwifi.h"
#include "custometh.h"
#include "customnet.h"
#include "taskprofiler.h"

namespace CustomWifi
{
  static TaskHeartbeat _heartbeat;

  // WiFi connection task variables
  static TaskHandle_t _wifiTaskHandle = NULL;
  
  // Counters
  static uint64_t _lastReconnectAttempt = 0;
  static int32_t _reconnectAttempts = 0; // Increased every disconnection, reset on stable (few minutes) connection
  // Deadline replacing the old blocking delay() after a disconnect: the task must stay
  // responsive during the grace window. 0 means disarmed.
  static uint64_t _disconnectDeadlineMs = 0;
  // The notify wait is shortened while a deadline is armed, so "wait timed out" no longer
  // implies "a full periodic interval elapsed". Gate the periodic check on its own clock.
  static uint64_t _lastPeriodicCheckMs = 0;
  static uint64_t _lastWifiConnectedMillis = 0; // Timestamp when WiFi was last fully connected (for lwIP stabilization)
  static IPAddress _lastMdnsIp; // Last IP for which mDNS was initialized; used to skip rebuild when IP unchanged
  static bool _mdnsInitialized = false;

  // WiFi event notification BITS for task communication. This target's FreeRTOS build sets
  // CONFIG_FREERTOS_TASK_NOTIFICATION_ARRAY_ENTRIES to 1, so there is exactly one 32-bit
  // notification word per task - no second index to hand any event class its own channel.
  // Bits are combined with eSetBits, which OR-accumulates concurrent notifications into
  // that one word, and are all drained together on the next wait. The previous scheme used
  // small sequential values with eSetValueWithOverwrite, where a later event silently
  // replaced an earlier one still waiting to be read: an AP_STADISCONNECTED landing before
  // the task drained a pending GOT_IP could discard it outright, stranding the device in
  // STA_CONNECTING with a working IP address that nothing ever acted on.
  static const uint32_t WIFI_EVENT_SHUTDOWN = (1UL << 0);
  static const uint32_t WIFI_EVENT_CONNECTED = (1UL << 1);
  static const uint32_t WIFI_EVENT_GOT_IP = (1UL << 2);
  static const uint32_t WIFI_EVENT_DISCONNECTED = (1UL << 3);
  static const uint32_t WIFI_EVENT_FORCE_RECONNECT = (1UL << 4);
  static const uint32_t WIFI_EVENT_NEW_CREDENTIALS = (1UL << 5);
  static const uint32_t WIFI_EVENT_AP_START = (1UL << 6);
  static const uint32_t WIFI_EVENT_AP_STACONNECTED = (1UL << 7);
  static const uint32_t WIFI_EVENT_AP_STADISCONNECTED = (1UL << 8);
  static const uint32_t WIFI_EVENT_CREDENTIALS_CLEARED = (1UL << 9);
  // Debug-only: an ARDUINO_EVENT_* this task does not otherwise act on. Best-effort by
  // design, same as the value it replaces - _lastUnknownWifiEvent is a plain overwrite, so a
  // second unknown event before the bit is drained just replaces which one gets logged.
  static const uint32_t WIFI_EVENT_UNKNOWN = (1UL << 10);
  static volatile int32_t _lastUnknownWifiEvent = -1;
  // Pure wake-up: the wired interface changed, so _serviceApLifecycle() (top of the loop)
  // must re-evaluate the AP and the network LED now, not at the next periodic tick.
  static const uint32_t WIFI_EVENT_WIRED_CHANGED = (1UL << 11);
  static const uint32_t WIFI_EVENT_AP_STOP = (1UL << 12); // Log-only: the SoftAP went down

  // Task state management
  static bool _taskShouldRun = false;
  static bool _eventsEnabled = false;
  
  // New credentials storage for async switching
  // To be safe, we should create mutexes around these since they are accessed via a public method
  // But since they are seldom written and read, we can avoid the complexity for now
  static char _pendingSSID[WIFI_SSID_BUFFER_SIZE] = {0};
  static char _pendingPassword[WIFI_PASSWORD_BUFFER_SIZE] = {0};
  static bool _hasPendingCredentials = false;

  // Outcome of the last credential write. setCredentials() returns the moment the request
  // is queued, so the HTTP response is sent before the write is even attempted; the status
  // endpoint reports this so a failed store is visible instead of silently discarded.
  // Lock-free single-word read, same discipline as _publishedState.
  static volatile bool _lastCredentialWriteFailed = false;
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
